BenjaminMoff/MixUS/code/diagrams/App_state_machine.png

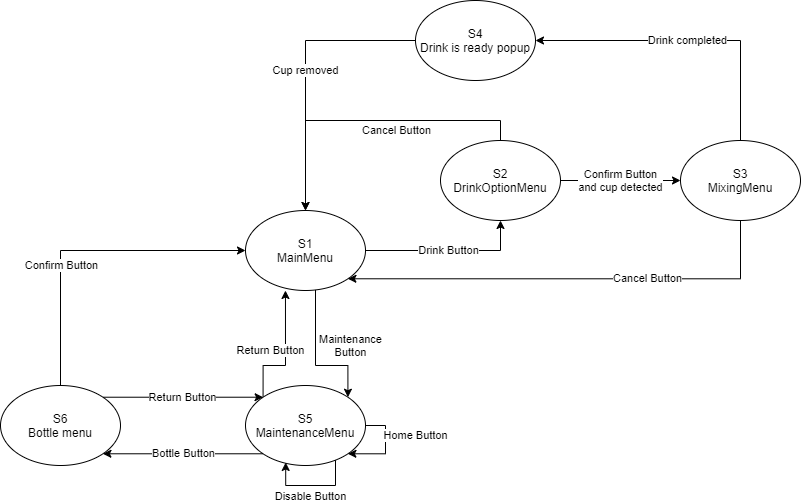
code/diagrams/App_state_machine.png
