BenjaminMoff/MixUS/code/diagrams/Datamodel_class_diagram.png

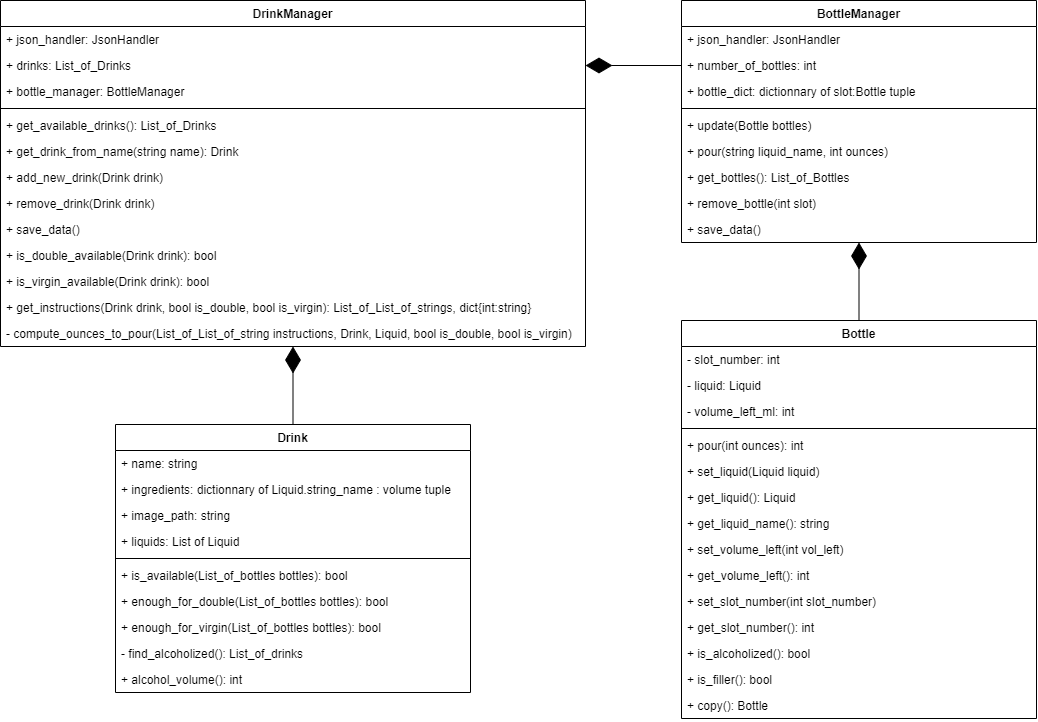
code/diagrams/Datamodel_class_diagram.png
