BenjaminMoff/MixUS/code/diagrams/SerialCommunication_sequence_diagram.png

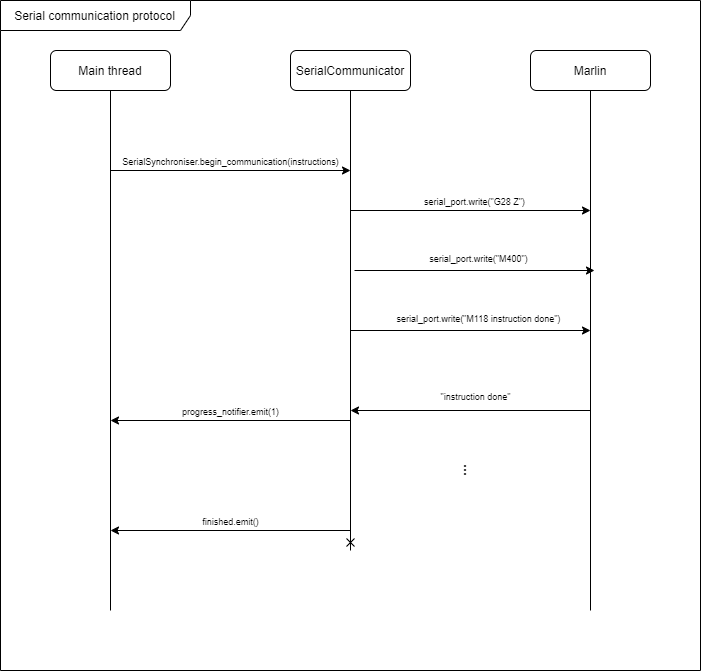
code/diagrams/SerialCommunication_sequence_diagram.png
