BenjaminMoff/MixUS/code/resources/bec-sucre.jpg

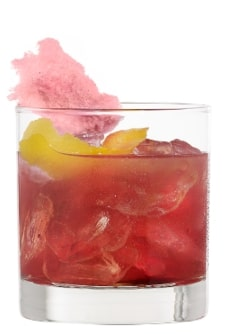
code/resources/bec-sucre.jpg
