BenjaminMoff/MixUS/code/resources/bleu-turquoise.jpg

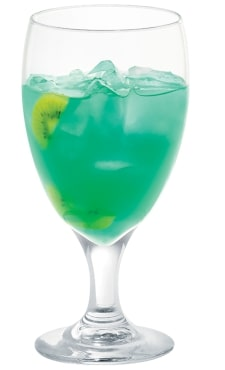
code/resources/bleu-turquoise.jpg
