BenjaminMoff/MixUS/code/resources/delice-gingembre.jpg

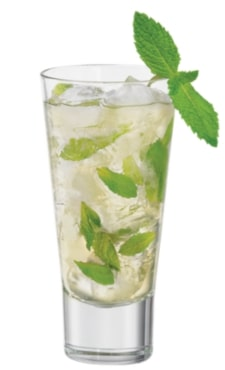
code/resources/delice-gingembre.jpg
