BenjaminMoff/MixUS/code/resources/gin-tonic.jpg

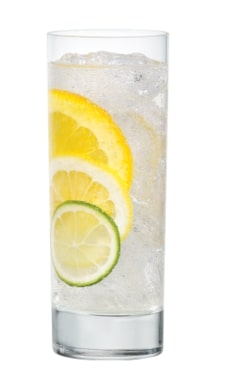
code/resources/gin-tonic.jpg
