BenjaminMoff/MixUS/code/resources/gingembre-etincellant.jpg

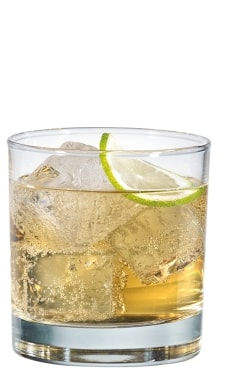
code/resources/gingembre-etincellant.jpg
