BenjaminMoff/MixUS/code/resources/long-island.jpg

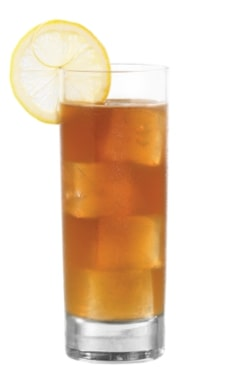
code/resources/long-island.jpg
