BenjaminMoff/MixUS/code/resources/margarita.jpg

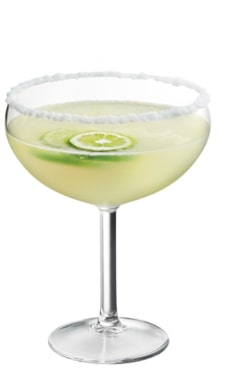
code/resources/margarita.jpg
