BenjaminMoff/MixUS/code/resources/mule-mexicaine.jpg

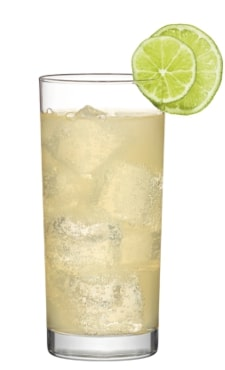
code/resources/mule-mexicaine.jpg
