BenjaminMoff/MixUS/code/resources/orange-fusion.jpg

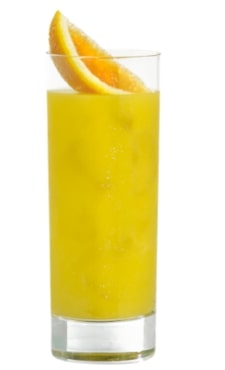
code/resources/orange-fusion.jpg
