BenjaminMoff/MixUS/code/resources/passion-bleue.jpg

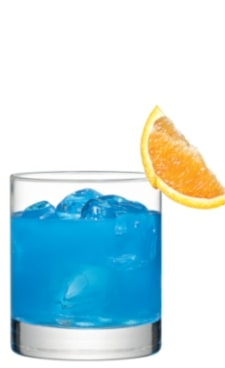
code/resources/passion-bleue.jpg
