BenjaminMoff/MixUS/code/resources/passion-ecarlate.jpg

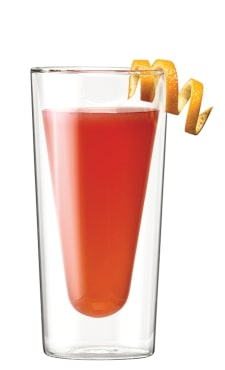
code/resources/passion-ecarlate.jpg
