BenjaminMoff/MixUS/code/resources/rhum-canneberge.jpg

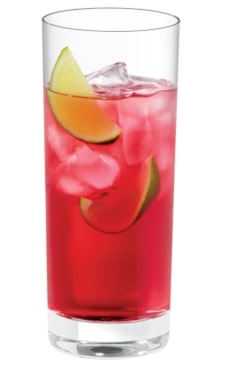
code/resources/rhum-canneberge.jpg
