BenjaminMoff/MixUS/code/resources/rhum-cola.jpg

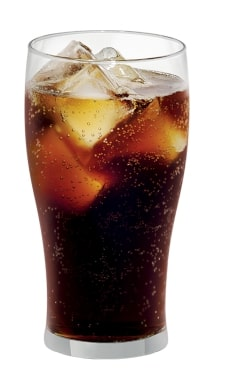
code/resources/rhum-cola.jpg
