BenjaminMoff/MixUS/code/resources/rhum-glace.jpg

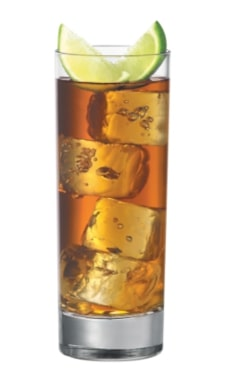
code/resources/rhum-glace.jpg
