BenjaminMoff/MixUS/code/resources/rhum_and_coke.jpg

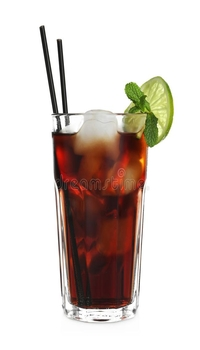
code/resources/rhum_and_coke.jpg
