BenjaminMoff/MixUS/code/resources/tequila-sunrise.jpg

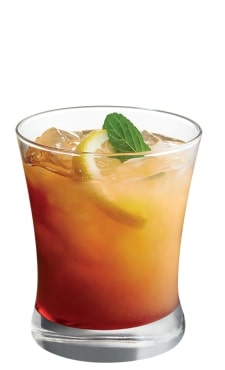
code/resources/tequila-sunrise.jpg
