BenjaminMoff/MixUS/Media Wiki/Home/Axis.png

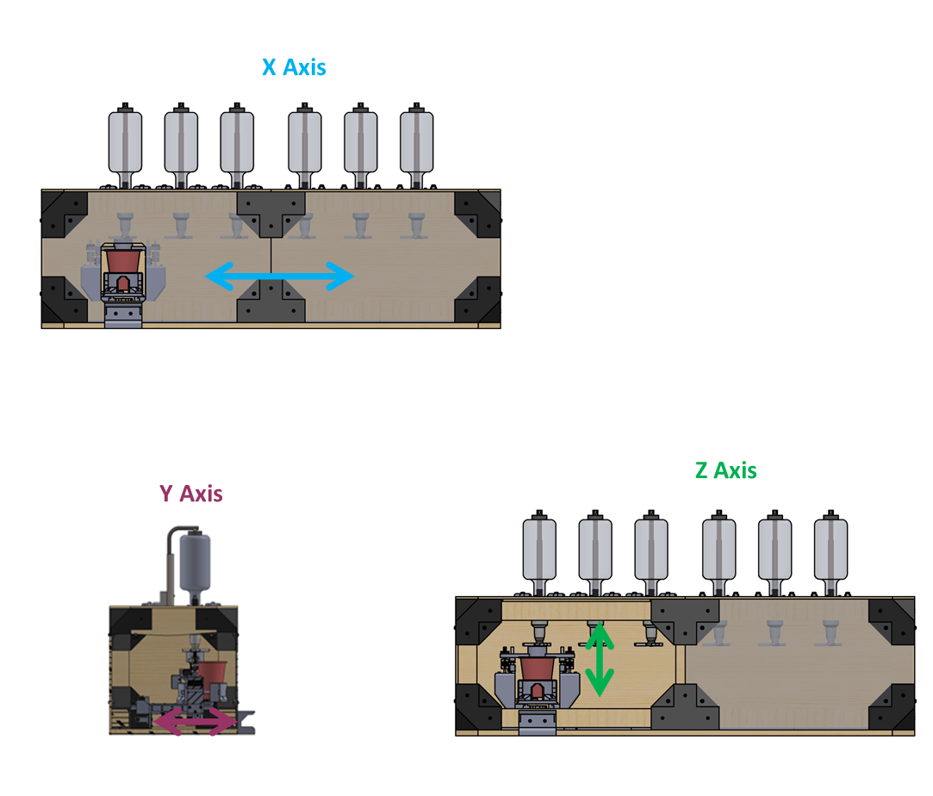
Media Wiki/Home/Axis.png
