BenjaminMoff/MixUS/Media Wiki/Putting it all together/Arduino_IDE_Terminal.gif

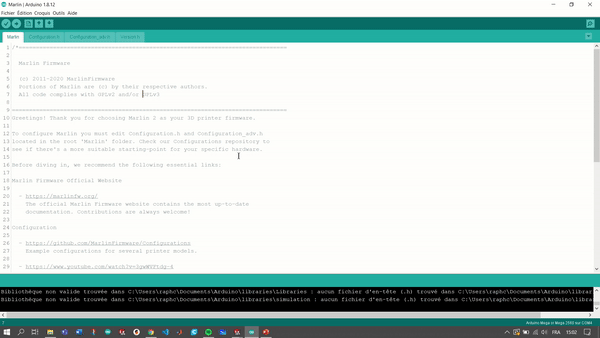
Media Wiki/Putting it all together/Arduino_IDE_Terminal.gif
