BenjaminMoff/MixUS/Media Wiki/Putting it all together/ElectronicConnections.png

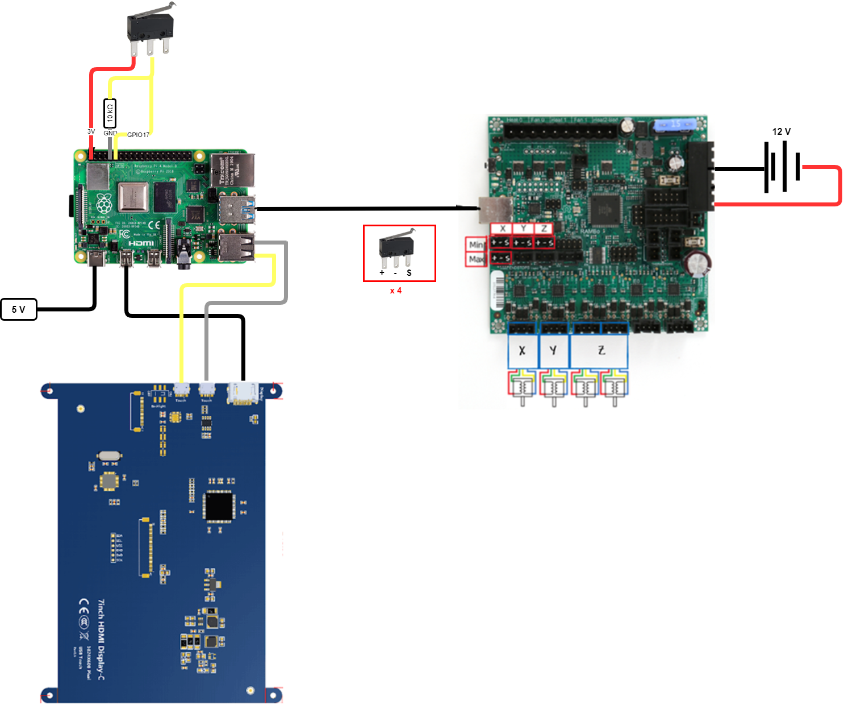
Media Wiki/Putting it all together/ElectronicConnections.png
