BenjaminMoff/MixUS/Mechanical Assembly/CAD/SolidWorks/Frame materials/Drawing/PNG/Drawing_Frame_Acrylic.PNG

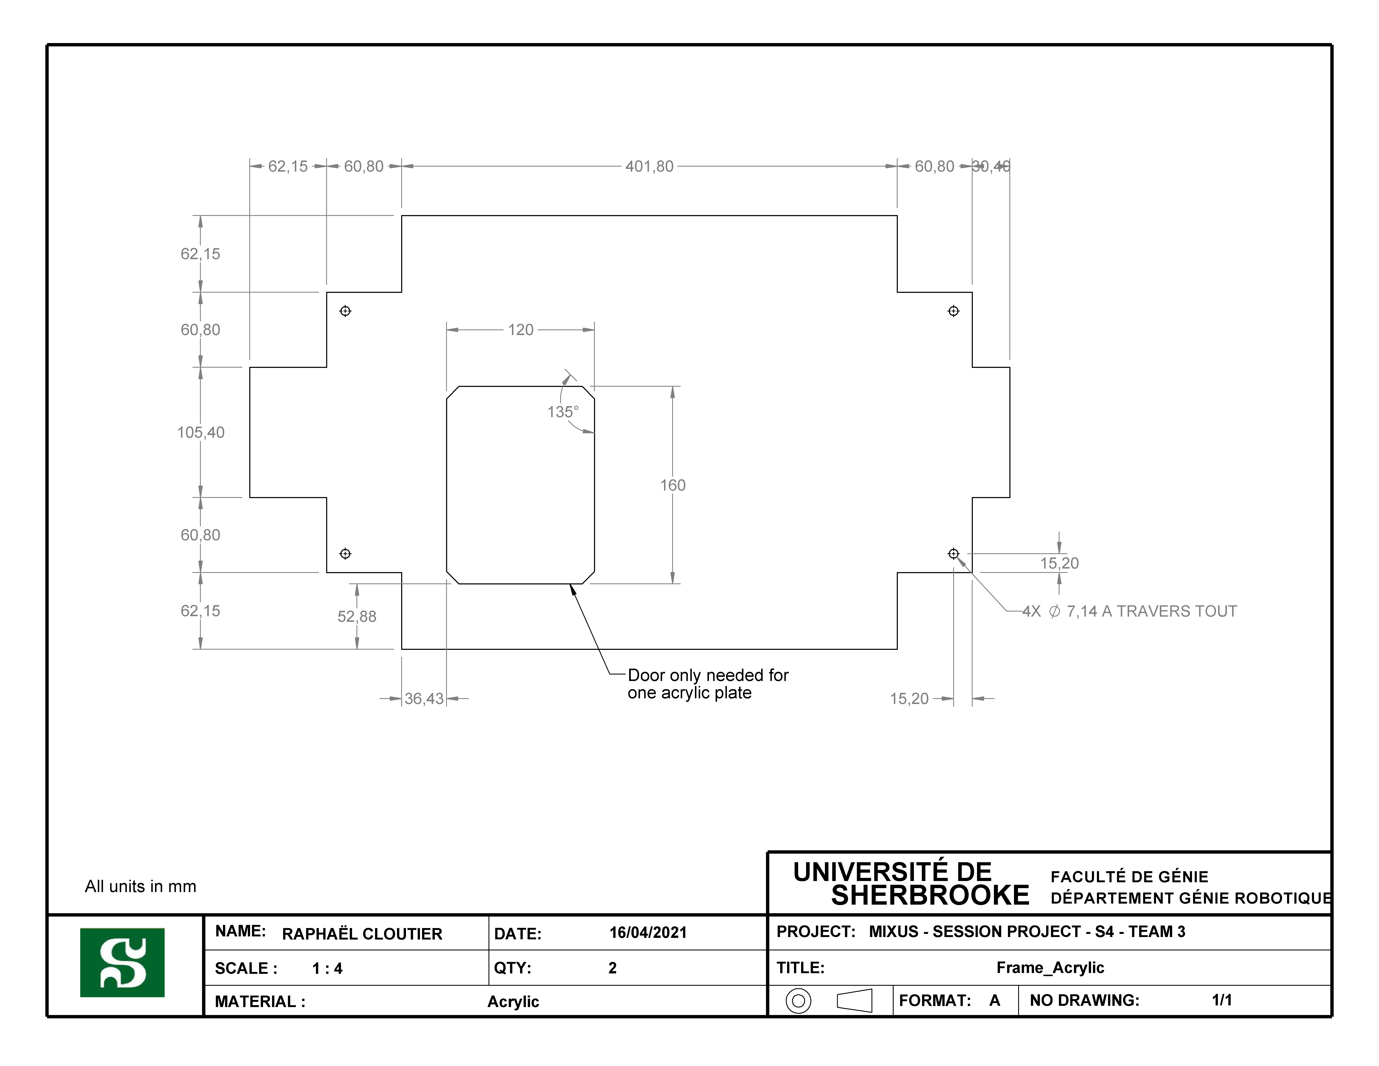
Mechanical Assembly/CAD/SolidWorks/Frame materials/Drawing/PNG/Drawing_Frame_Acrylic.PNG
