BenjaminMoff/MixUS/Mechanical Assembly/CAD/SolidWorks/Frame materials/Drawing/PNG/Drawing_Frame_Side_Plate.PNG

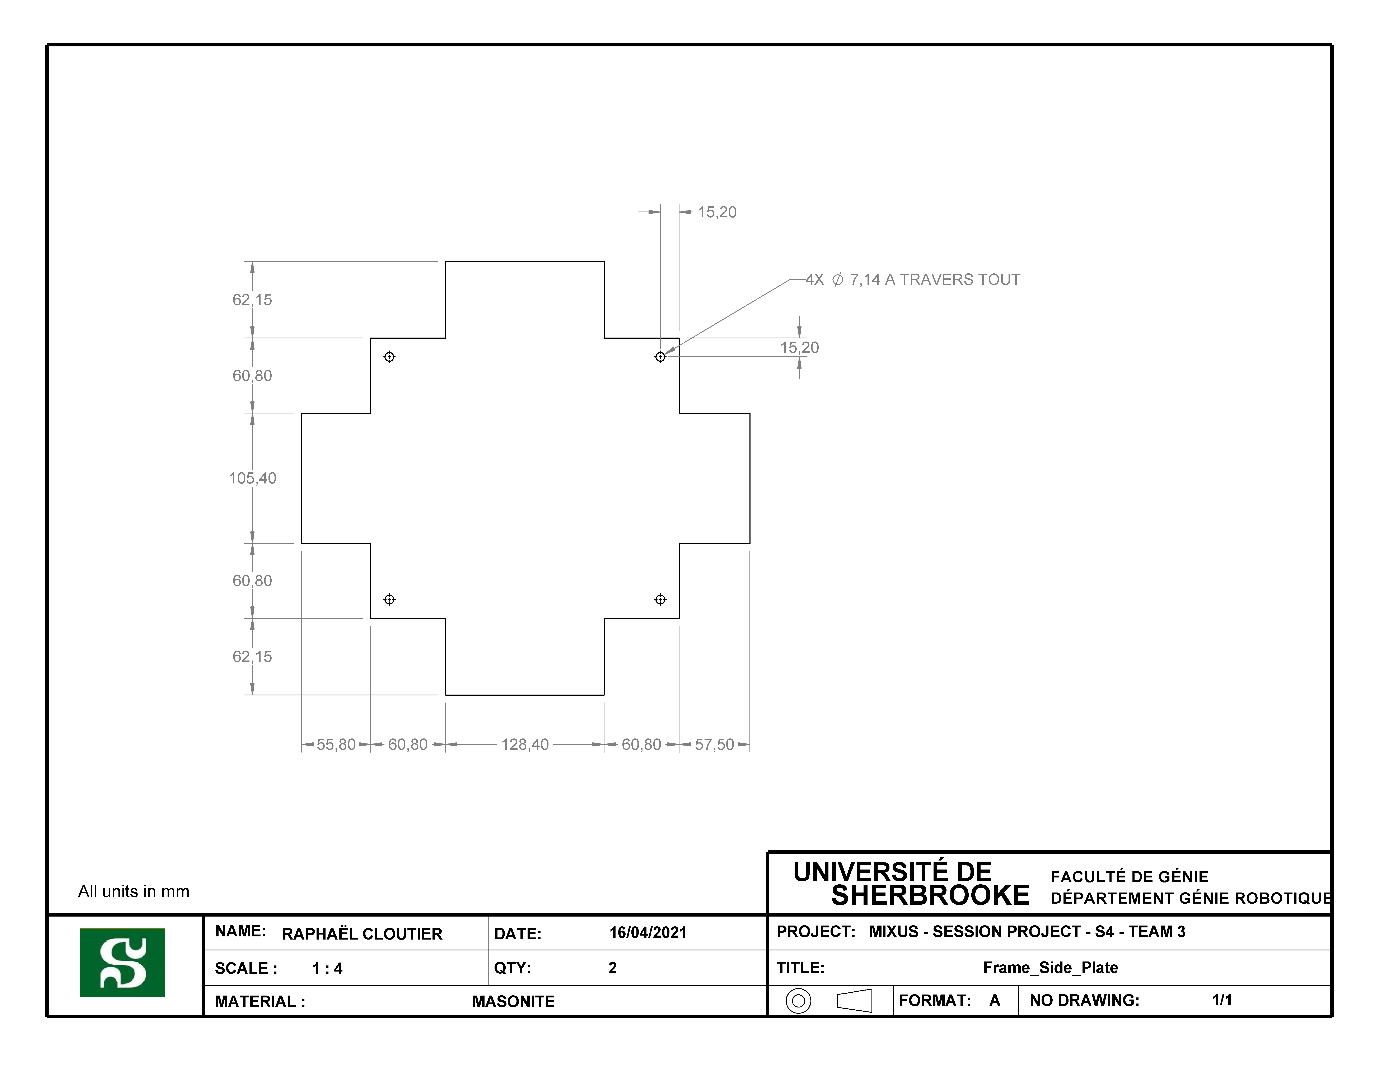
Mechanical Assembly/CAD/SolidWorks/Frame materials/Drawing/PNG/Drawing_Frame_Side_Plate.PNG
