BenjaminMoff/MixUS/Mechanical Assembly/CAD/SolidWorks/Frame materials/Drawing/PNG/Drawing_Frame_Top_Plate_A.PNG

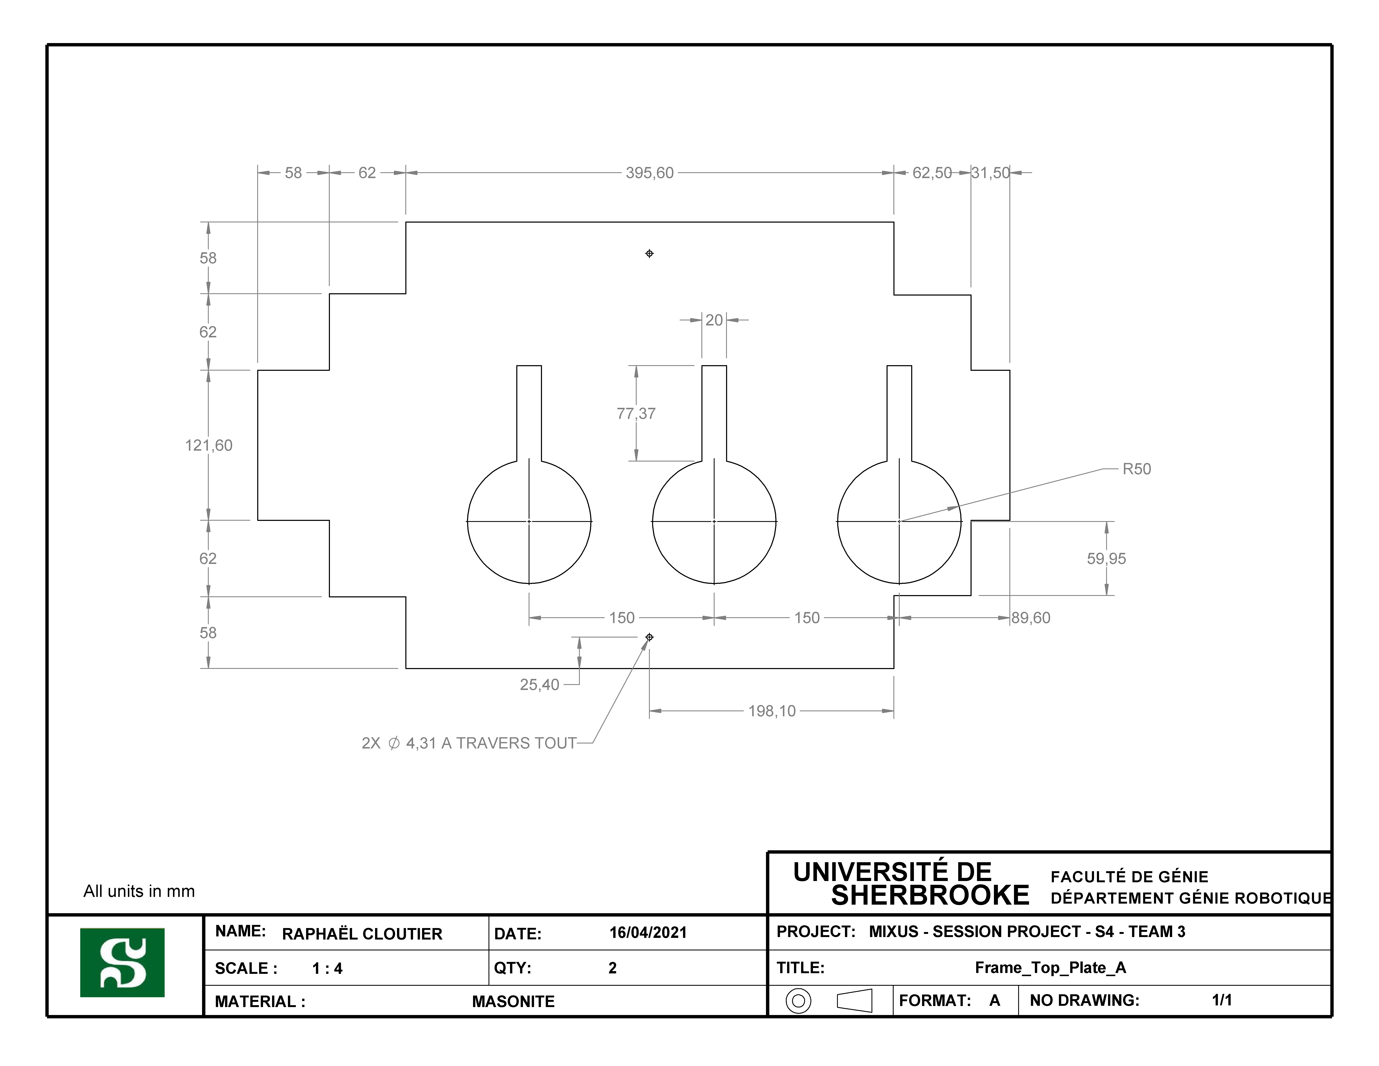
Mechanical Assembly/CAD/SolidWorks/Frame materials/Drawing/PNG/Drawing_Frame_Top_Plate_A.PNG
