BenjaminMoff/MixUS/Mechanical Assembly/CAD/SolidWorks/Frame materials/Drawing/PNG/Drawing_Frame_Top_Plate_B.PNG

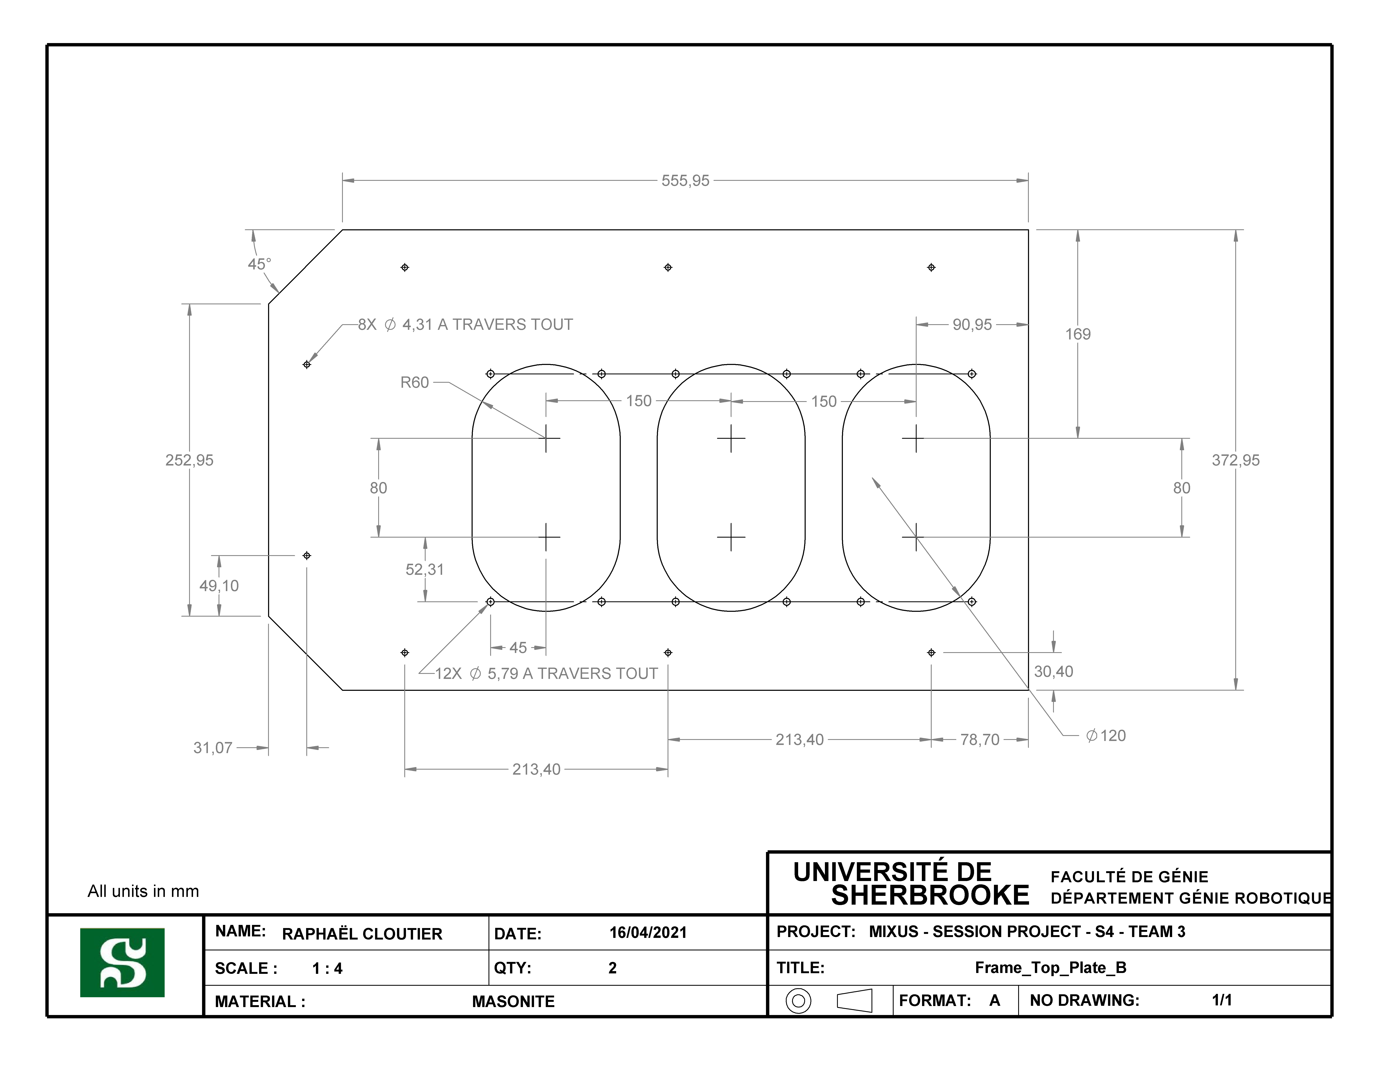
Mechanical Assembly/CAD/SolidWorks/Frame materials/Drawing/PNG/Drawing_Frame_Top_Plate_B.PNG
