BenjaminMoff/MixUS/Mechanical Assembly/CAD/SolidWorks/Insert/M2.5x3.4mm_insert.SLDPRT

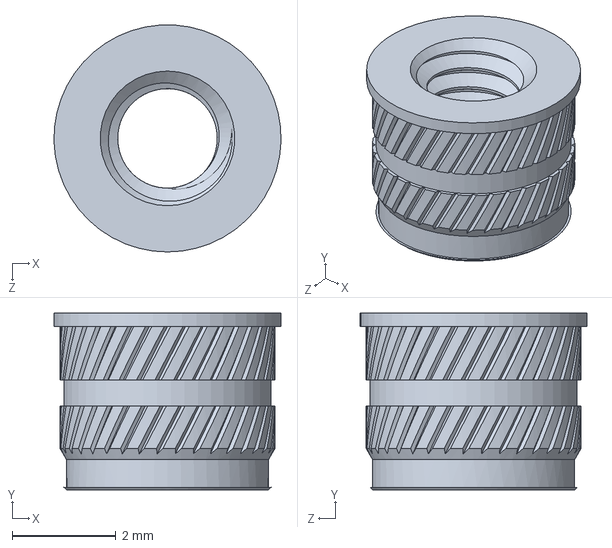
[picture p46: CAD file, 2021-04-10]
Mechanical Assembly/CAD/SolidWorks/Insert/M2.5x3.4mm_insert.SLDPRT
4.37 x 3.40 x 4.37 mm
