BenjaminMoff/MixUS/Mechanical Assembly/CAD/SolidWorks/Laser cut parts/DXF/Frame_Acrylic_Right.DXF

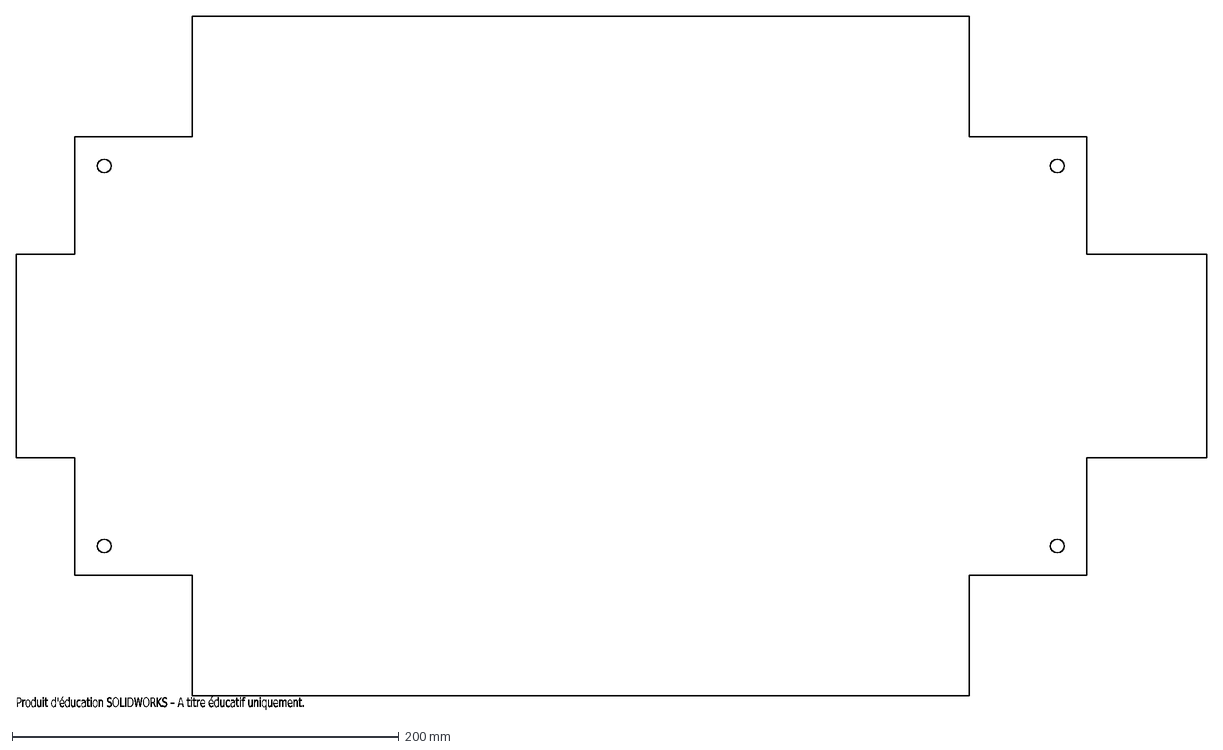
[picture p47: CAD file, 2021-04-10]
Mechanical Assembly/CAD/SolidWorks/Laser cut parts/DXF/Frame_Acrylic_Right.DXF
Produit d'éducation SOLIDWORKS – A titre éducatif uniquement.
