BenjaminMoff/MixUS/Mechanical Assembly/CAD/SolidWorks/Laser cut parts/STL/Frame_Acrylic.SLDPRT

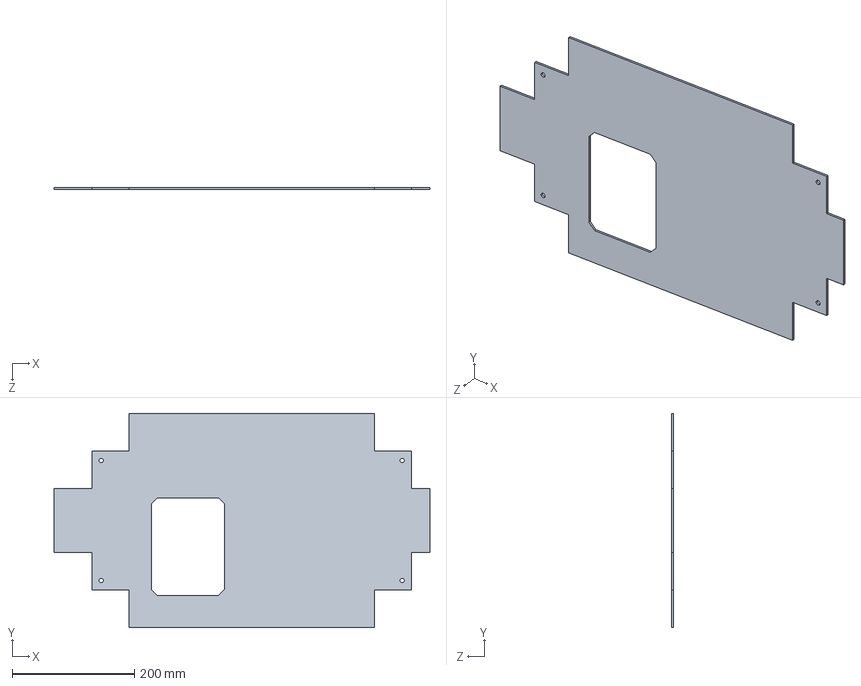
[picture p48: CAD file, 2021-04-10]
Mechanical Assembly/CAD/SolidWorks/Laser cut parts/STL/Frame_Acrylic.SLDPRT
616.0 x 351.3 x 3.30 mm
