BenjaminMoff/MixUS/Mechanical Assembly/CAD/SolidWorks/Nut/6_32_locknut.SLDPRT

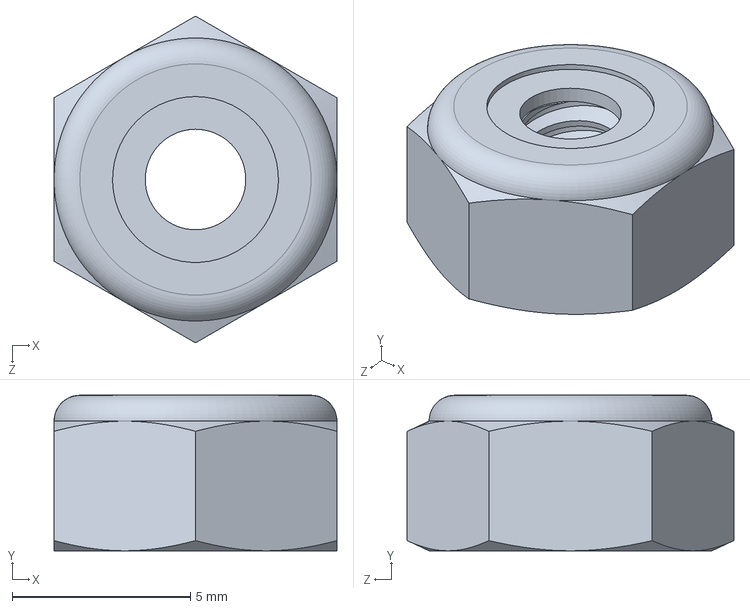
[picture p49: CAD file, 2021-04-10]
Mechanical Assembly/CAD/SolidWorks/Nut/6_32_locknut.SLDPRT
7.94 x 4.37 x 9.17 mm
