BenjaminMoff/MixUS/Mechanical Assembly/CAD/SolidWorks/Others/GT2_pulley.SLDPRT

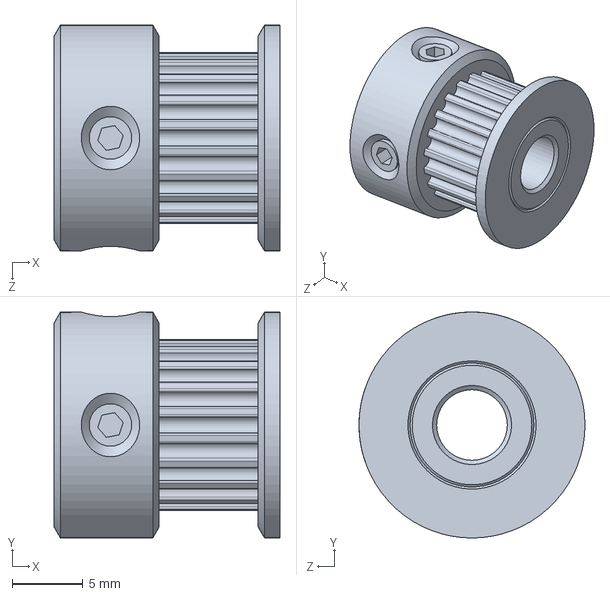
[picture p50: CAD file, 2021-04-10]
Mechanical Assembly/CAD/SolidWorks/Others/GT2_pulley.SLDPRT
16.0 x 16.0 x 16.0 mm
