BenjaminMoff/MixUS/Mechanical Assembly/CAD/SolidWorks/Printed parts/SolidWorks/BottleSup_Removable_Plate_A.SLDPRT

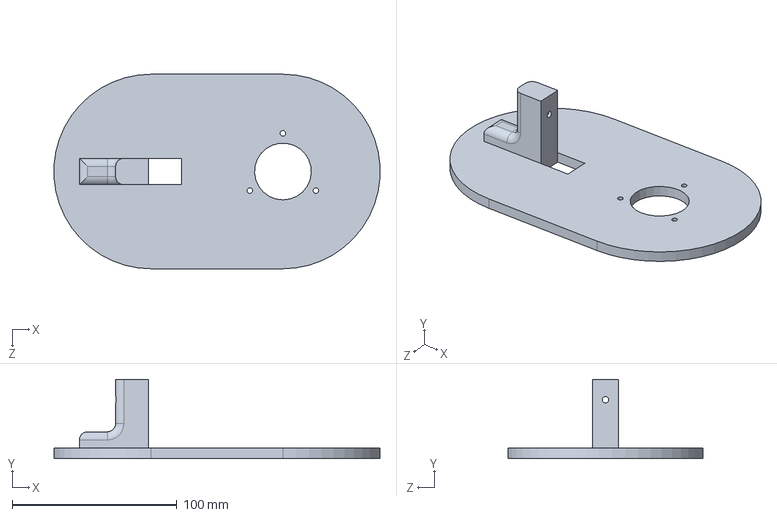
[picture p51: CAD file, 2021-04-10]
Mechanical Assembly/CAD/SolidWorks/Printed parts/SolidWorks/BottleSup_Removable_Plate_A.SLDPRT
197.7 x 48.2 x 118.0 mm
