BenjaminMoff/MixUS/Mechanical Assembly/CAD/SolidWorks/Electronic/40x40x10_DC_Fan.SLDPRT

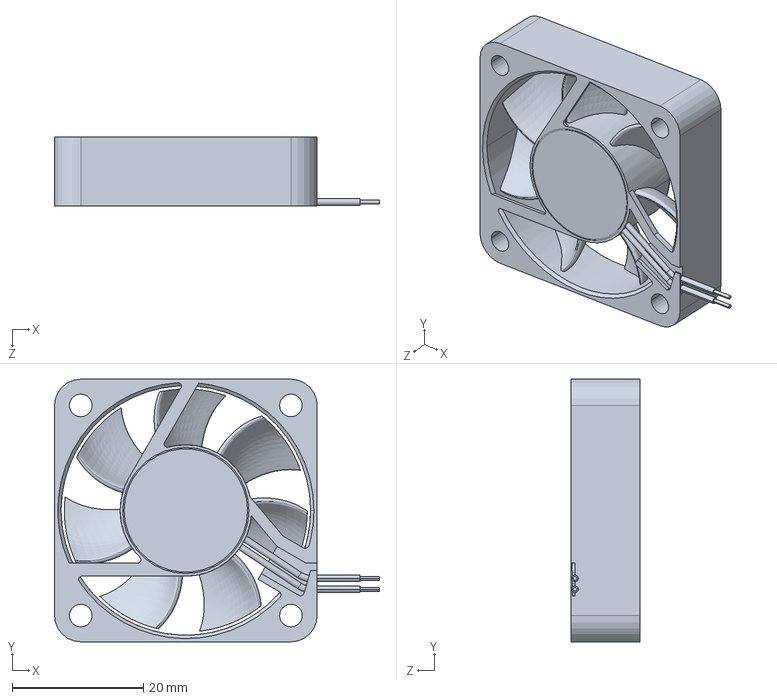
[picture p52: CAD file, 2021-04-10]
Mechanical Assembly/CAD/SolidWorks/Electronic/40x40x10_DC_Fan.SLDPRT
49.5 x 40.0 x 10.5 mm
