BenjaminMoff/MixUS/Mechanical Assembly/CAD/SolidWorks/Frame materials/Frame_top_plate_A.SLDPRT

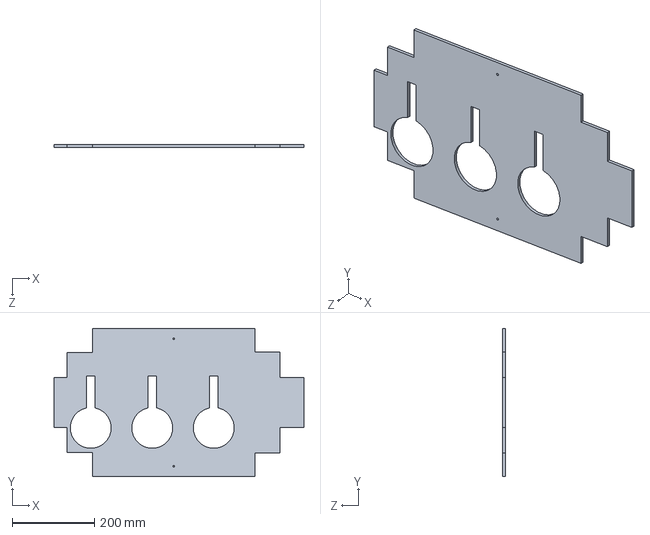
[picture p53: CAD file, 2021-04-10]
Mechanical Assembly/CAD/SolidWorks/Frame materials/Frame_top_plate_A.SLDPRT
609.6 x 361.6 x 6.35 mm
