BenjaminMoff/MixUS/Mechanical Assembly/CAD/SolidWorks/Laser cut parts/DXF/Frame_top_plate_A_Left.DXF

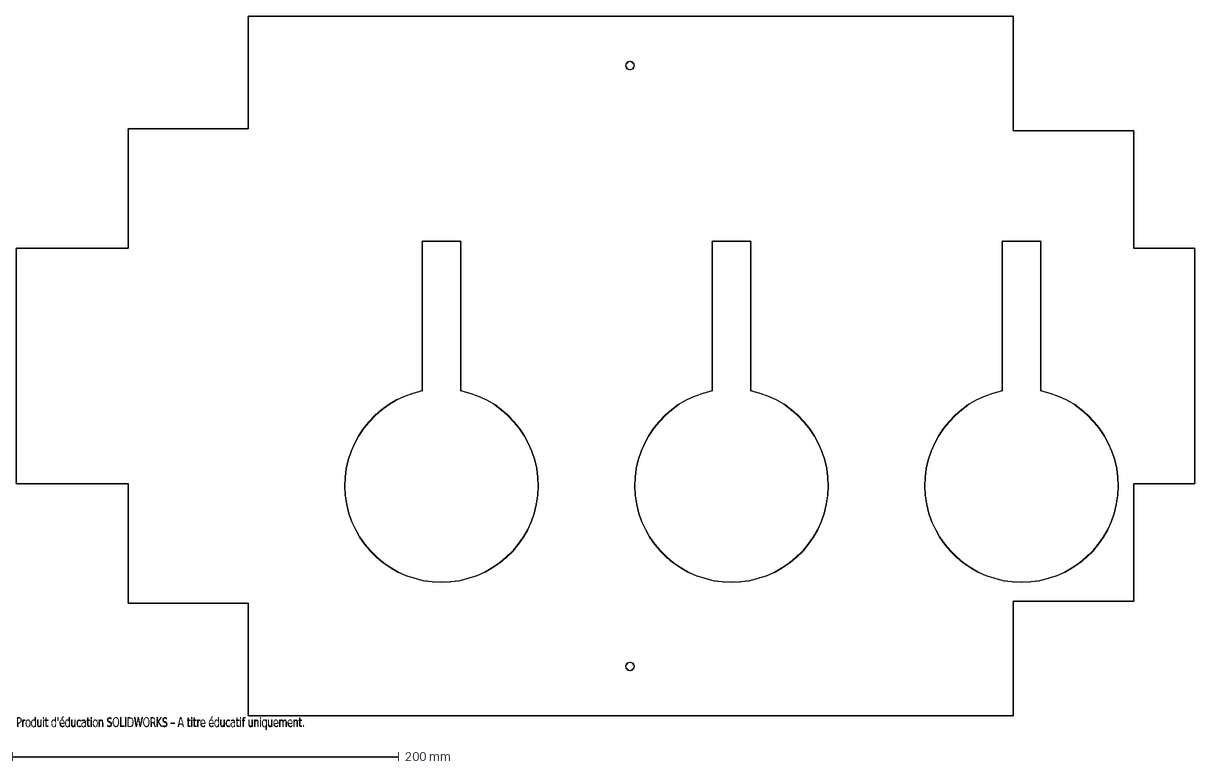
[picture p54: CAD file, 2021-04-10]
Mechanical Assembly/CAD/SolidWorks/Laser cut parts/DXF/Frame_top_plate_A_Left.DXF
Produit d'éducation SOLIDWORKS – A titre éducatif uniquement.
