BenjaminMoff/MixUS/Mechanical Assembly/CAD/SolidWorks/Others/Idler_pulley.SLDPRT

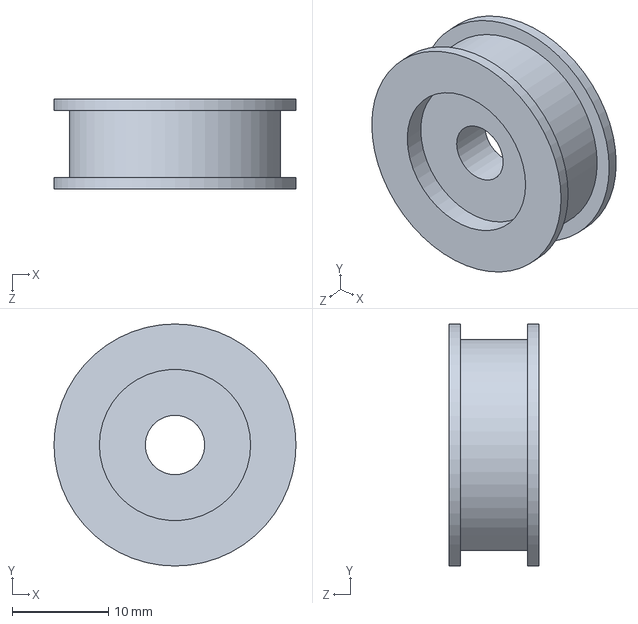
[picture p55: CAD file, 2021-04-10]
Mechanical Assembly/CAD/SolidWorks/Others/Idler_pulley.SLDPRT
25.2 x 25.2 x 9.40 mm
