BenjaminMoff/MixUS/Mechanical Assembly/CAD/SolidWorks/Printed parts/SolidWorks/Y_Support_rail.SLDPRT

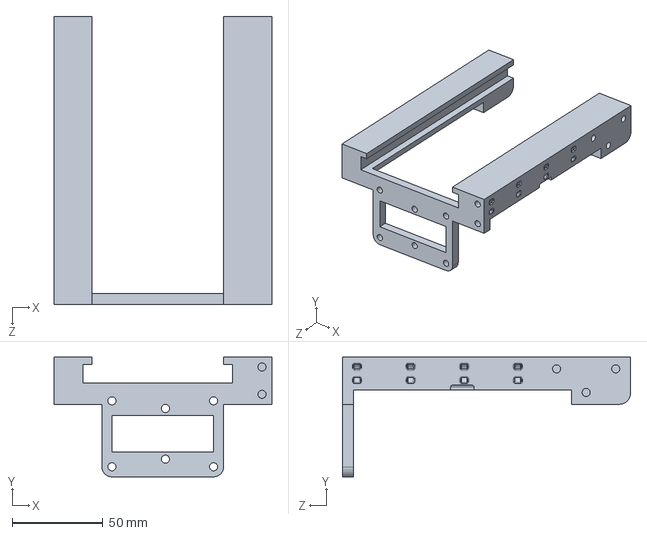
[picture p56: CAD file, 2021-04-10]
Mechanical Assembly/CAD/SolidWorks/Printed parts/SolidWorks/Y_Support_rail.SLDPRT
120.0 x 66.0 x 158.6 mm
