BenjaminMoff/MixUS/Mechanical Assembly/CAD/SolidWorks/Frame materials/Frame_Side_Plate.SLDPRT

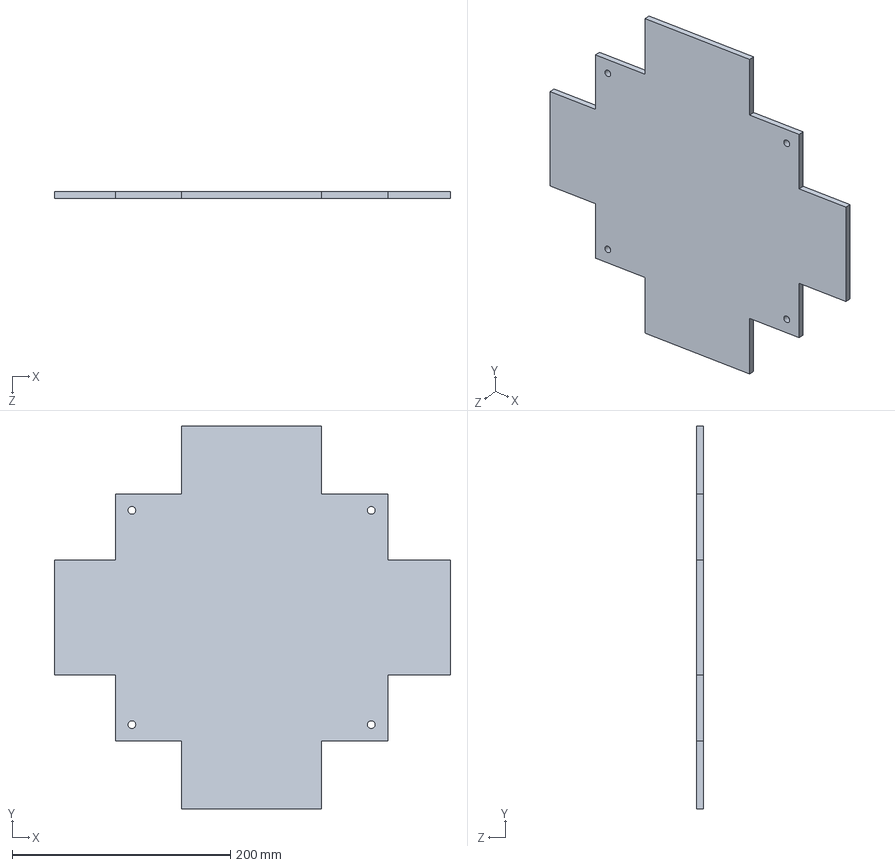
[picture p57: CAD file, 2021-04-10]
Mechanical Assembly/CAD/SolidWorks/Frame materials/Frame_Side_Plate.SLDPRT
363.3 x 351.3 x 6.35 mm
