BenjaminMoff/MixUS/Mechanical Assembly/CAD/SolidWorks/Others/Bottle_Support_TubeB.SLDPRT

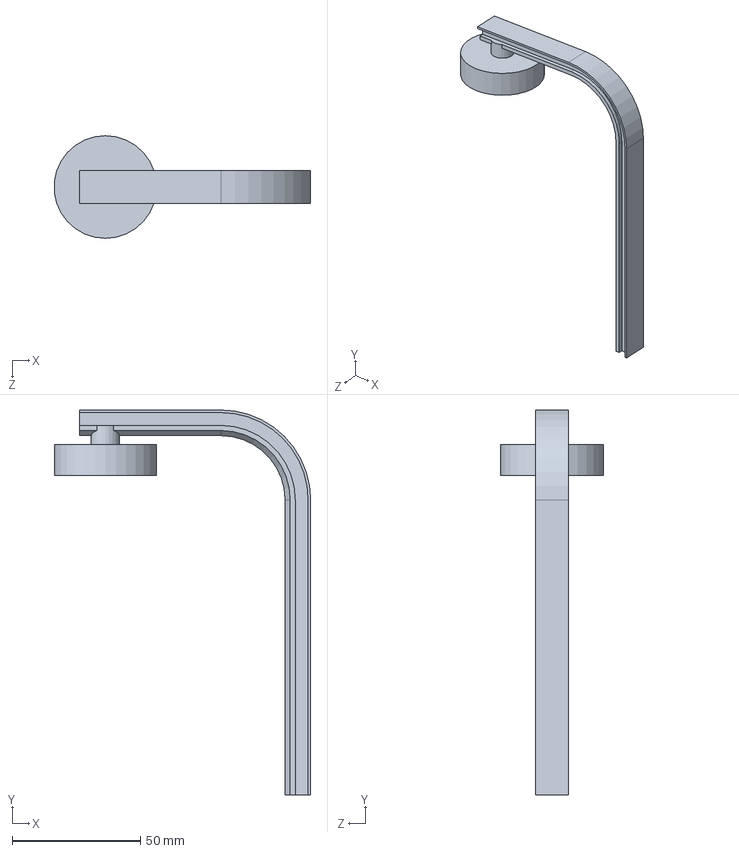
[picture p59: CAD file, 2021-04-10]
Mechanical Assembly/CAD/SolidWorks/Others/Bottle_Support_TubeB.SLDPRT
99.9 x 150.0 x 40.0 mm
