BenjaminMoff/MixUS/Mechanical Assembly/CAD/SolidWorks/Printed parts/SolidWorks/Y_Glass_holder.SLDPRT

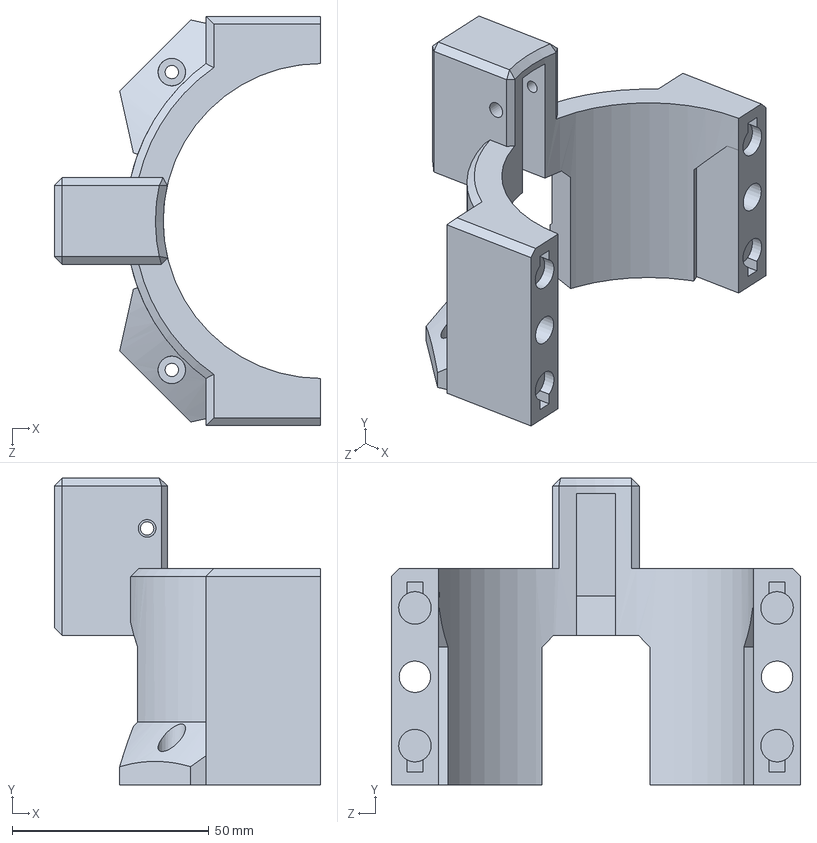
[picture p60: CAD file, 2021-04-10]
Mechanical Assembly/CAD/SolidWorks/Printed parts/SolidWorks/Y_Glass_holder.SLDPRT
67.7 x 78.0 x 104.0 mm
