BenjaminMoff/MixUS/Mechanical Assembly/CAD/SolidWorks/Printed parts/STL/Y_Wheel_bracket_symmetry.STL

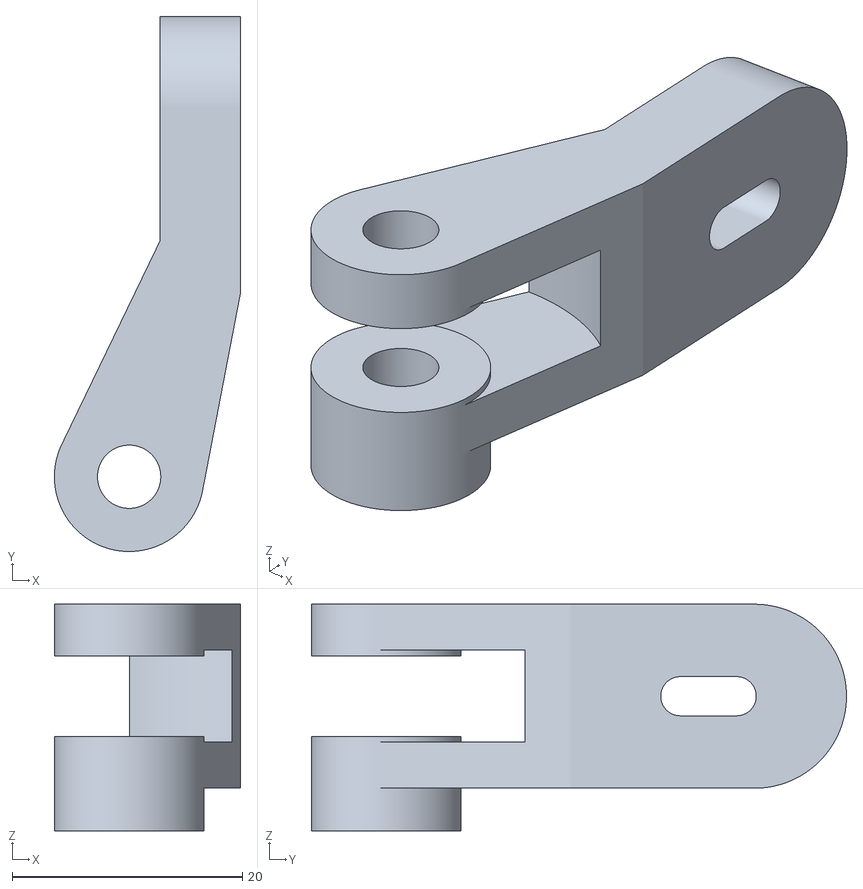
[picture p61: CAD file, 2021-04-10]
Mechanical Assembly/CAD/SolidWorks/Printed parts/STL/Y_Wheel_bracket_symmetry.STL
16.2 x 46.5 x 19.7
