BenjaminMoff/MixUS/Mechanical Assembly/CAD/SolidWorks/Electronic/Nema17.SLDPRT

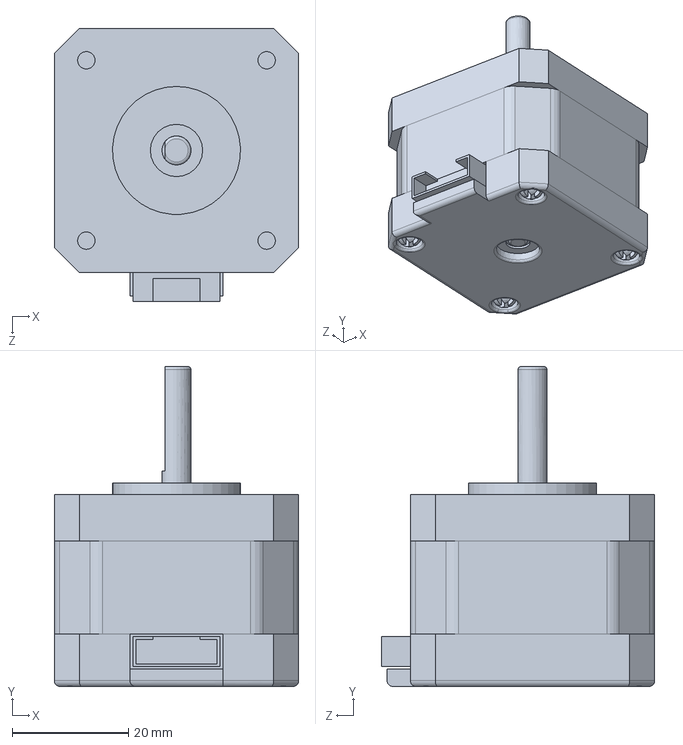
[picture p62: CAD file, 2021-04-10]
Mechanical Assembly/CAD/SolidWorks/Electronic/Nema17.SLDPRT
42.0 x 55.0 x 47.0 mm
