BenjaminMoff/MixUS/Mechanical Assembly/CAD/SolidWorks/Frame materials/Frame_Back_Plate.SLDPRT

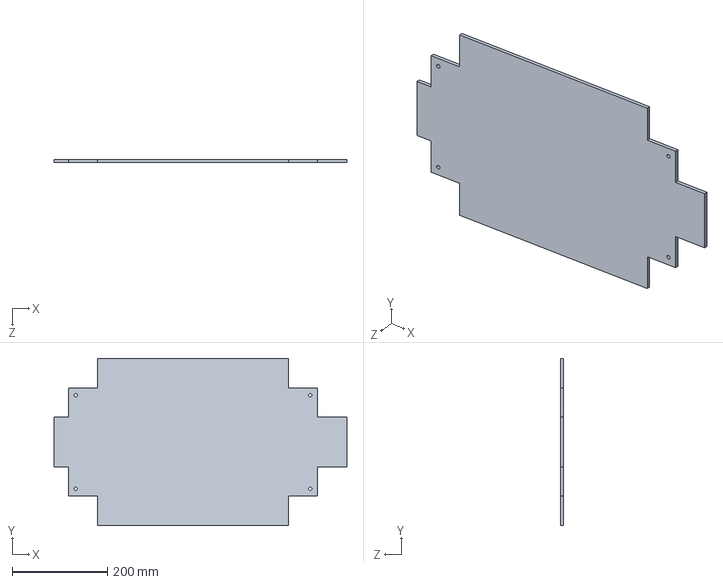
[picture p63: CAD file, 2021-04-10]
Mechanical Assembly/CAD/SolidWorks/Frame materials/Frame_Back_Plate.SLDPRT
616.0 x 351.3 x 6.35 mm
