BenjaminMoff/MixUS/Mechanical Assembly/CAD/SolidWorks/Laser cut parts/DXF/Frame_top_plate_B_Left.DXF

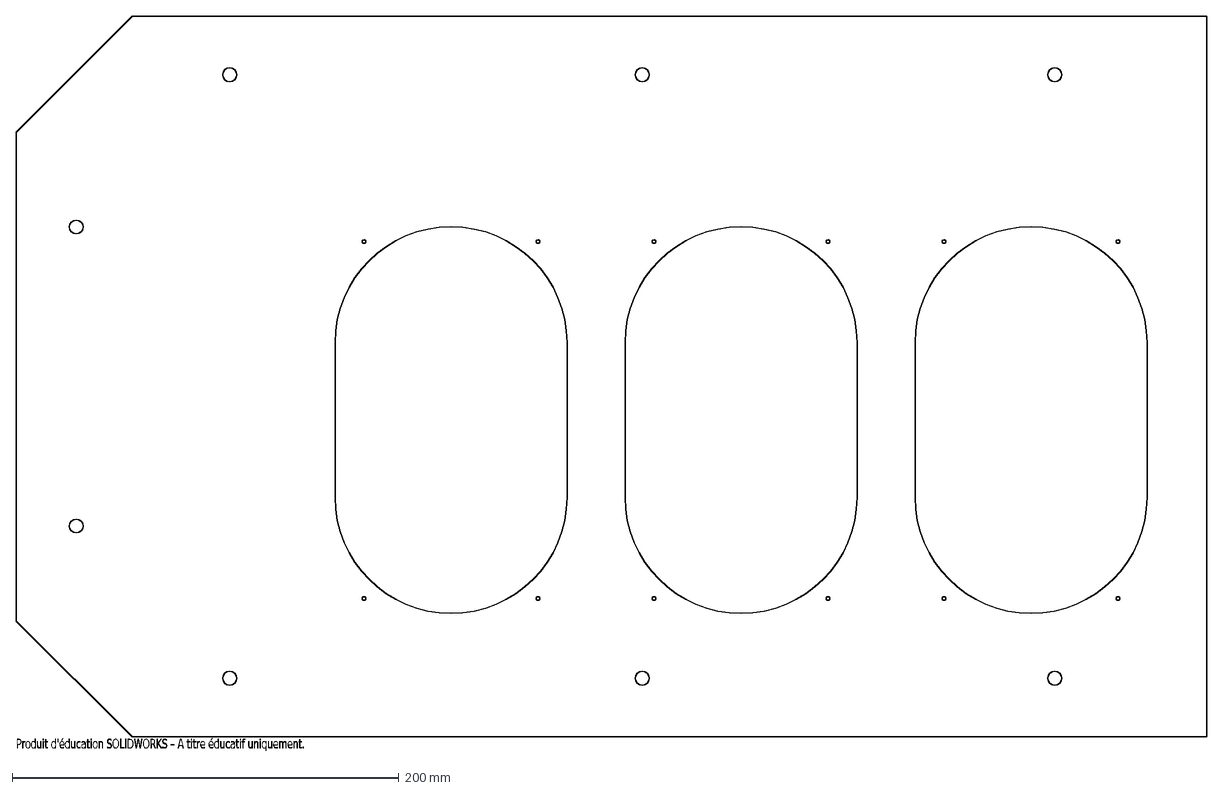
[picture p64: CAD file, 2021-04-10]
Mechanical Assembly/CAD/SolidWorks/Laser cut parts/DXF/Frame_top_plate_B_Left.DXF
Produit d'éducation SOLIDWORKS – A titre éducatif uniquement.
