BenjaminMoff/MixUS/Mechanical Assembly/CAD/SolidWorks/Printed parts/SolidWorks/X_V_Wheel_spacer.SLDPRT

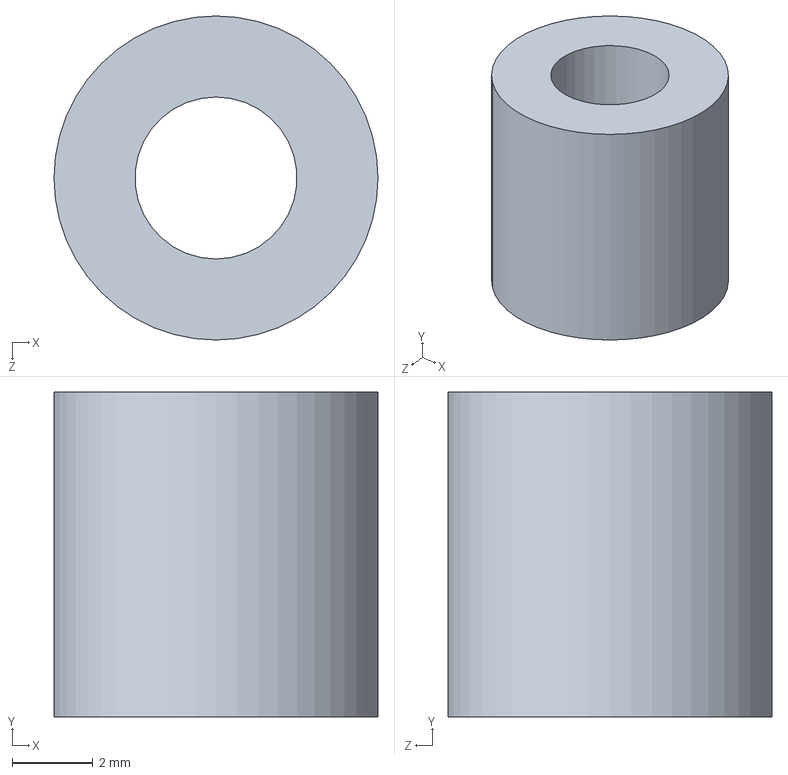
[picture p65: CAD file, 2021-04-10]
Mechanical Assembly/CAD/SolidWorks/Printed parts/SolidWorks/X_V_Wheel_spacer.SLDPRT
8.00 x 8.02 x 8.00 mm
