BenjaminMoff/MixUS/Mechanical Assembly/CAD/SolidWorks/Electronic/Extra_long_male_header_pin.SLDPRT

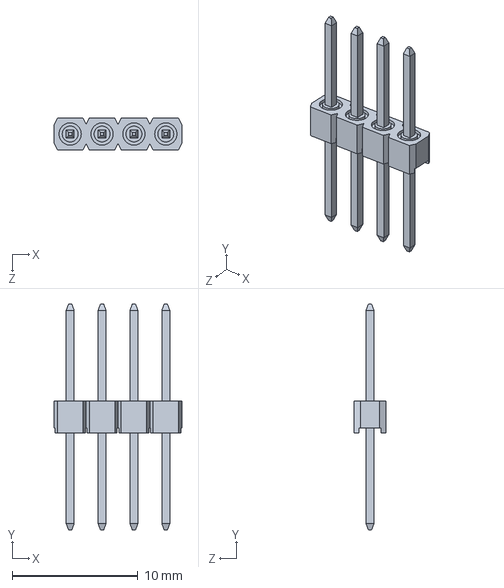
[picture p66: CAD file, 2021-04-10]
Mechanical Assembly/CAD/SolidWorks/Electronic/Extra_long_male_header_pin.SLDPRT
10.2 x 18.0 x 2.54 mm
