BenjaminMoff/MixUS/Mechanical Assembly/CAD/SolidWorks/Laser cut parts/DXF/Frame_Side_Plate.DXF

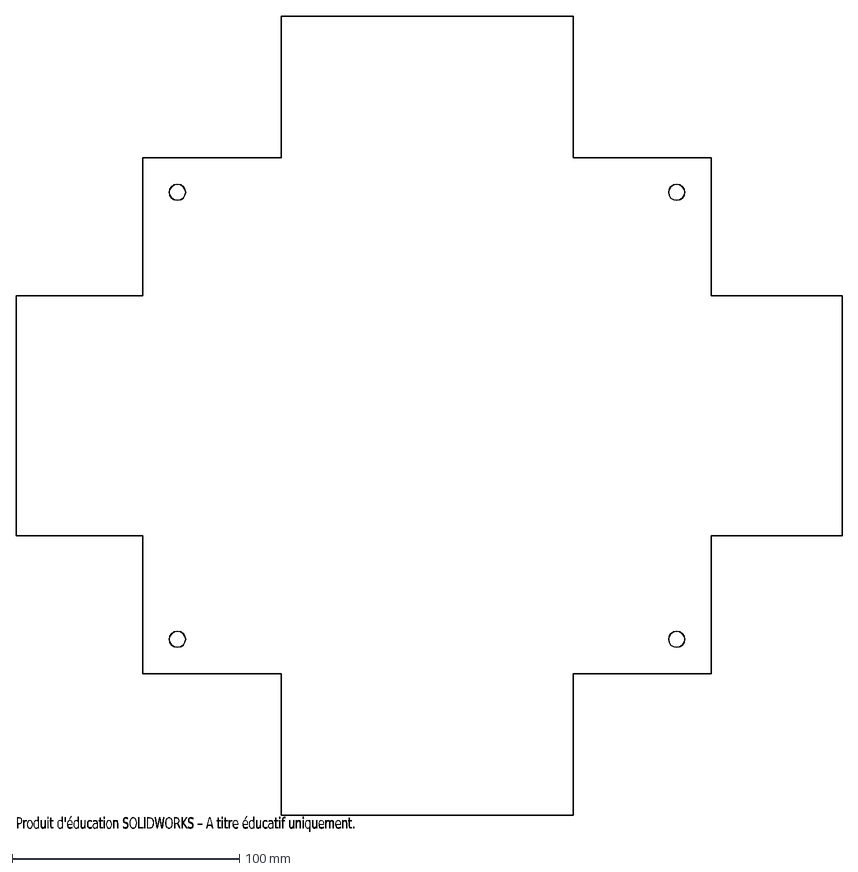
[picture p67: CAD file, 2021-04-10]
Mechanical Assembly/CAD/SolidWorks/Laser cut parts/DXF/Frame_Side_Plate.DXF
Produit d'éducation SOLIDWORKS – A titre éducatif uniquement.
