BenjaminMoff/MixUS/Mechanical Assembly/CAD/SolidWorks/Printed parts/SolidWorks/Y_Extern_slider_support.SLDPRT

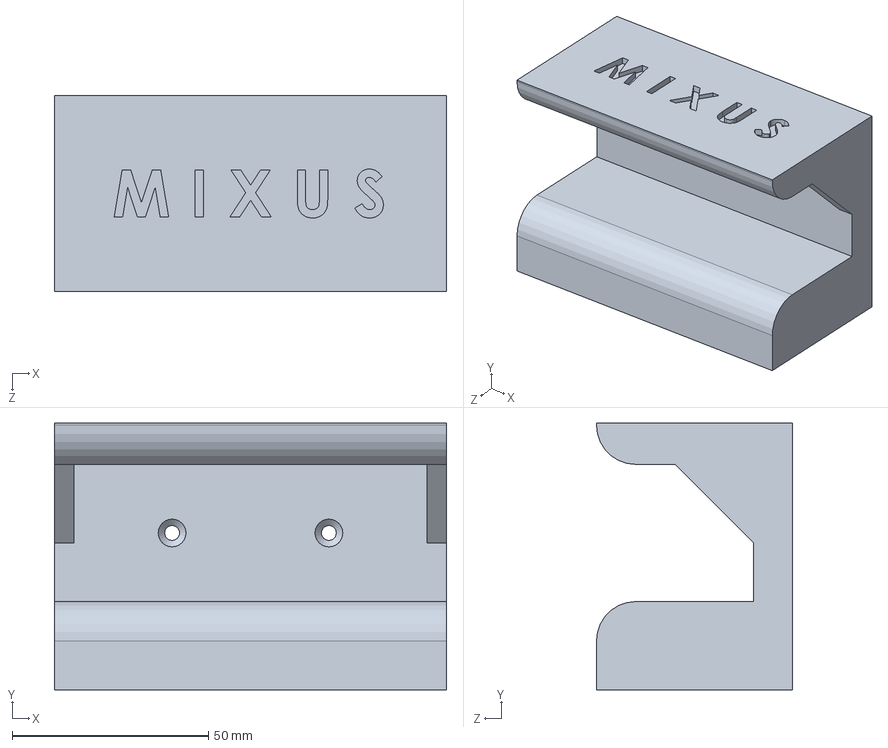
[picture p68: CAD file, 2021-04-10]
Mechanical Assembly/CAD/SolidWorks/Printed parts/SolidWorks/Y_Extern_slider_support.SLDPRT
100.0 x 68.0 x 50.0 mm
