BenjaminMoff/MixUS/Mechanical Assembly/CAD/SolidWorks/Printed parts/STL/Frame_Corner_Wood_Side_symmetry.STL

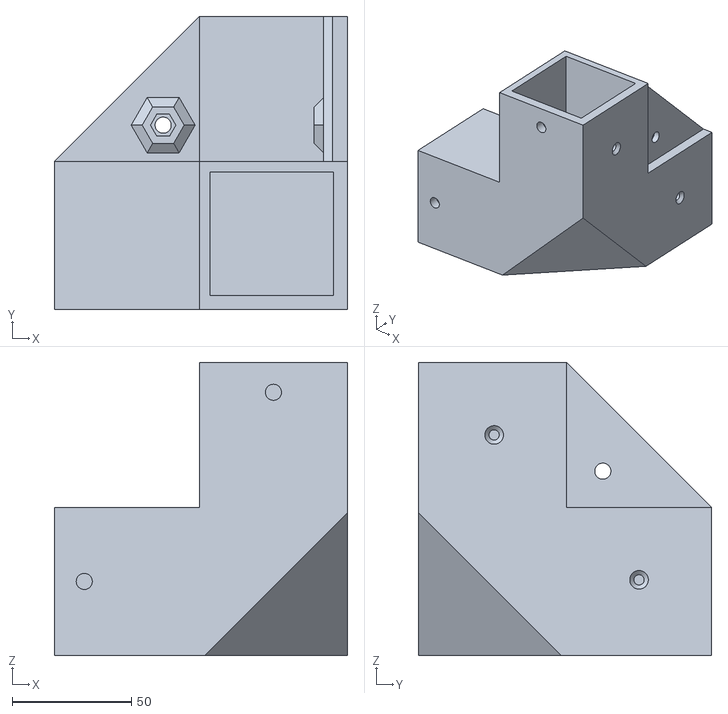
[picture p69: CAD file, 2021-04-10]
Mechanical Assembly/CAD/SolidWorks/Printed parts/STL/Frame_Corner_Wood_Side_symmetry.STL
123.0 x 123.0 x 123.0
