BenjaminMoff/MixUS/Mechanical Assembly/CAD/SolidWorks/Frame materials/Frame_top_plate_B.SLDPRT

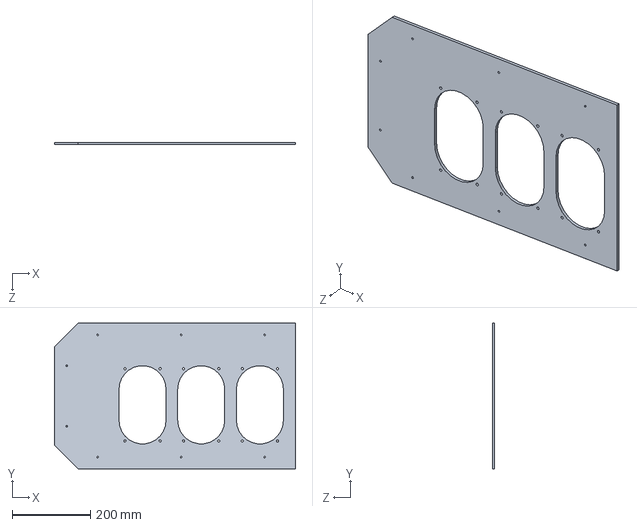
[picture p70: CAD file, 2021-04-10]
Mechanical Assembly/CAD/SolidWorks/Frame materials/Frame_top_plate_B.SLDPRT
616.0 x 372.9 x 6.35 mm
