BenjaminMoff/MixUS/Mechanical Assembly/CAD/SolidWorks/Others/5_to_8_mm_coupler.SLDPRT

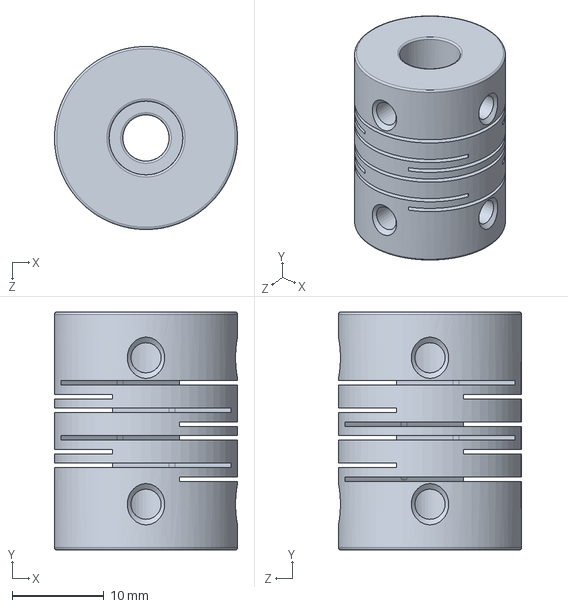
[picture p72: CAD file, 2021-04-10]
Mechanical Assembly/CAD/SolidWorks/Others/5_to_8_mm_coupler.SLDPRT
20.0 x 26.0 x 20.0 mm
