BenjaminMoff/MixUS/Mechanical Assembly/CAD/SolidWorks/Printed parts/SolidWorks/Y_Glass_Holder_Rod.SLDPRT

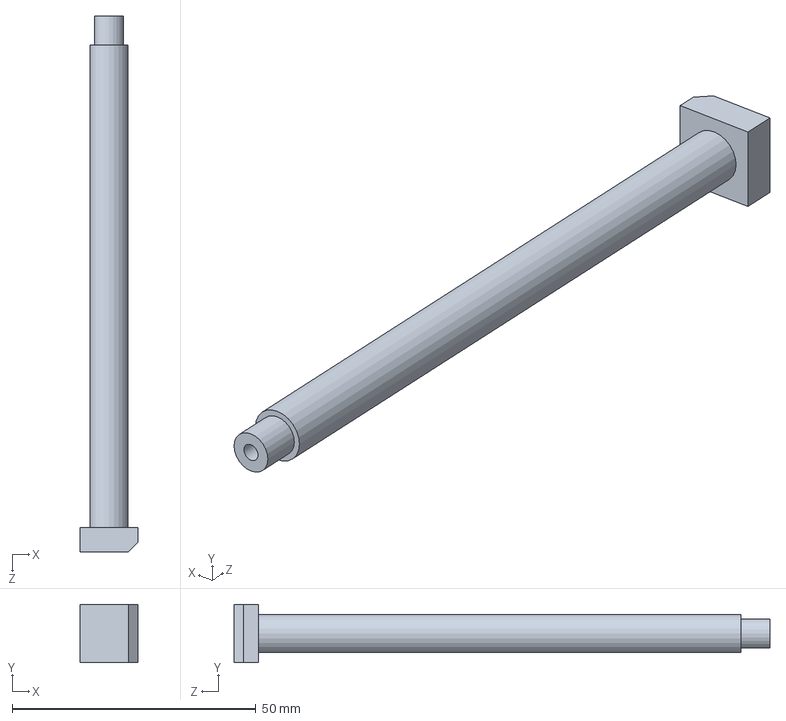
[picture p73: CAD file, 2021-04-10]
Mechanical Assembly/CAD/SolidWorks/Printed parts/SolidWorks/Y_Glass_Holder_Rod.SLDPRT
12.0 x 12.0 x 110.0 mm
