BenjaminMoff/MixUS/Mechanical Assembly/CAD/SolidWorks/Printed parts/STL/Frame_Top_Center_Beam_Bracket_plexi_side.STL

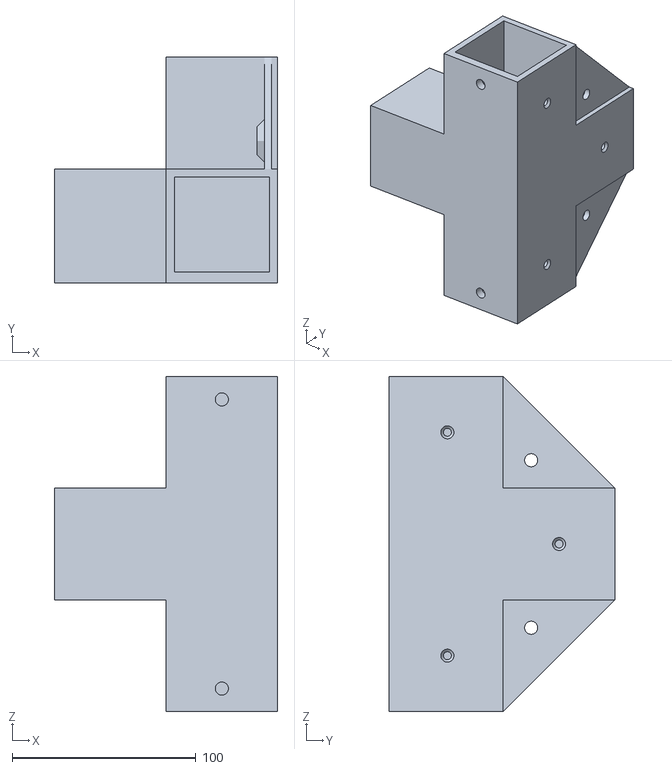
[picture p74: CAD file, 2021-04-10]
Mechanical Assembly/CAD/SolidWorks/Printed parts/STL/Frame_Top_Center_Beam_Bracket_plexi_side.STL
121.6 x 123.0 x 182.4
