BenjaminMoff/MixUS/Mechanical Assembly/CAD/SolidWorks/Frame materials/Frame_Bottom_Plate.SLDPRT

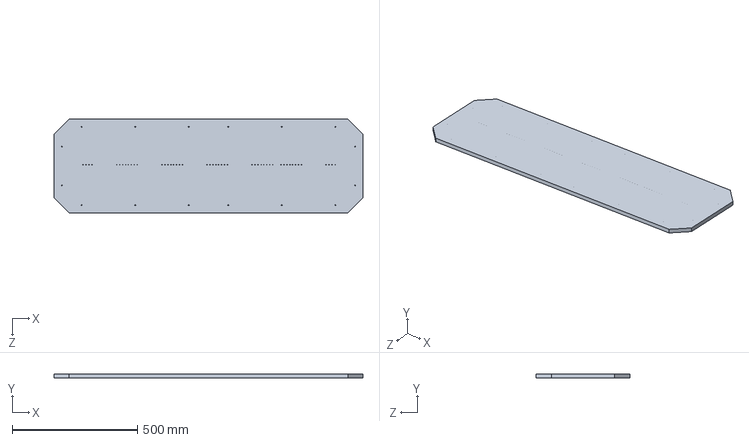
[picture p75: CAD file, 2021-04-10]
Mechanical Assembly/CAD/SolidWorks/Frame materials/Frame_Bottom_Plate.SLDPRT
1231.9 x 15.9 x 372.9 mm
