BenjaminMoff/MixUS/Mechanical Assembly/CAD/SolidWorks/Others/608zz_ball_bearing.SLDPRT

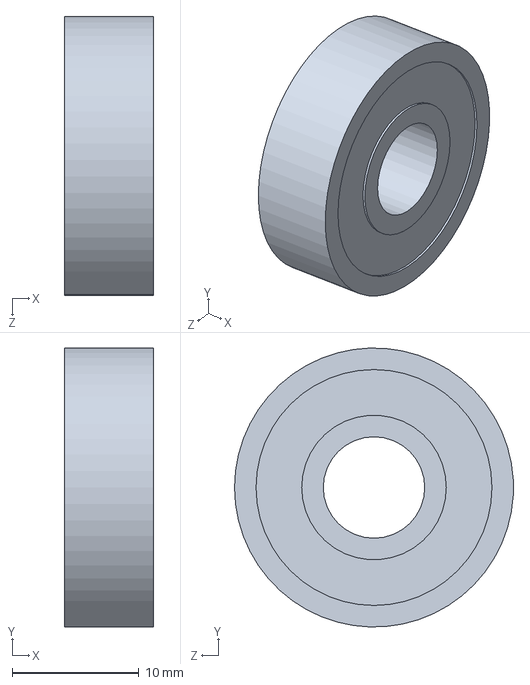
[picture p77: CAD file, 2021-04-10]
Mechanical Assembly/CAD/SolidWorks/Others/608zz_ball_bearing.SLDPRT
7.00 x 22.0 x 22.0 mm
