BenjaminMoff/MixUS/Mechanical Assembly/CAD/SolidWorks/Printed parts/SolidWorks/Z_Pusher.SLDPRT

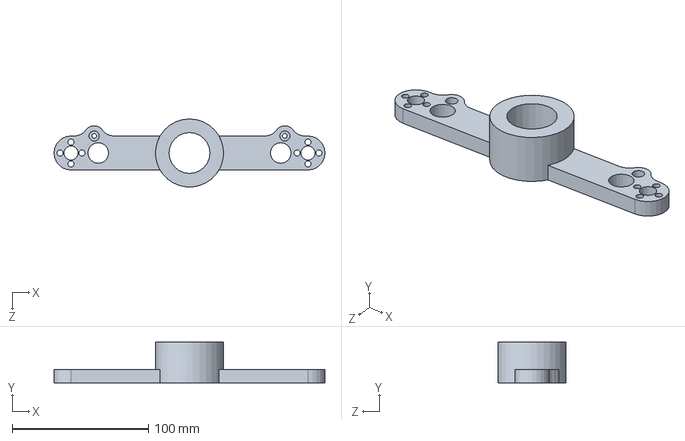
[picture p78: CAD file, 2021-04-10]
Mechanical Assembly/CAD/SolidWorks/Printed parts/SolidWorks/Z_Pusher.SLDPRT
199.0 x 30.0 x 50.0 mm
