BenjaminMoff/MixUS/Mechanical Assembly/CAD/SolidWorks/Printed parts/SolidWorks/Y_Glass_Holder_Rod_Stopper.SLDPRT

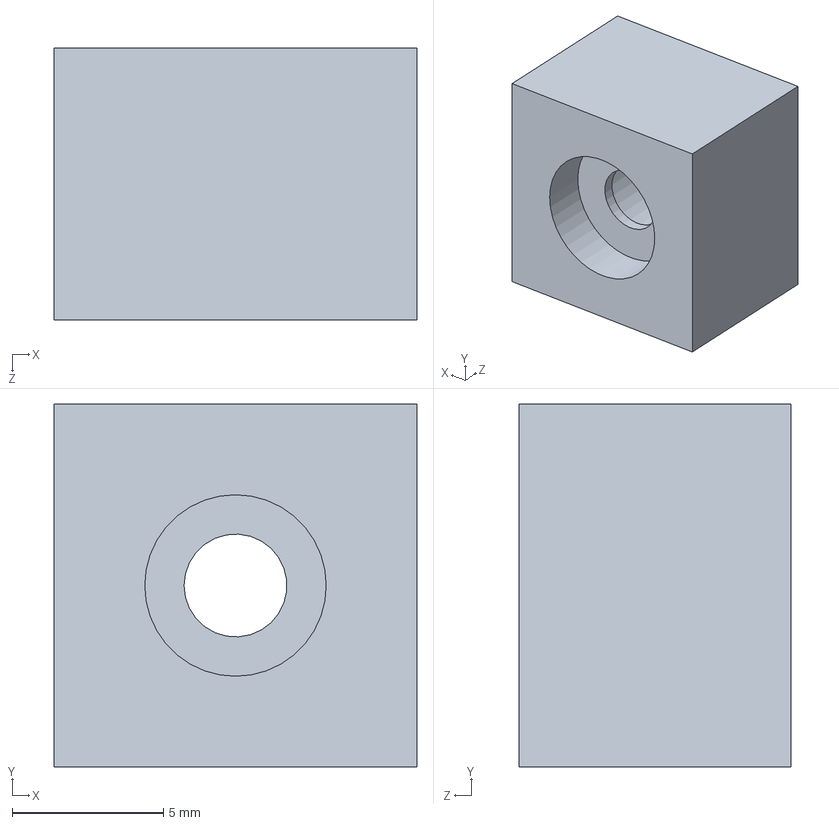
[picture p79: CAD file, 2021-04-10]
Mechanical Assembly/CAD/SolidWorks/Printed parts/SolidWorks/Y_Glass_Holder_Rod_Stopper.SLDPRT
12.0 x 12.0 x 9.00 mm
