BenjaminMoff/MixUS/Mechanical Assembly/CAD/SolidWorks/Printed parts/STL/Frame_Bottom_Center_Beam_Bracket_wood_Side.STL

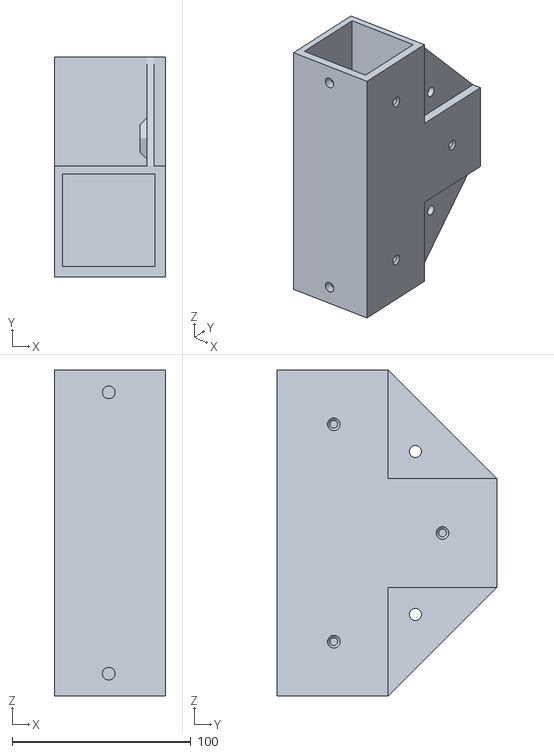
[picture p80: CAD file, 2021-04-10]
Mechanical Assembly/CAD/SolidWorks/Printed parts/STL/Frame_Bottom_Center_Beam_Bracket_wood_Side.STL
62.2 x 123.0 x 182.4
