BenjaminMoff/MixUS/Mechanical Assembly/CAD/SolidWorks/Others/Bottle_Support_TubeA.SLDPRT

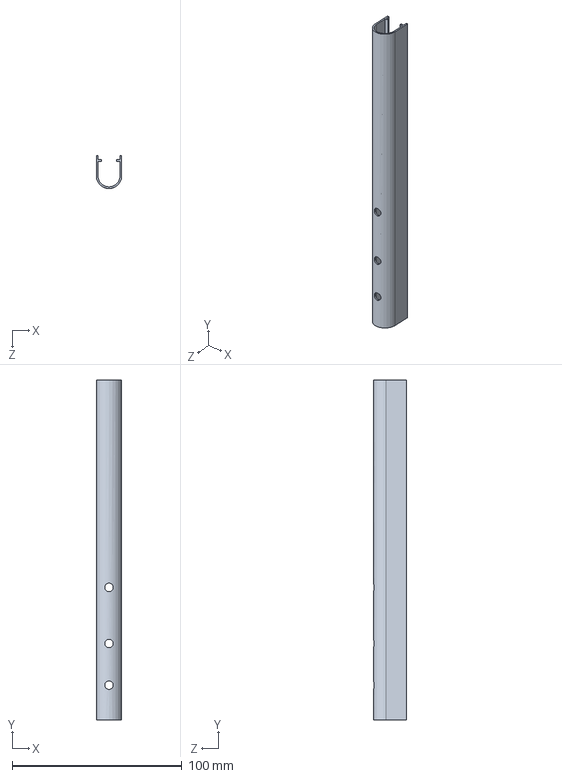
[picture p82: CAD file, 2021-04-10]
Mechanical Assembly/CAD/SolidWorks/Others/Bottle_Support_TubeA.SLDPRT
15.0 x 200.0 x 19.5 mm
