BenjaminMoff/MixUS/Mechanical Assembly/CAD/SolidWorks/Printed parts/SolidWorks/Rambo_Case_Top.SLDPRT

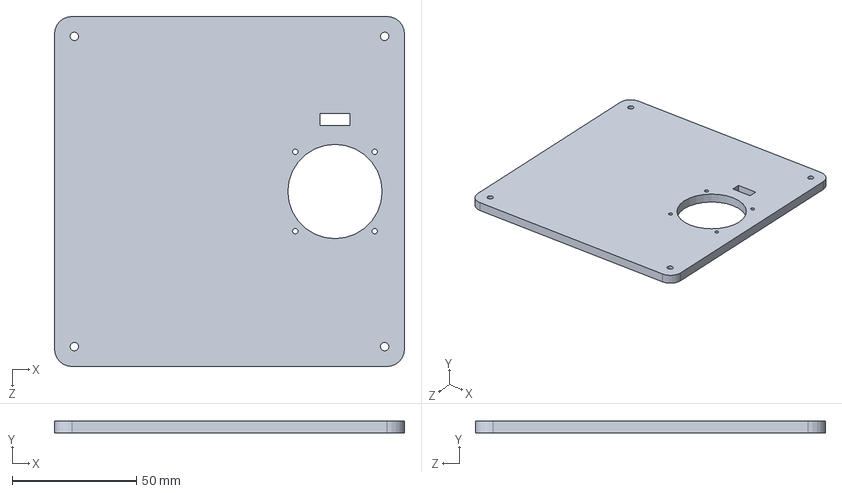
[picture p83: CAD file, 2021-04-10]
Mechanical Assembly/CAD/SolidWorks/Printed parts/SolidWorks/Rambo_Case_Top.SLDPRT
141.0 x 5.00 x 141.0 mm
