BenjaminMoff/MixUS/Mechanical Assembly/CAD/SolidWorks/Printed parts/STL/Frame_Bottom_Center_Beam_Bracket_plexi_side.STL

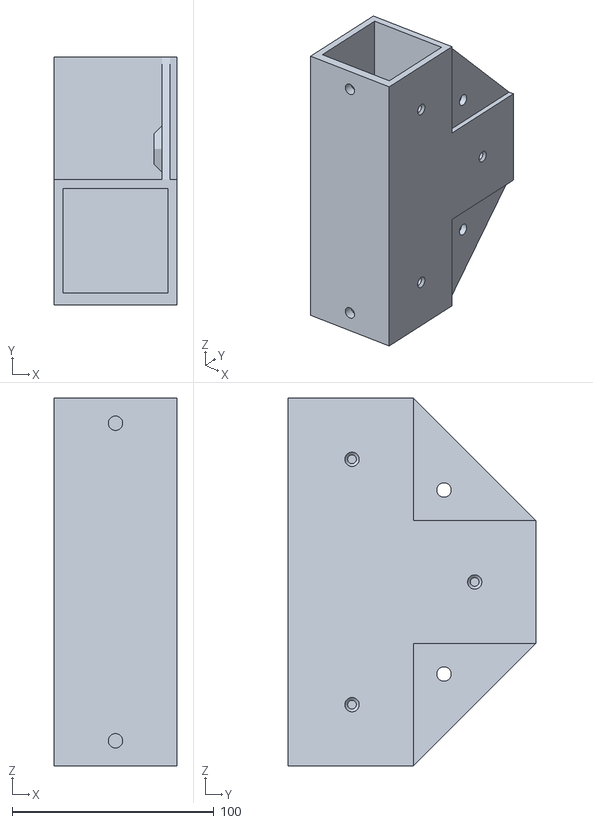
[picture p84: CAD file, 2021-04-10]
Mechanical Assembly/CAD/SolidWorks/Printed parts/STL/Frame_Bottom_Center_Beam_Bracket_plexi_side.STL
60.8 x 123.0 x 182.4
