BenjaminMoff/MixUS/Mechanical Assembly/CAD/SolidWorks/Others/8mm_rod.SLDPRT

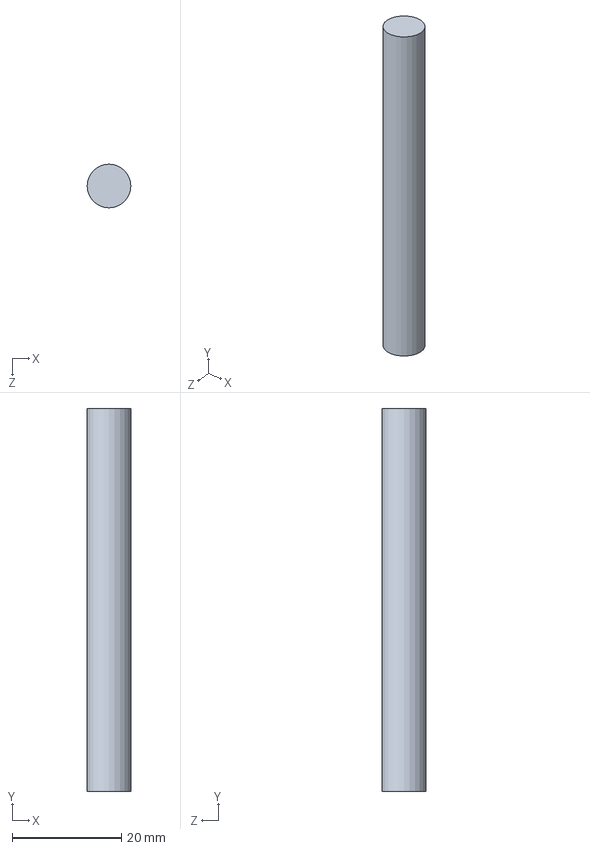
[picture p85: CAD file, 2021-04-10]
Mechanical Assembly/CAD/SolidWorks/Others/8mm_rod.SLDPRT
8.00 x 70.0 x 8.00 mm
