BenjaminMoff/MixUS/Mechanical Assembly/CAD/SolidWorks/Others/Red_cup.SLDPRT

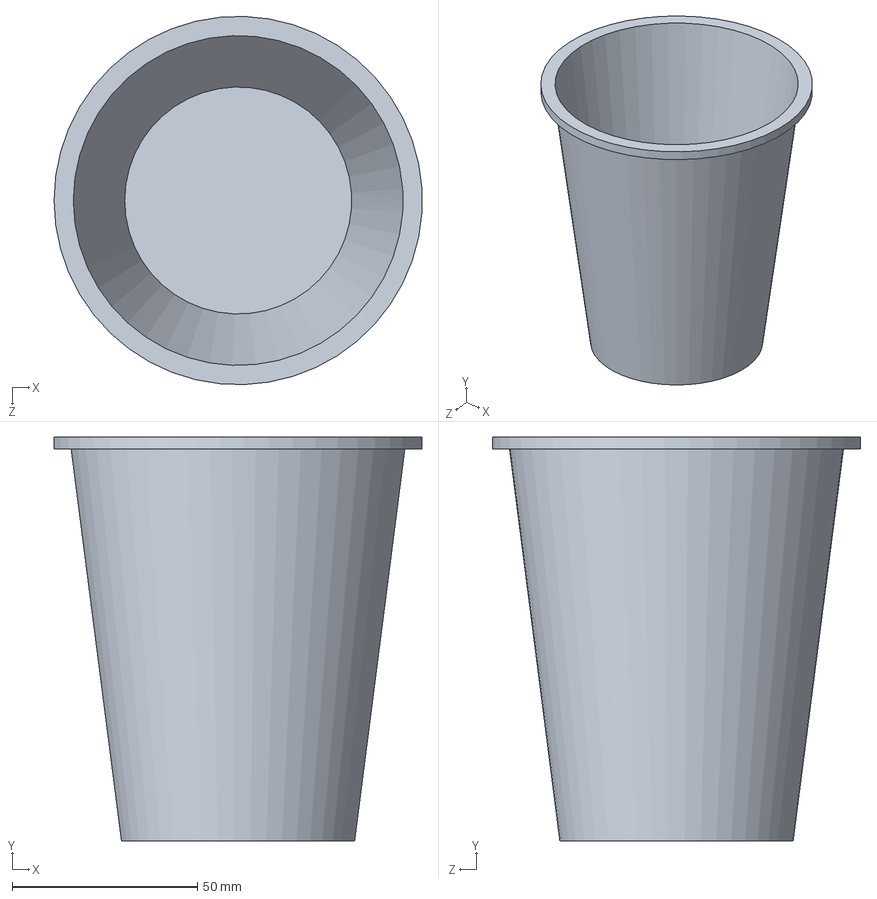
[picture p86: CAD file, 2021-04-10]
Mechanical Assembly/CAD/SolidWorks/Others/Red_cup.SLDPRT
99.3 x 109.0 x 99.3 mm
