BenjaminMoff/MixUS/Mechanical Assembly/CAD/SolidWorks/Others/Bottle.SLDPRT

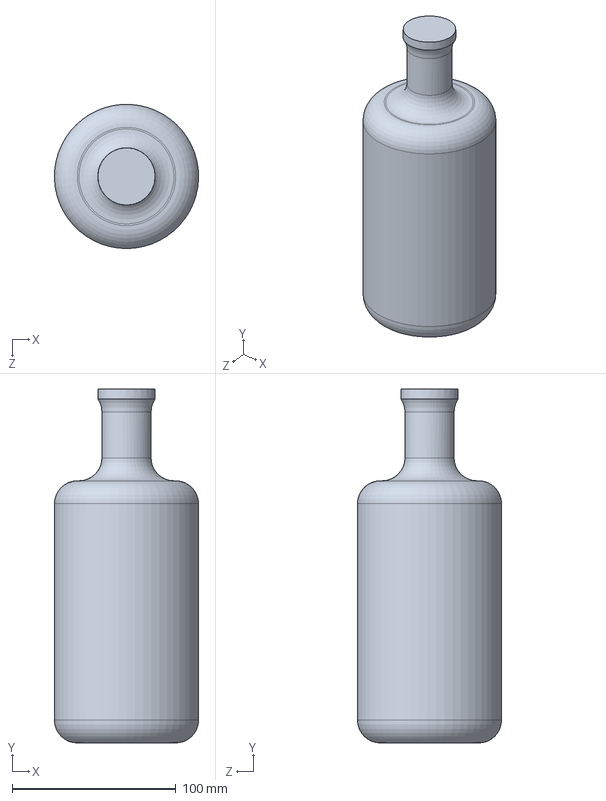
[picture p87: CAD file, 2021-04-10]
Mechanical Assembly/CAD/SolidWorks/Others/Bottle.SLDPRT
88.0 x 216.0 x 87.9 mm
