BenjaminMoff/MixUS/Mechanical Assembly/CAD/SolidWorks/Printed parts/SolidWorks/Y_Switch_Bracket.SLDPRT

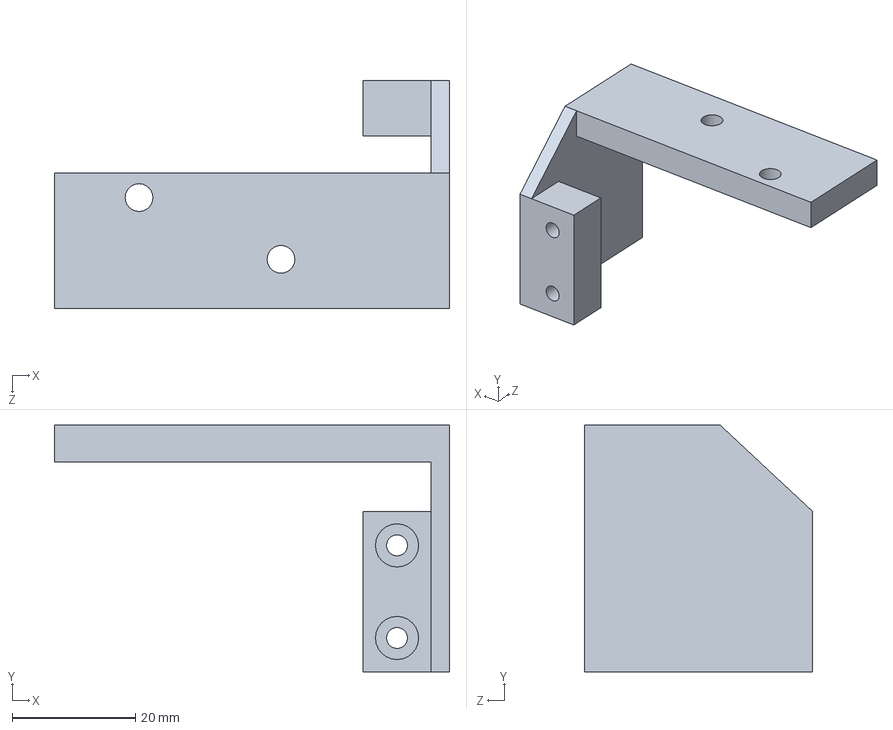
[picture p88: CAD file, 2021-04-10]
Mechanical Assembly/CAD/SolidWorks/Printed parts/SolidWorks/Y_Switch_Bracket.SLDPRT
64.0 x 40.0 x 37.0 mm
