BenjaminMoff/MixUS/Mechanical Assembly/CAD/SolidWorks/Others/Vslot_wheel.SLDPRT

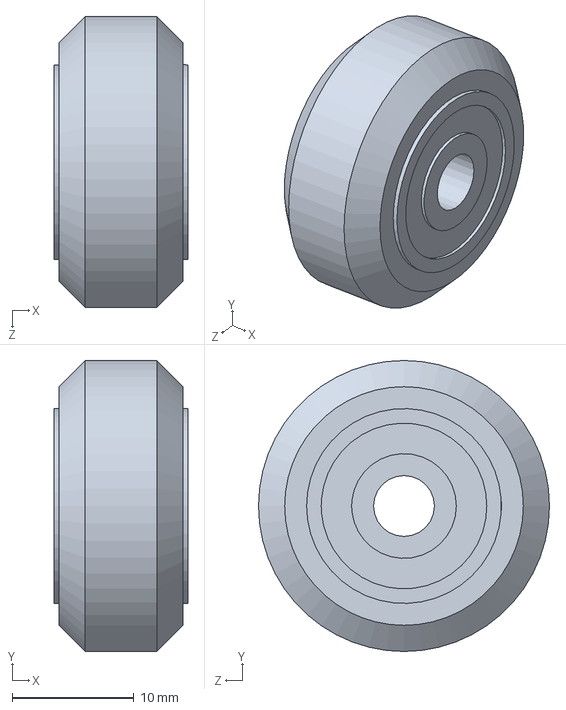
[picture p89: CAD file, 2021-04-10]
Mechanical Assembly/CAD/SolidWorks/Others/Vslot_wheel.SLDPRT
11.0 x 23.9 x 23.9 mm
