BenjaminMoff/MixUS/Mechanical Assembly/CAD/SolidWorks/Printed parts/STL/2040_Printable_extrusion_side.STL

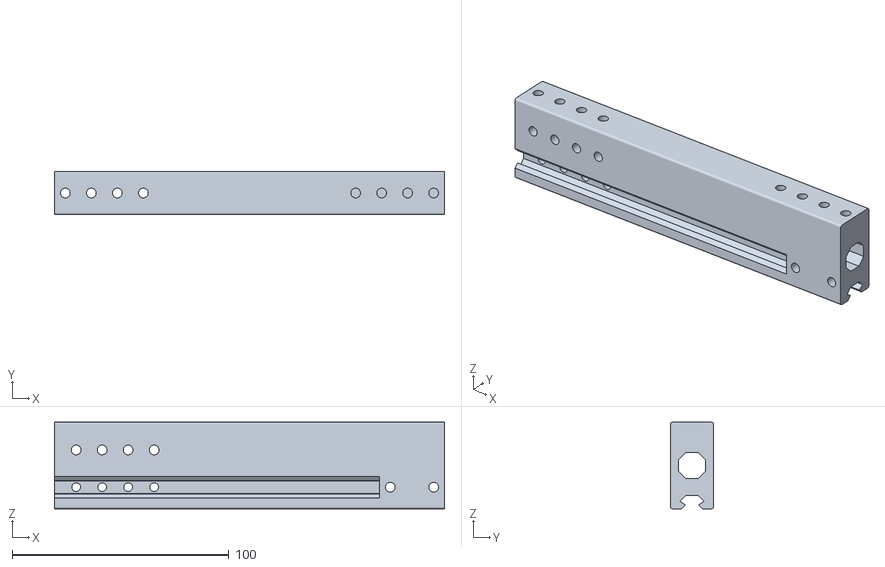
[picture p90: CAD file, 2021-04-10]
Mechanical Assembly/CAD/SolidWorks/Printed parts/STL/2040_Printable_extrusion_side.STL
180.0 x 20.0 x 40.0
