BenjaminMoff/MixUS/Mechanical Assembly/CAD/SolidWorks/Others/8x3mm_Magnet.SLDPRT

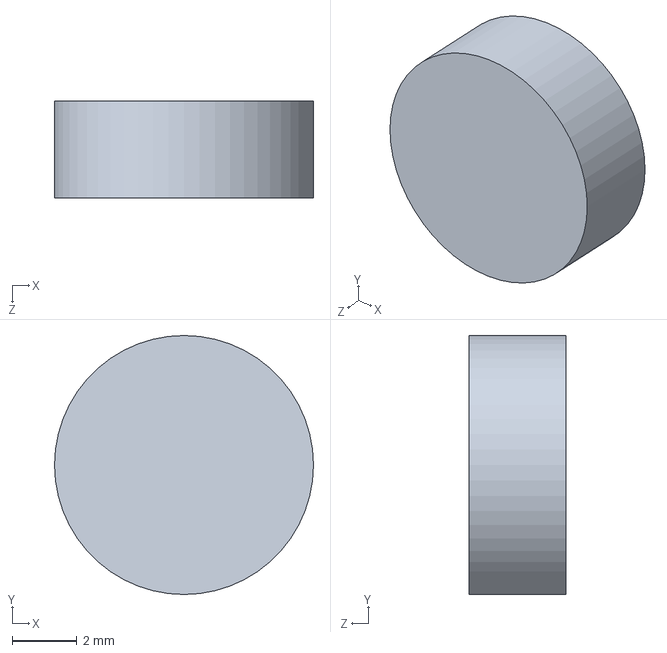
[picture p91: CAD file, 2021-04-10]
Mechanical Assembly/CAD/SolidWorks/Others/8x3mm_Magnet.SLDPRT
8.00 x 8.00 x 3.00 mm
