BenjaminMoff/MixUS/Mechanical Assembly/CAD/SolidWorks/Printed parts/SolidWorks/X_Bracket_Wire.SLDPRT

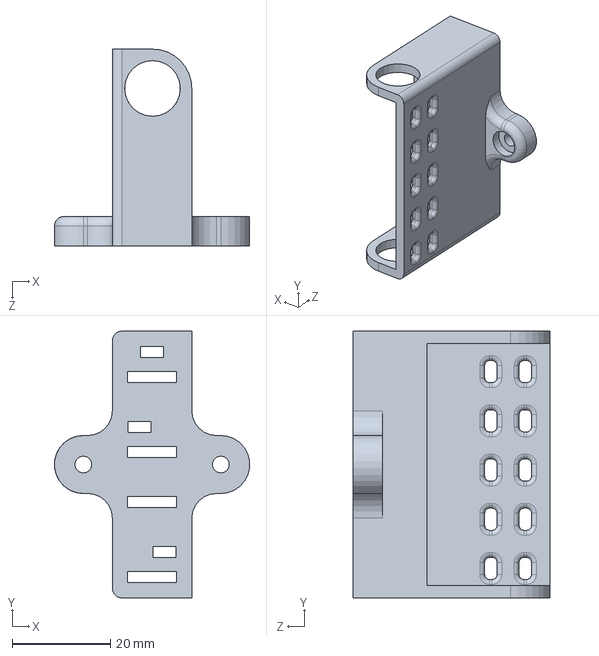
[picture p92: CAD file, 2021-04-10]
Mechanical Assembly/CAD/SolidWorks/Printed parts/SolidWorks/X_Bracket_Wire.SLDPRT
39.7 x 54.3 x 40.0 mm
