BenjaminMoff/MixUS/Mechanical Assembly/CAD/SolidWorks/Printed parts/STL/2040_Connector_Extrusion_M3_Top_slot.STL

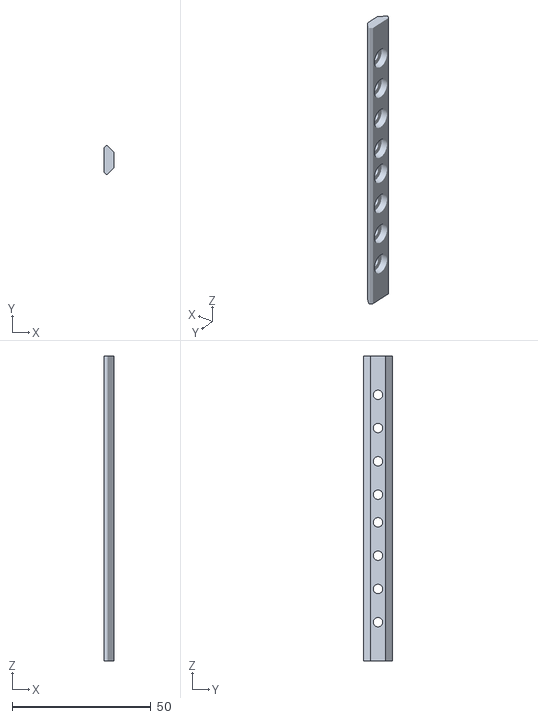
[picture p93: CAD file, 2021-04-10]
Mechanical Assembly/CAD/SolidWorks/Printed parts/STL/2040_Connector_Extrusion_M3_Top_slot.STL
3.62 x 10.4 x 110.0
