BenjaminMoff/MixUS/Mechanical Assembly/CAD/SolidWorks/Others/LM8UU_linear_bearing.SLDPRT

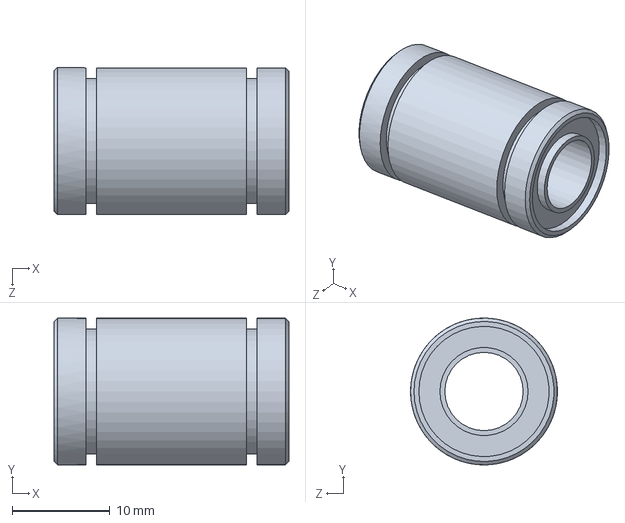
[picture p94: CAD file, 2021-04-10]
Mechanical Assembly/CAD/SolidWorks/Others/LM8UU_linear_bearing.SLDPRT
24.0 x 15.0 x 15.0 mm
