BenjaminMoff/MixUS/Mechanical Assembly/CAD/SolidWorks/Printed parts/SolidWorks/Z_Motor_bracket.SLDPRT

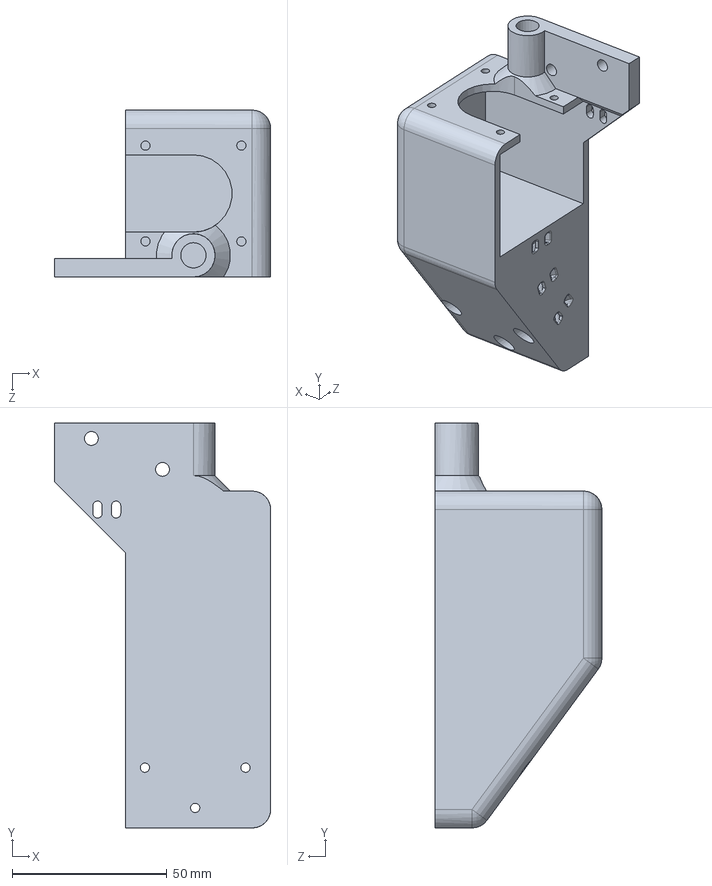
[picture p95: CAD file, 2021-04-10]
Mechanical Assembly/CAD/SolidWorks/Printed parts/SolidWorks/Z_Motor_bracket.SLDPRT
70.0 x 131.0 x 54.0 mm
