BenjaminMoff/MixUS/Mechanical Assembly/CAD/SolidWorks/Printed parts/STL/2040_Connector_Extrusion_M3_Slot.STL

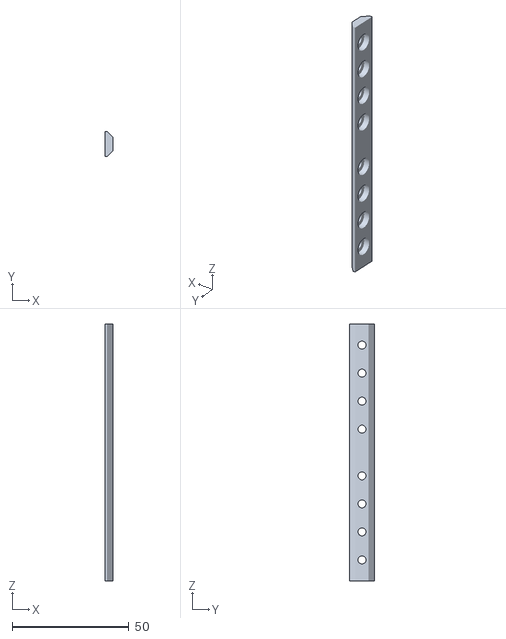
[picture p96: CAD file, 2021-04-10]
Mechanical Assembly/CAD/SolidWorks/Printed parts/STL/2040_Connector_Extrusion_M3_Slot.STL
3.62 x 10.8 x 110.0
