BenjaminMoff/MixUS/Mechanical Assembly/CAD/SolidWorks/Printed parts/SolidWorks/BottleSup_Lock.SLDPRT

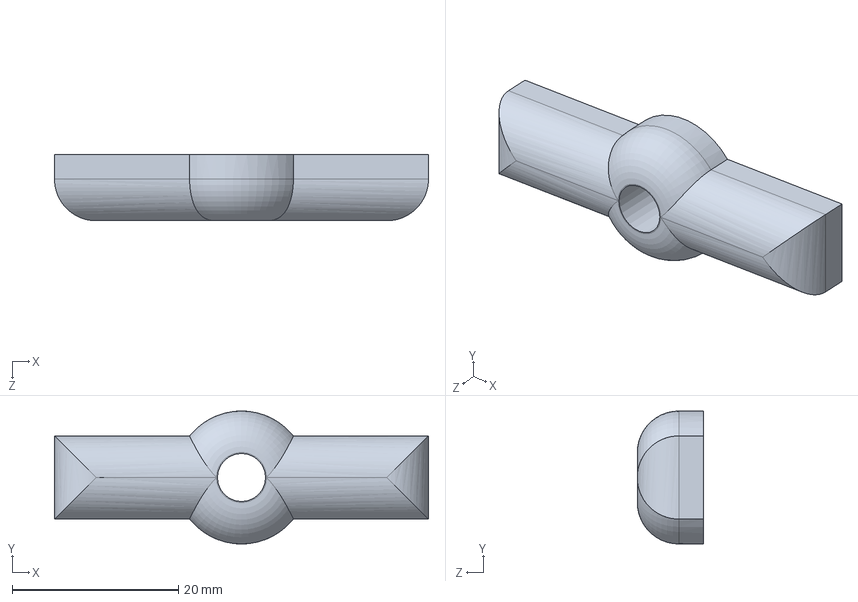
[picture p97: CAD file, 2021-04-10]
Mechanical Assembly/CAD/SolidWorks/Printed parts/SolidWorks/BottleSup_Lock.SLDPRT
45.0 x 16.0 x 8.00 mm
