BenjaminMoff/MixUS/Mechanical Assembly/CAD/SolidWorks/Printed parts/SolidWorks/Y_Glass_Holder_Slider.SLDPRT

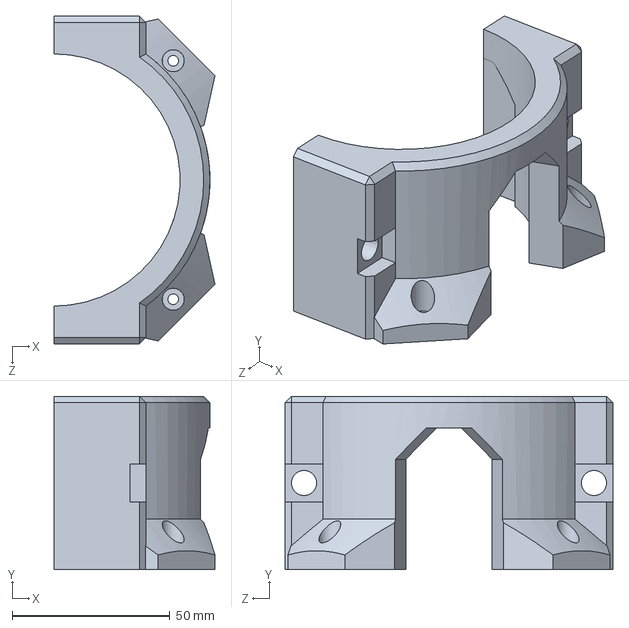
[picture p98: CAD file, 2021-04-10]
Mechanical Assembly/CAD/SolidWorks/Printed parts/SolidWorks/Y_Glass_Holder_Slider.SLDPRT
51.1 x 55.0 x 104.0 mm
