BenjaminMoff/MixUS/Mechanical Assembly/CAD/SolidWorks/Printed parts/SolidWorks/X_Motor_plate.SLDPRT

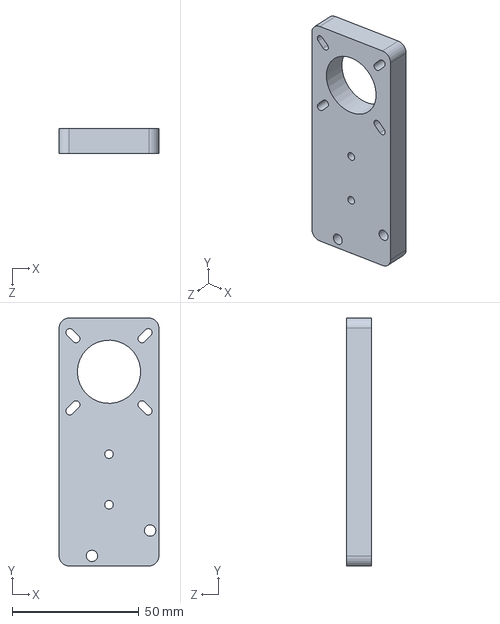
[picture p99: CAD file, 2021-04-10]
Mechanical Assembly/CAD/SolidWorks/Printed parts/SolidWorks/X_Motor_plate.SLDPRT
39.5 x 98.0 x 10.0 mm
