BenjaminMoff/MixUS/Mechanical Assembly/CAD/SolidWorks/Printed parts/SolidWorks/BottleSup_Adapter.SLDPRT

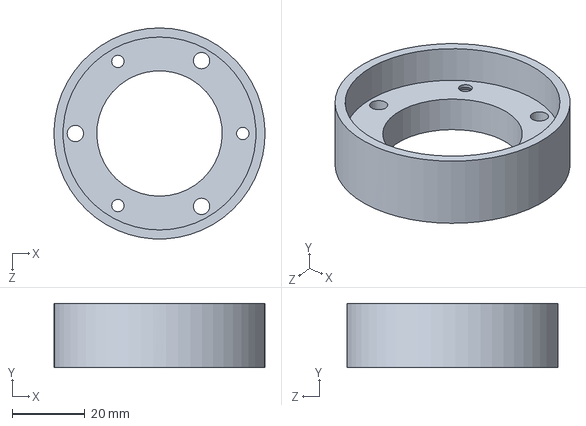
[picture p100: CAD file, 2021-04-10]
Mechanical Assembly/CAD/SolidWorks/Printed parts/SolidWorks/BottleSup_Adapter.SLDPRT
58.0 x 17.7 x 58.0 mm
