BenjaminMoff/MixUS/Mechanical Assembly/CAD/SolidWorks/Printed parts/SolidWorks/BottleSup_Removable_Plate_B.SLDPRT

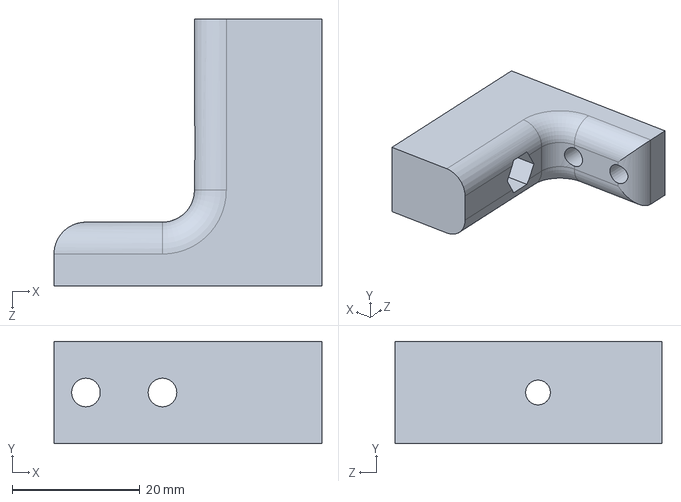
[picture p101: CAD file, 2021-04-10]
Mechanical Assembly/CAD/SolidWorks/Printed parts/SolidWorks/BottleSup_Removable_Plate_B.SLDPRT
42.0 x 16.0 x 41.8 mm
