BenjaminMoff/MixUS/Mechanical Assembly/CAD/SolidWorks/Printed parts/SolidWorks/X_Carriage.SLDPRT

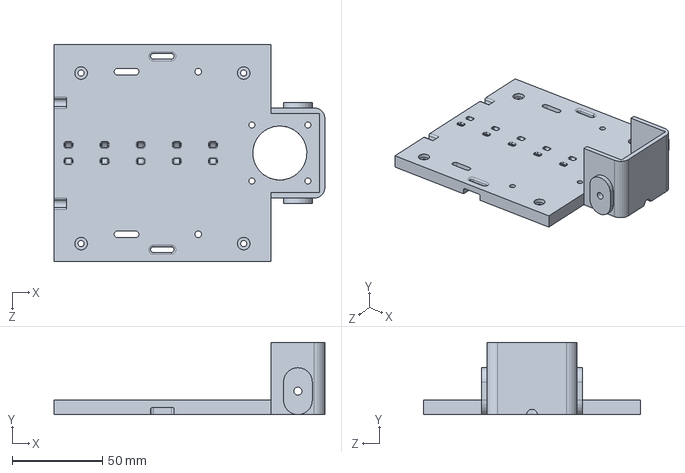
[picture p102: CAD file, 2021-04-10]
Mechanical Assembly/CAD/SolidWorks/Printed parts/SolidWorks/X_Carriage.SLDPRT
150.0 x 40.0 x 120.0 mm
