BenjaminMoff/MixUS/Mechanical Assembly/CAD/SolidWorks/Printed parts/SolidWorks/Y_Pinion.SLDPRT

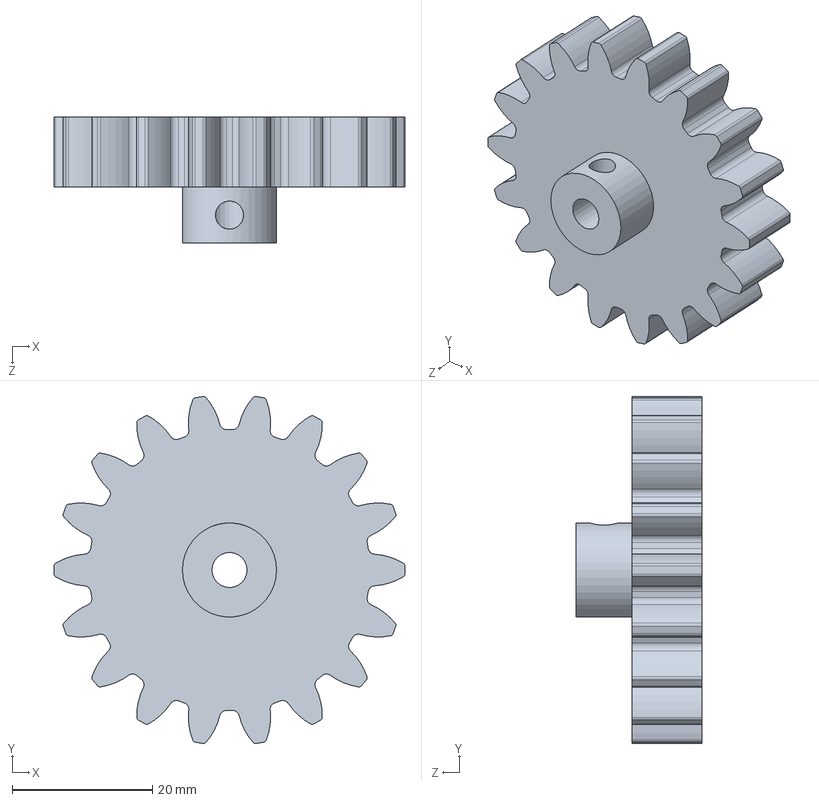
[picture p103: CAD file, 2021-04-10]
Mechanical Assembly/CAD/SolidWorks/Printed parts/SolidWorks/Y_Pinion.SLDPRT
50.0 x 49.4 x 18.0 mm
