BenjaminMoff/MixUS/Mechanical Assembly/CAD/SolidWorks/Printed parts/SolidWorks/X_Idler_plate.SLDPRT

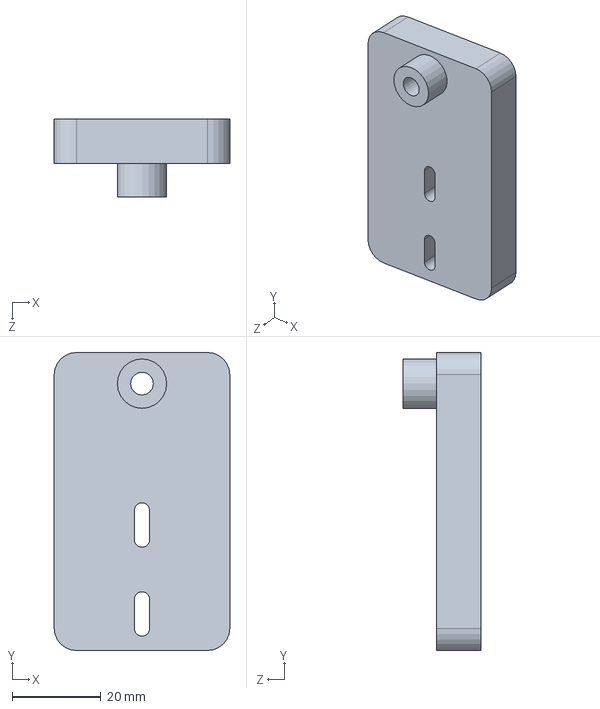
[picture p104: CAD file, 2021-04-10]
Mechanical Assembly/CAD/SolidWorks/Printed parts/SolidWorks/X_Idler_plate.SLDPRT
39.5 x 67.0 x 17.6 mm
