BenjaminMoff/MixUS/Mechanical Assembly/CAD/SolidWorks/Printed parts/SolidWorks/Y_Carriage.SLDPRT

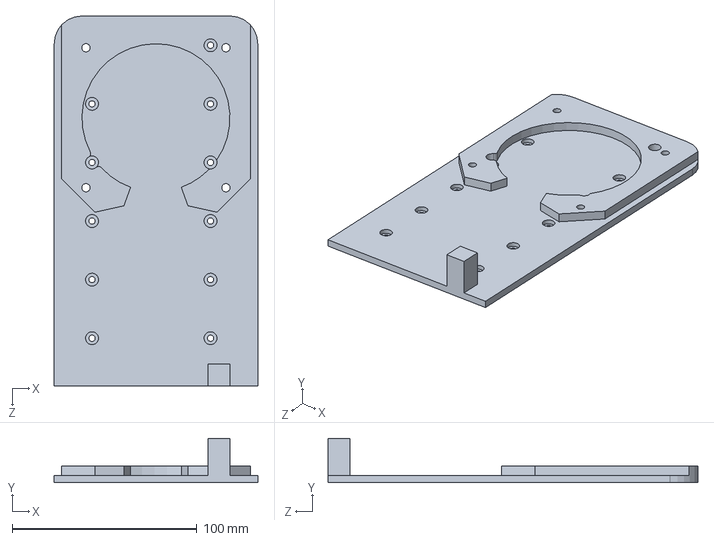
[picture p105: CAD file, 2021-04-10]
Mechanical Assembly/CAD/SolidWorks/Printed parts/SolidWorks/Y_Carriage.SLDPRT
110.1 x 24.0 x 200.0 mm
