BenjaminMoff/MixUS/Mechanical Assembly/CAD/SolidWorks/Printed parts/SolidWorks/Rambo_Case_Bottom.SLDPRT

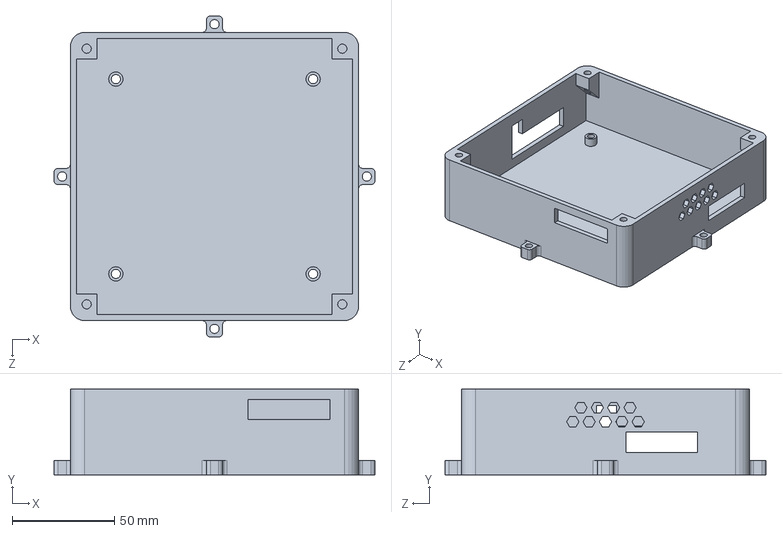
[picture p107: CAD file, 2021-04-10]
Mechanical Assembly/CAD/SolidWorks/Printed parts/SolidWorks/Rambo_Case_Bottom.SLDPRT
157.0 x 42.0 x 157.0 mm
