BenjaminMoff/MixUS/code/diagrams/getInstructions_activity.png

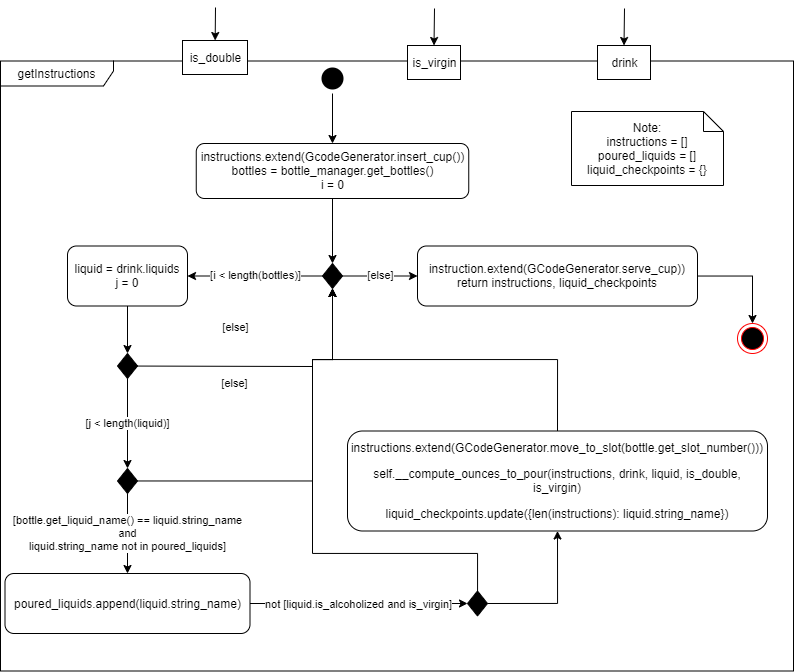
code/diagrams/getInstructions_activity.png
