BenjaminMoff/MixUS/Mechanical Assembly/CAD/SolidWorks/Assembly/Animation/GIF/Assembly.gif

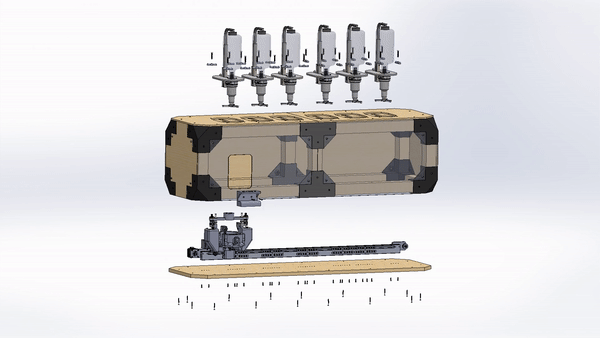
Mechanical Assembly/CAD/SolidWorks/Assembly/Animation/GIF/Assembly.gif
