BenjaminMoff/MixUS/Mechanical Assembly/CAD/SolidWorks/Assembly/Animation/GIF/SubAss_X_Connector_Plate.gif

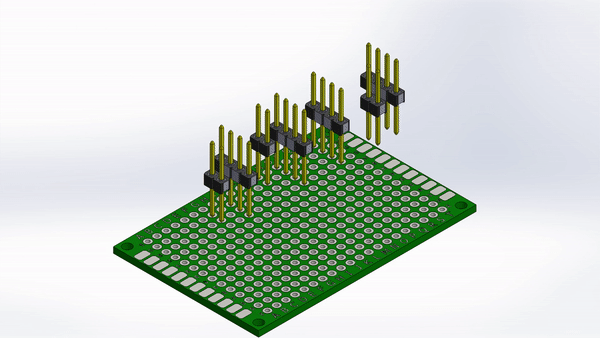
Mechanical Assembly/CAD/SolidWorks/Assembly/Animation/GIF/SubAss_X_Connector_Plate.gif
