BenjaminMoff/MixUS/Mechanical Assembly/CAD/SolidWorks/Assembly/Animation/GIF/SubAss_X_Idler_Plate.gif

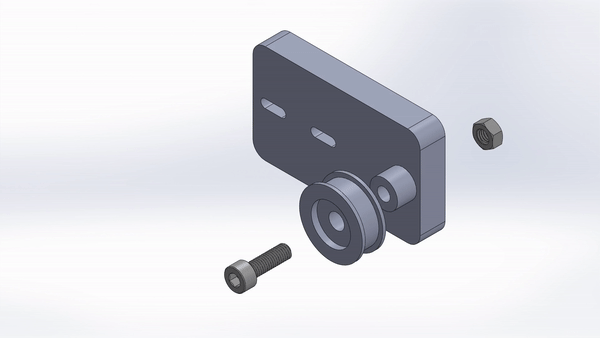
Mechanical Assembly/CAD/SolidWorks/Assembly/Animation/GIF/SubAss_X_Idler_Plate.gif
