BenjaminMoff/MixUS/Mechanical Assembly/CAD/SolidWorks/Assembly/Animation/GIF/SubAss_X_Motor_Plate.gif

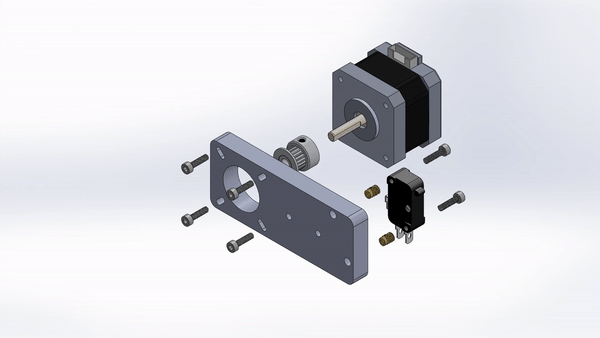
Mechanical Assembly/CAD/SolidWorks/Assembly/Animation/GIF/SubAss_X_Motor_Plate.gif
