BenjaminMoff/MixUS/Mechanical Assembly/CAD/SolidWorks/Assembly/Animation/GIF/SubAss_Y_Carriage.gif

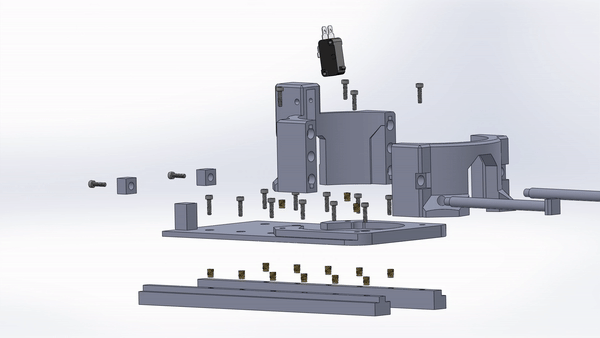
Mechanical Assembly/CAD/SolidWorks/Assembly/Animation/GIF/SubAss_Y_Carriage.gif
