BenjaminMoff/MixUS/Mechanical Assembly/CAD/SolidWorks/Assembly/Animation/GIF/SubAss_Y_Wheel_Bracket.gif

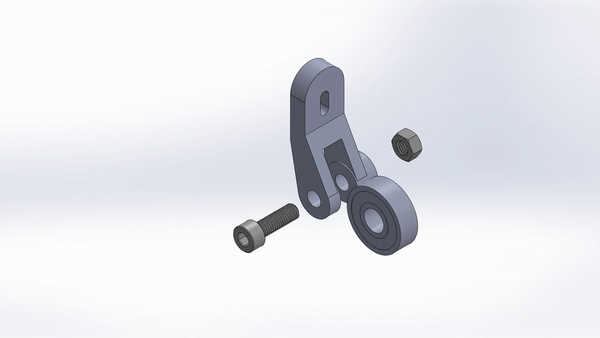
Mechanical Assembly/CAD/SolidWorks/Assembly/Animation/GIF/SubAss_Y_Wheel_Bracket.gif
