BenjaminMoff/MixUS/Mechanical Assembly/CAD/SolidWorks/Assembly/Animation/GIF/SubAss_Z_Motor_Bracket.gif

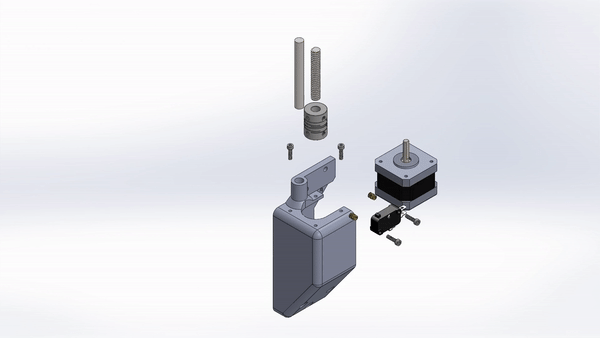
Mechanical Assembly/CAD/SolidWorks/Assembly/Animation/GIF/SubAss_Z_Motor_Bracket.gif
