BenjaminMoff/MixUS/Mechanical Assembly/CAD/SolidWorks/Assembly/Exploded_view/PNG/SubAss_2040_Extrusion.png

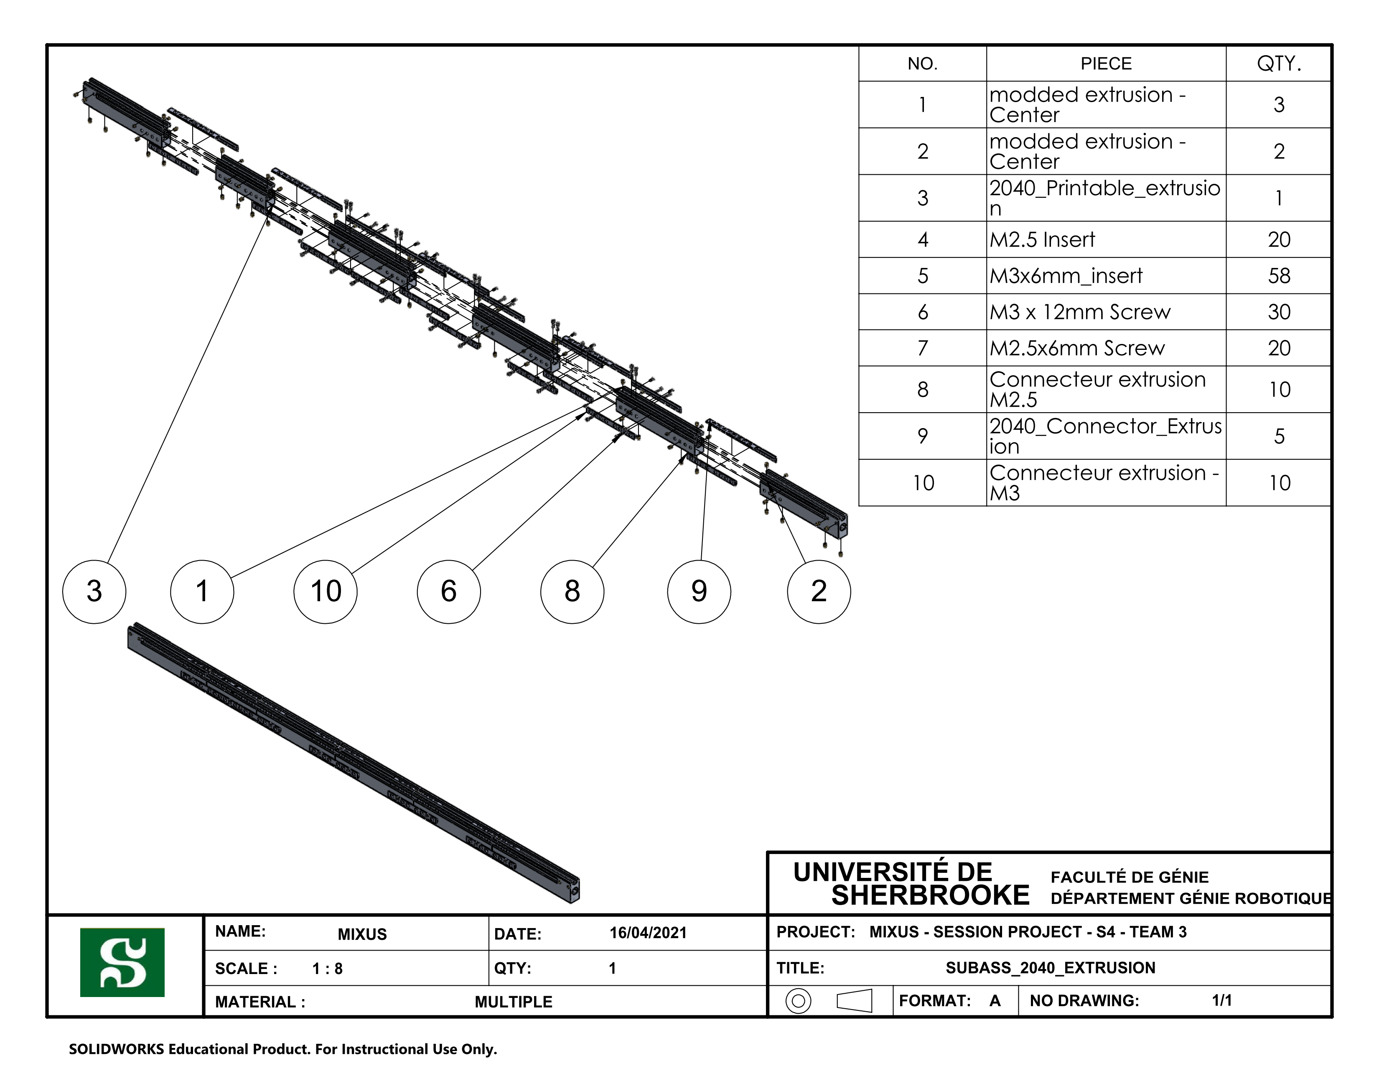
Mechanical Assembly/CAD/SolidWorks/Assembly/Exploded_view/PNG/SubAss_2040_Extrusion.png
