BenjaminMoff/MixUS/Mechanical Assembly/CAD/SolidWorks/Assembly/Exploded_view/PNG/SubAss_X_Carriage_01.png

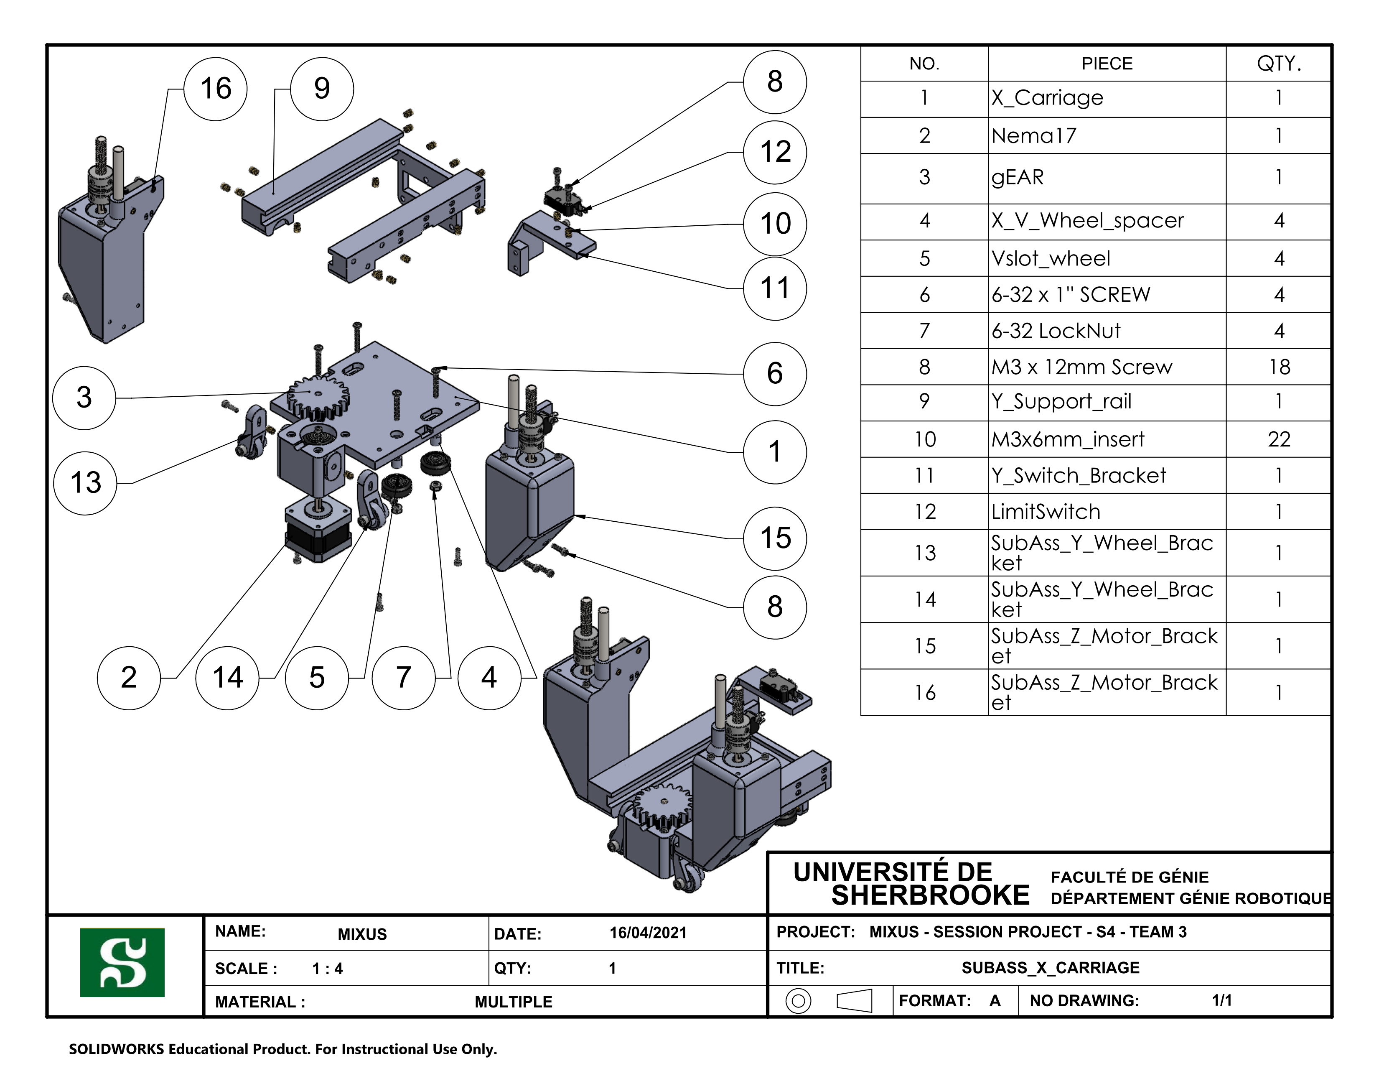
Mechanical Assembly/CAD/SolidWorks/Assembly/Exploded_view/PNG/SubAss_X_Carriage_01.png
