BenjaminMoff/MixUS/Mechanical Assembly/CAD/SolidWorks/Assembly/Exploded_view/PNG/SubAss_X_Motor_Plate_01.png

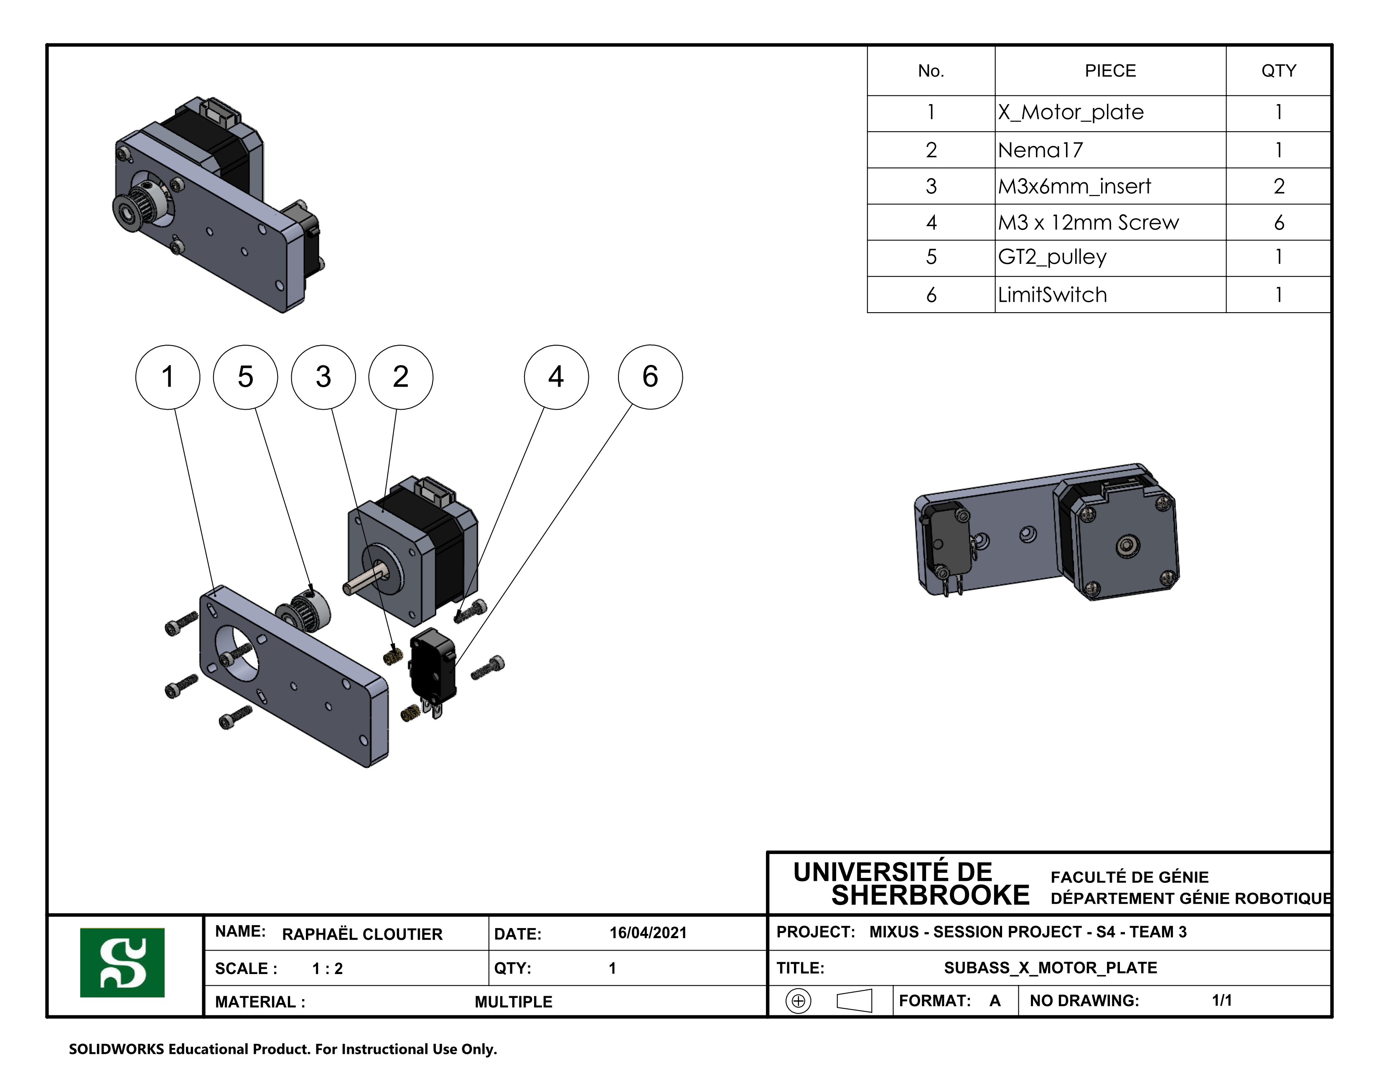
Mechanical Assembly/CAD/SolidWorks/Assembly/Exploded_view/PNG/SubAss_X_Motor_Plate_01.png
