BenjaminMoff/MixUS/Media Wiki/Flashing the Marlin Firmware/UploadingMarlinStep1.gif

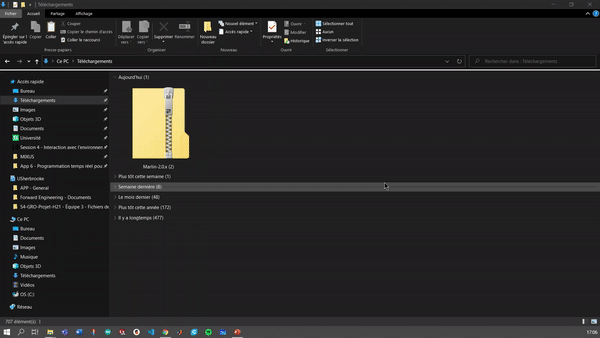
Media Wiki/Flashing the Marlin Firmware/UploadingMarlinStep1.gif
