BenjaminMoff/MixUS/Media Wiki/Frame Assembly/Assembly picture/Back_Plate Scrap_Piece.png

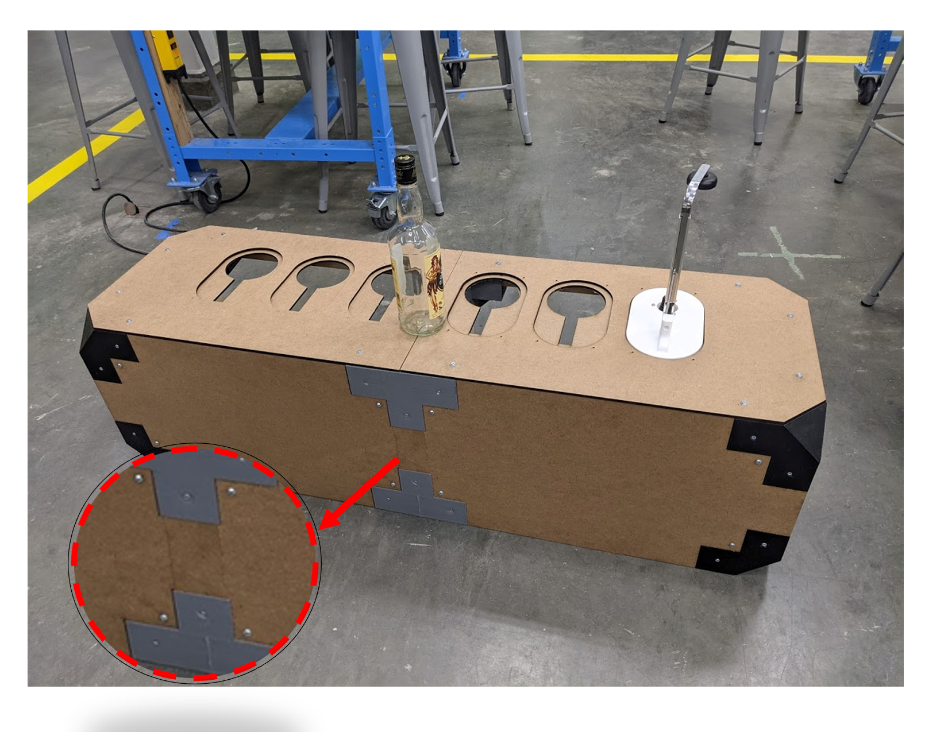
Media Wiki/Frame Assembly/Assembly picture/Back_Plate Scrap_Piece.png
