BenjaminMoff/MixUS/Media Wiki/Frame Assembly/Assembly picture/clearance_dispenser_Zpusher_with_rubberband.png

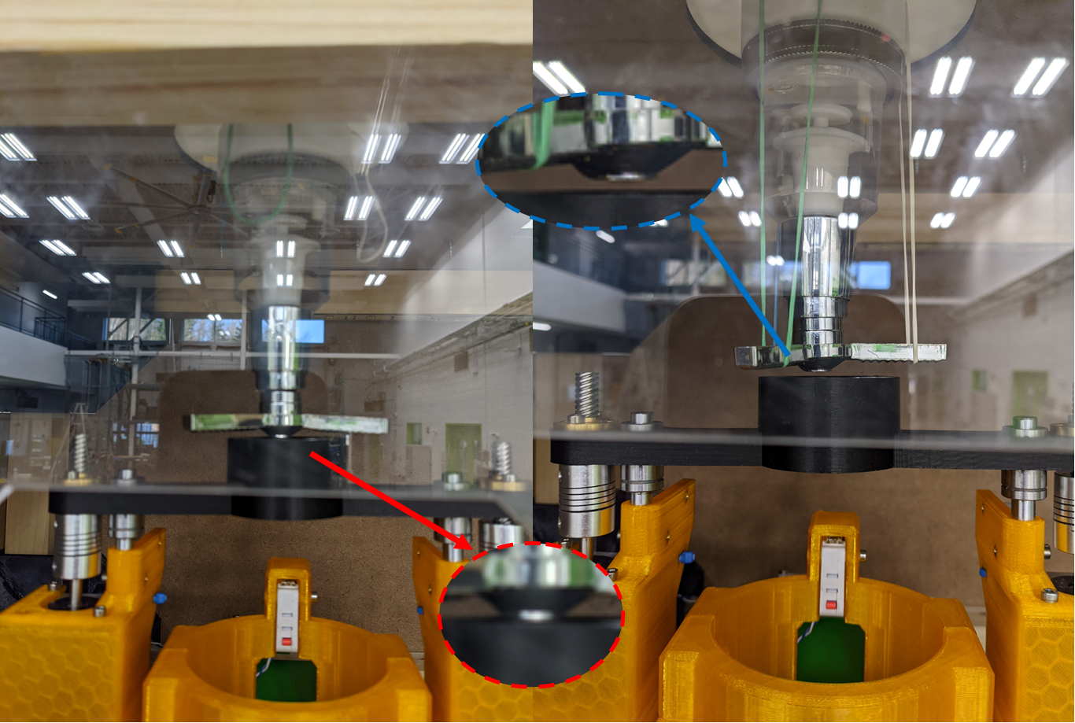
Media Wiki/Frame Assembly/Assembly picture/clearance_dispenser_Zpusher_with_rubberband.png
