BenjaminMoff/MixUS/Media Wiki/Frame Assembly/Assembly picture/Dispenser_2.png

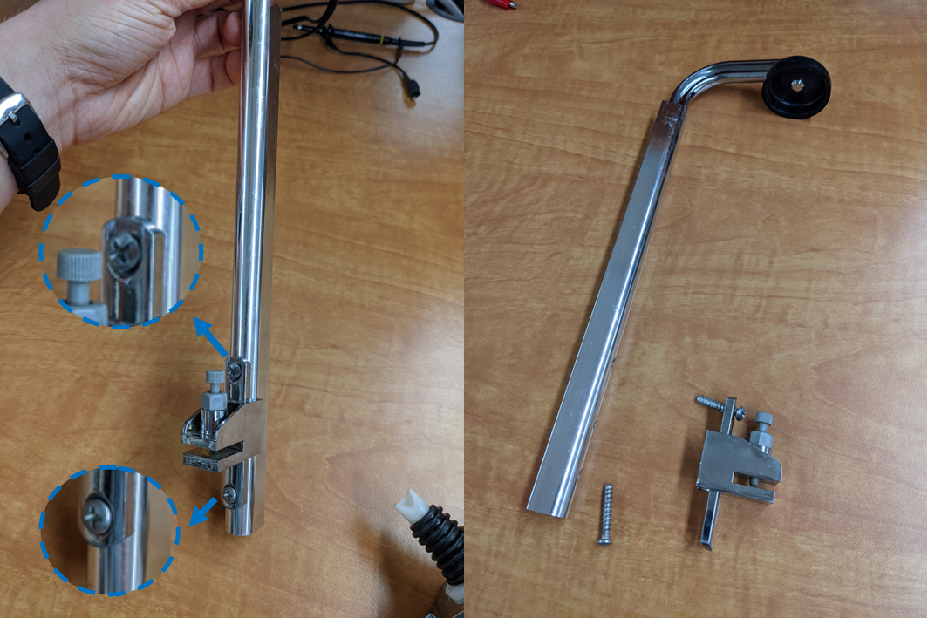
Media Wiki/Frame Assembly/Assembly picture/Dispenser_2.png
