BenjaminMoff/MixUS/Media Wiki/Frame Assembly/Assembly picture/Dispenser_3.png

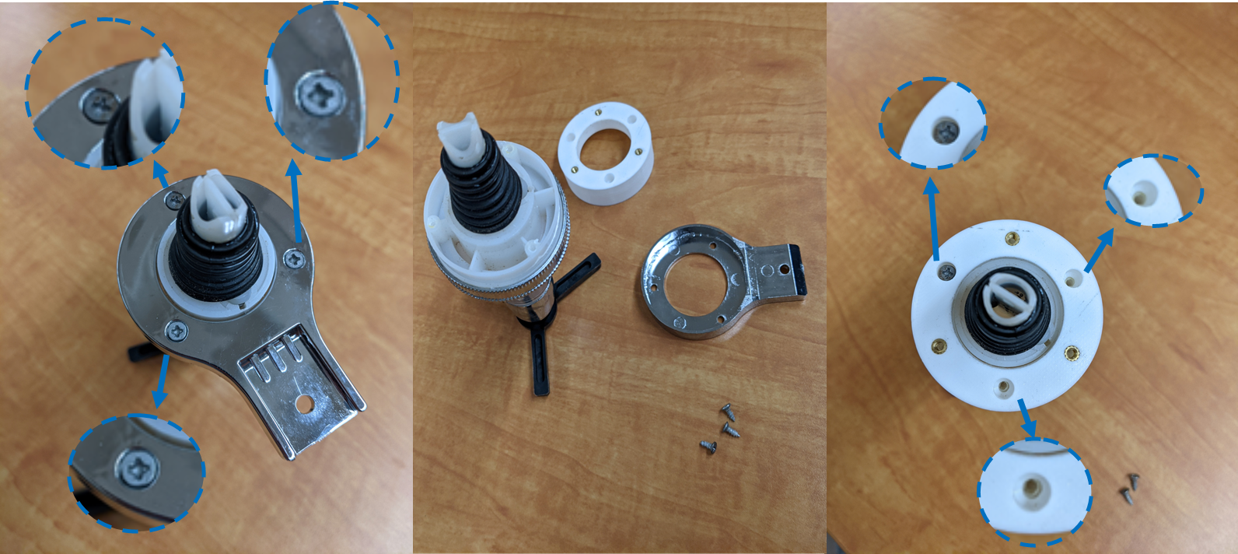
Media Wiki/Frame Assembly/Assembly picture/Dispenser_3.png
