BenjaminMoff/MixUS/Media Wiki/Frame Assembly/Assembly picture/Installing_rubberBand.png

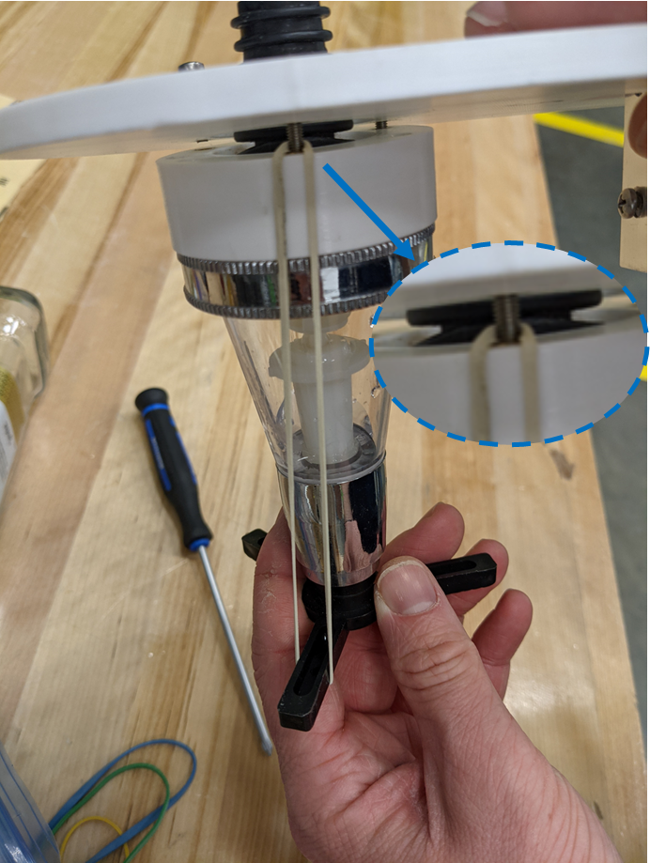
Media Wiki/Frame Assembly/Assembly picture/Installing_rubberBand.png
