BenjaminMoff/MixUS/Media Wiki/Frame Assembly/Assembly picture/WoodMistake_solution.png

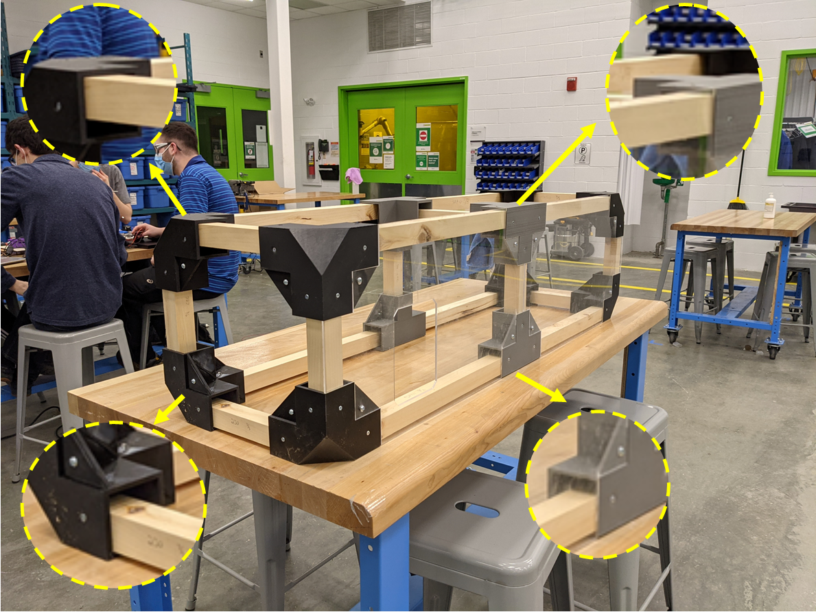
Media Wiki/Frame Assembly/Assembly picture/WoodMistake_solution.png
