BenjaminMoff/MixUS/Media Wiki/Frame Assembly/Exploded-view/SubAss_Frame_ALL.PNG

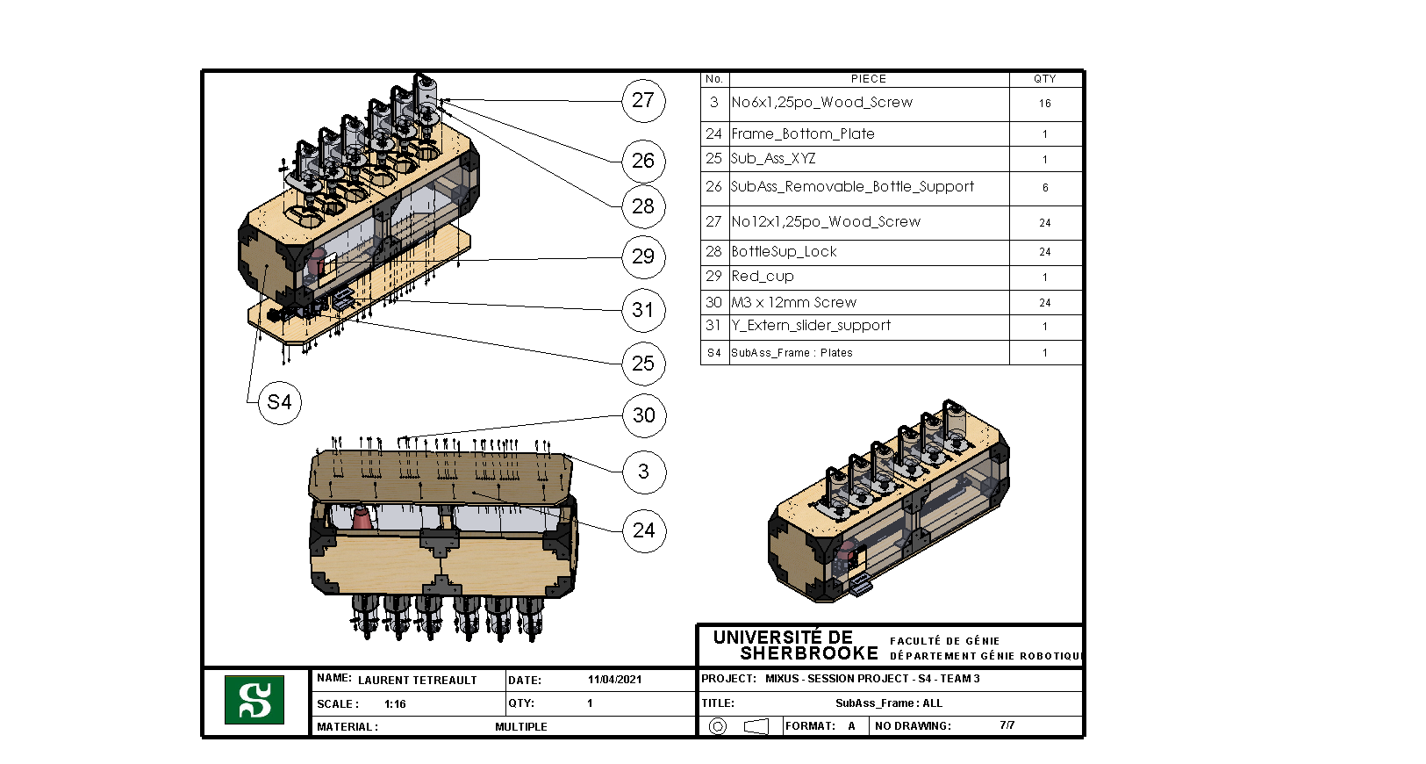
Media Wiki/Frame Assembly/Exploded-view/SubAss_Frame_ALL.PNG
