BenjaminMoff/MixUS/Media Wiki/Frame Assembly/Exploded-view/SubAss_Frame_Center.PNG

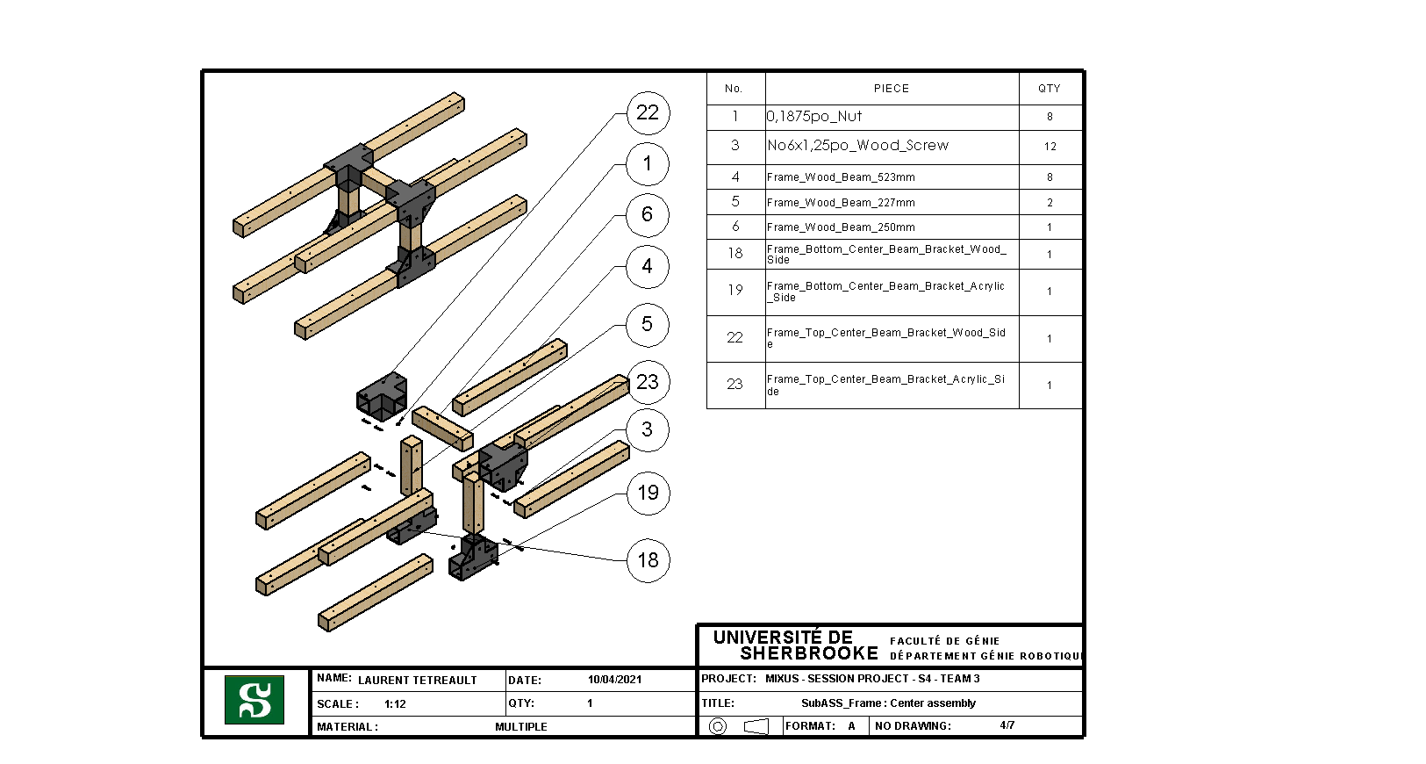
Media Wiki/Frame Assembly/Exploded-view/SubAss_Frame_Center.PNG
