BenjaminMoff/MixUS/Media Wiki/Frame Assembly/Exploded-view/SubAss_Frame_Plates.PNG

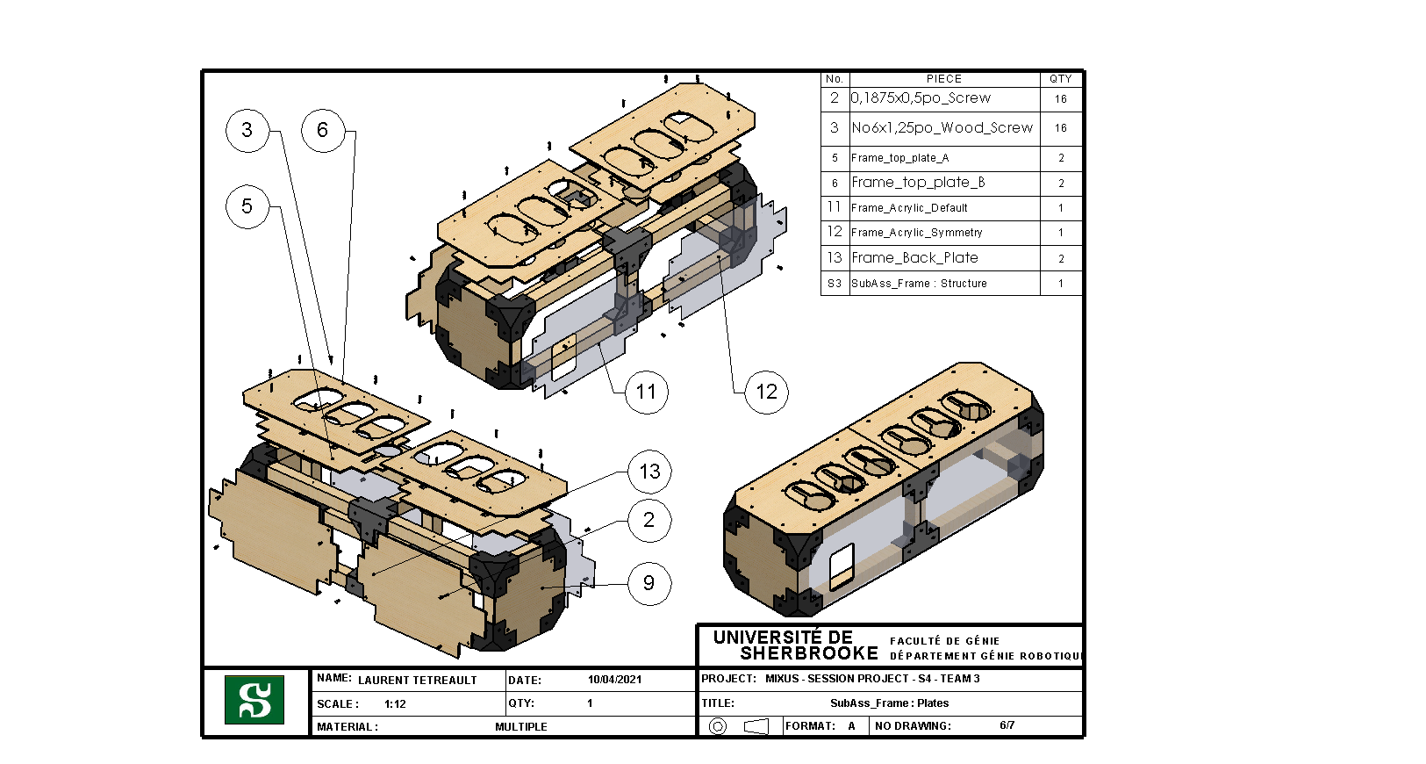
Media Wiki/Frame Assembly/Exploded-view/SubAss_Frame_Plates.PNG
