BenjaminMoff/MixUS/Media Wiki/Frame Assembly/Exploded-view/SubAss_Frame_Side.PNG

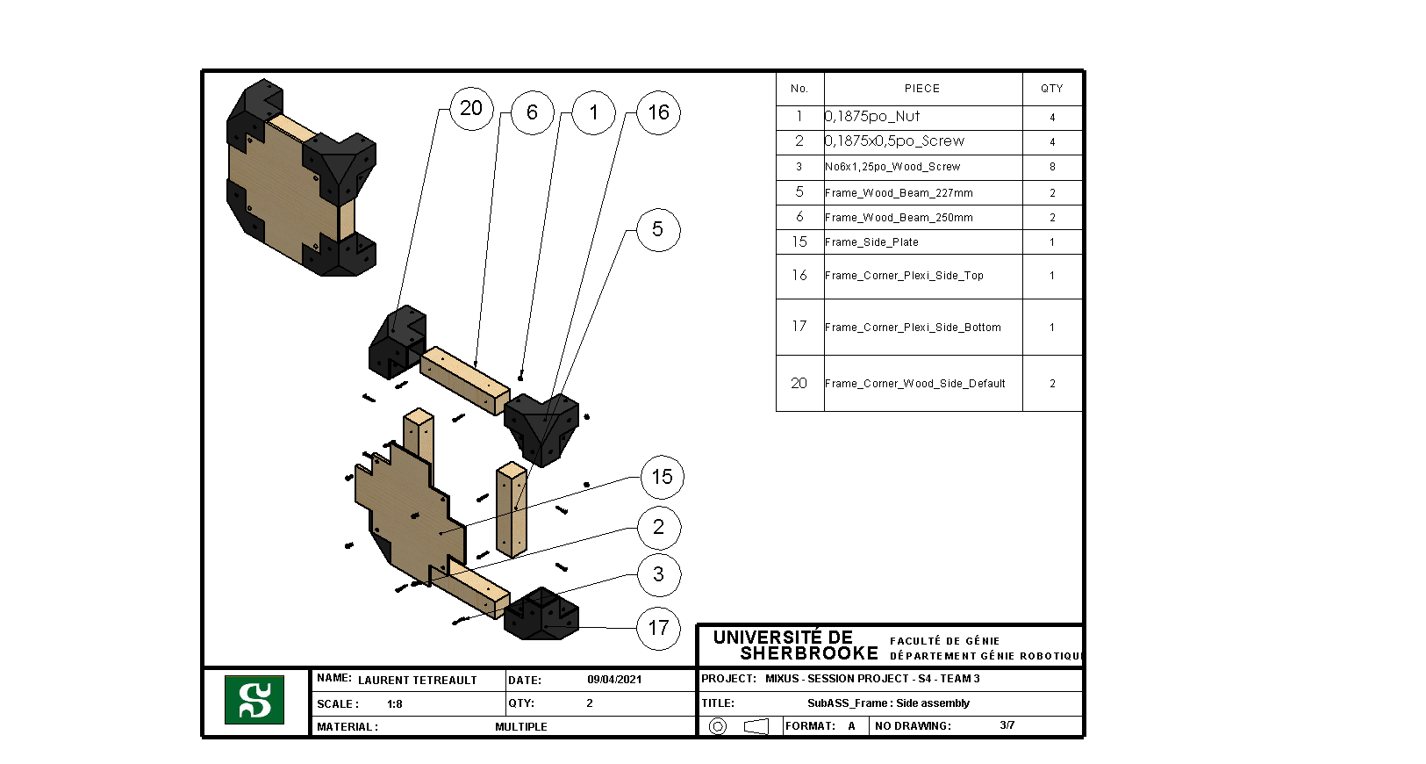
Media Wiki/Frame Assembly/Exploded-view/SubAss_Frame_Side.PNG
