BenjaminMoff/MixUS/Media Wiki/Frame Assembly/Exploded-view/SubAss_Frame_Structure.PNG

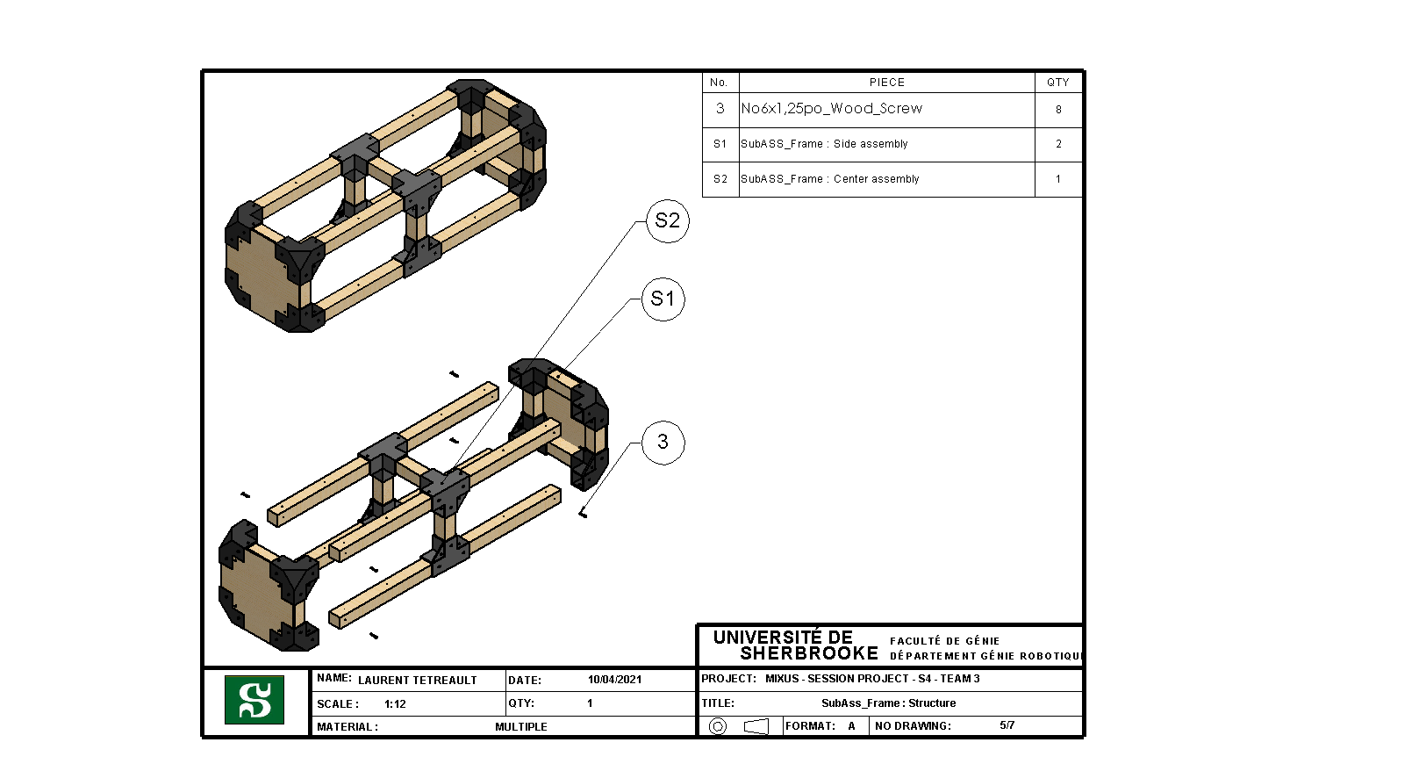
Media Wiki/Frame Assembly/Exploded-view/SubAss_Frame_Structure.PNG
