BenjaminMoff/MixUS/Media Wiki/Frame Assembly/Exploded-view/SubAss_Rambo_Case.PNG

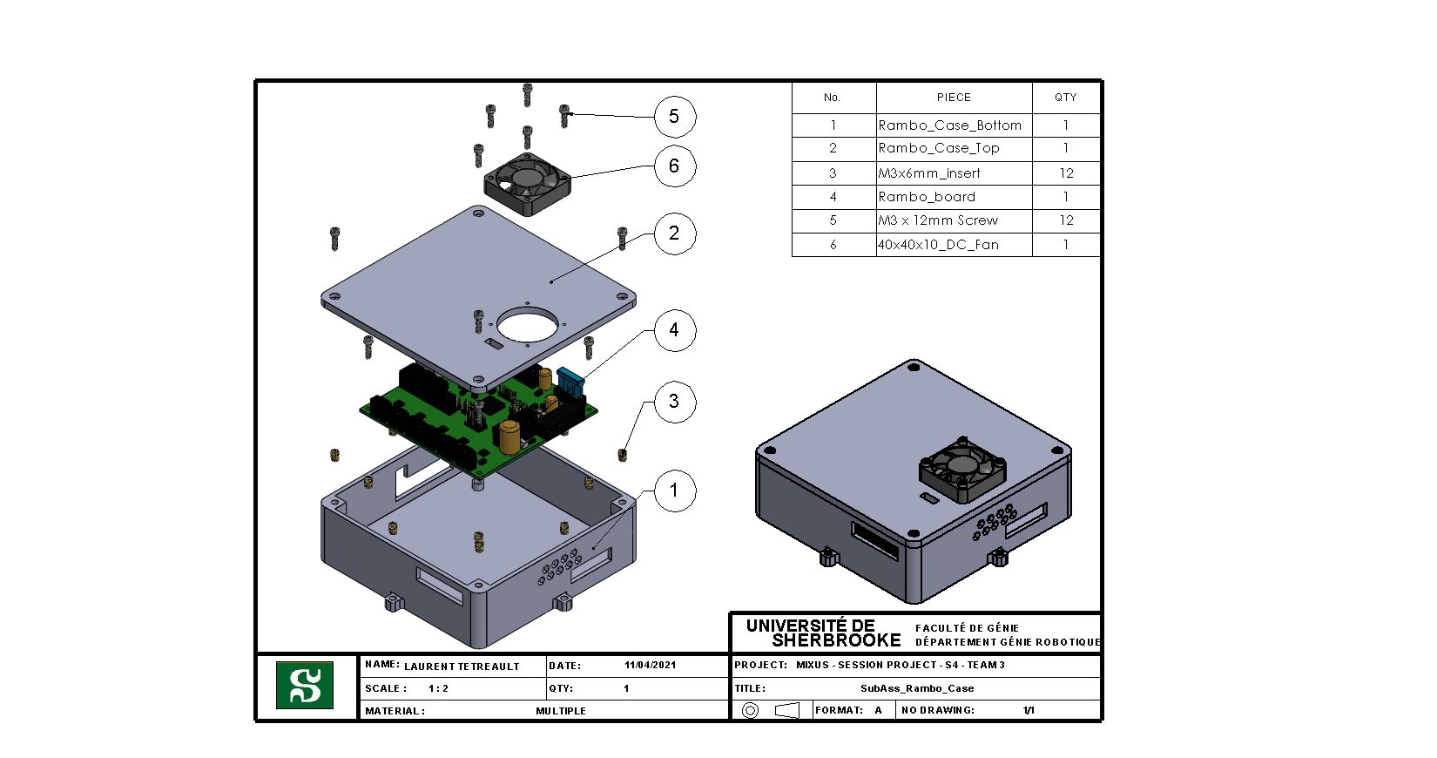
Media Wiki/Frame Assembly/Exploded-view/SubAss_Rambo_Case.PNG
