BenjaminMoff/MixUS/Media Wiki/Frame Assembly/Exploded-view/SubAss_Removable_Bottle_Support_01.png

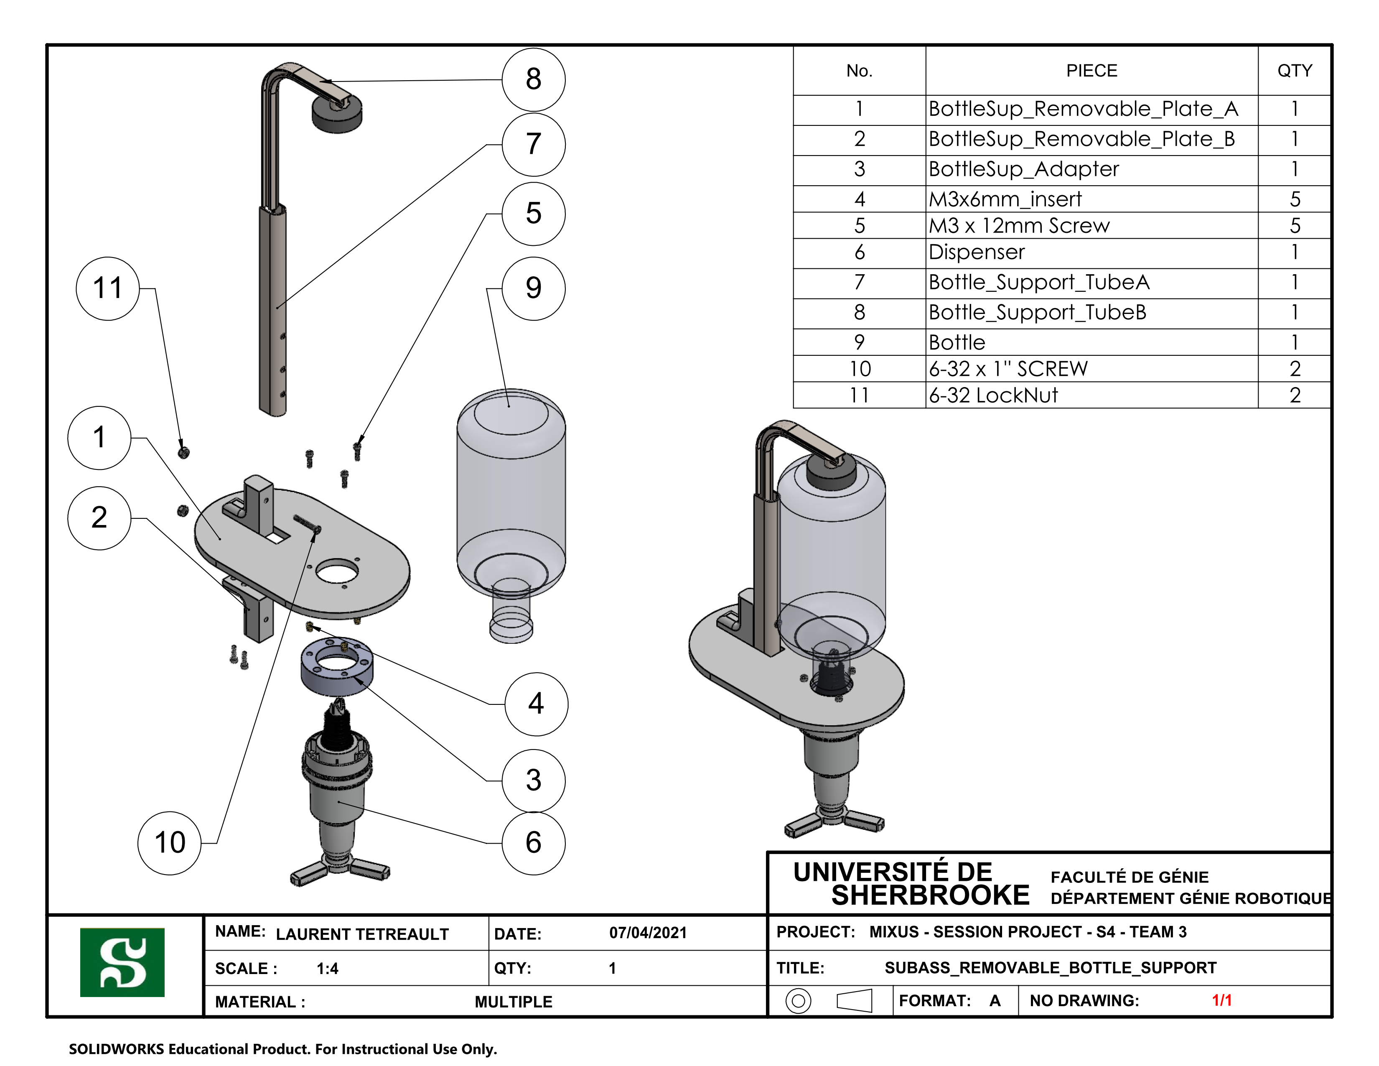
Media Wiki/Frame Assembly/Exploded-view/SubAss_Removable_Bottle_Support_01.png
