BenjaminMoff/MixUS/Media Wiki/Frame Assembly/Exploded-view/Total_Assembly.PNG

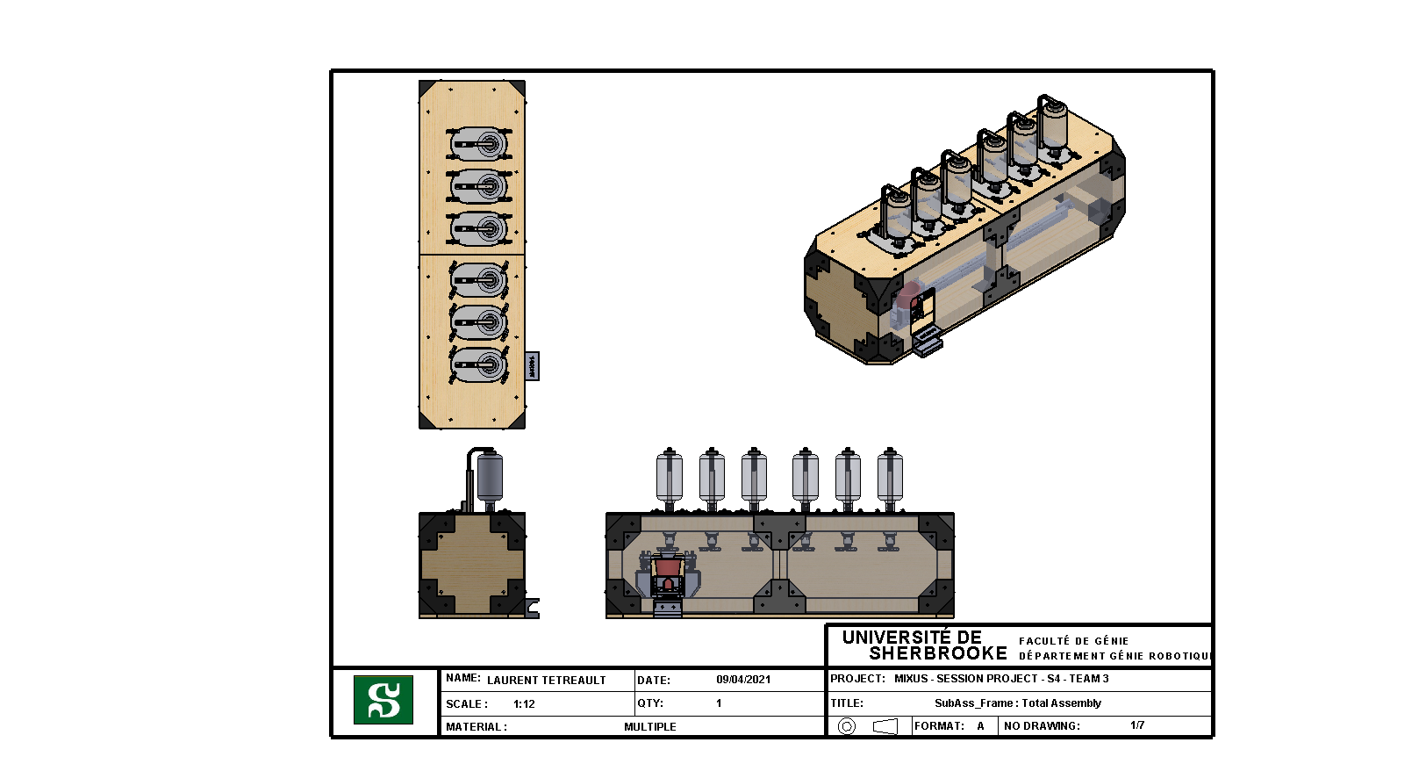
Media Wiki/Frame Assembly/Exploded-view/Total_Assembly.PNG
