BenjaminMoff/MixUS/Media Wiki/Putting it all together/Wiring_Inside_1.png

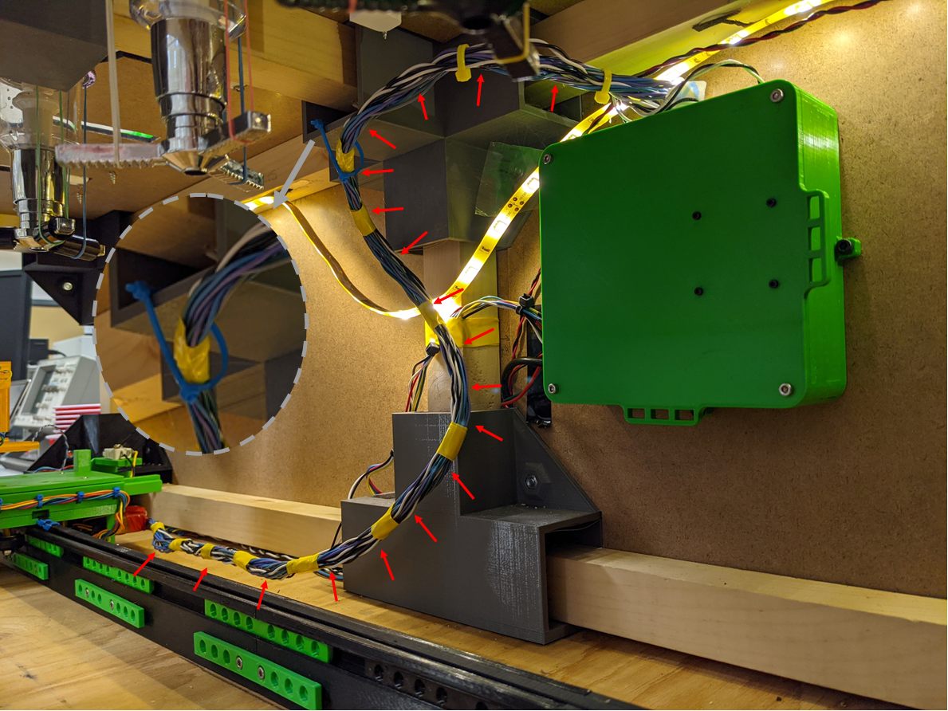
Media Wiki/Putting it all together/Wiring_Inside_1.png
