BenjaminMoff/MixUS/Media Wiki/Putting it all together/Wiring_Inside_2.png

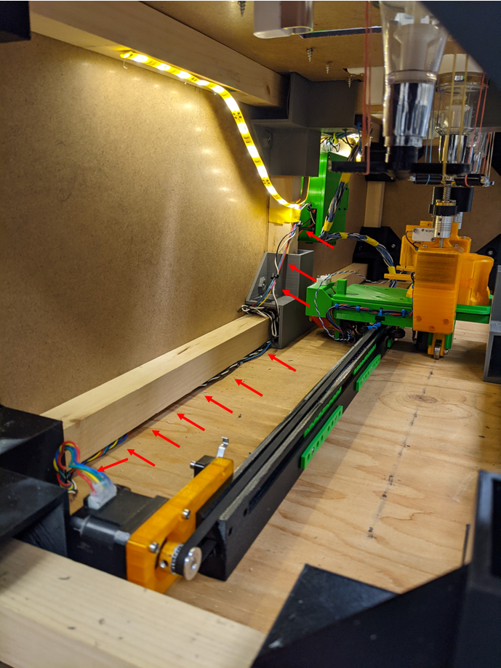
Media Wiki/Putting it all together/Wiring_Inside_2.png
