BenjaminMoff/MixUS/Media Wiki/Putting it all together/Wiring_Inside_3.png

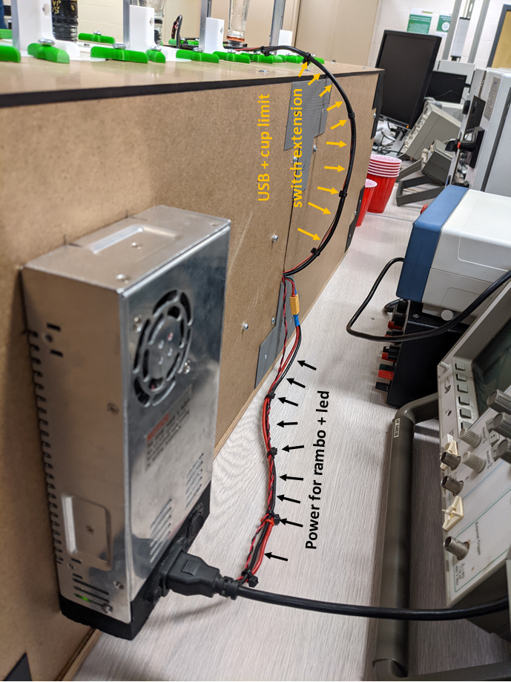
Media Wiki/Putting it all together/Wiring_Inside_3.png
