BenjaminMoff/MixUS/Media Wiki/Putting it all together/X_Wiring_Motor_Check.png

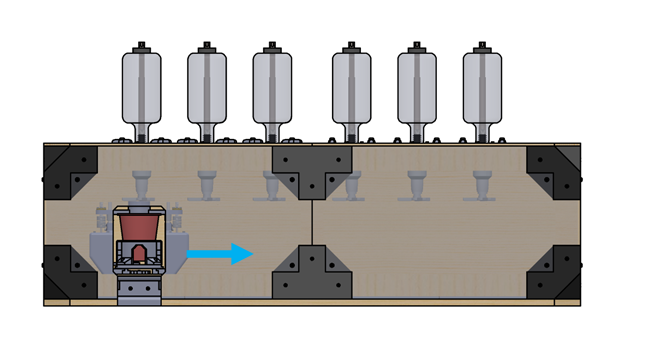
Media Wiki/Putting it all together/X_Wiring_Motor_Check.png
