BenjaminMoff/MixUS/Media Wiki/Putting it all together/Z_Wiring_Motor_Check.png

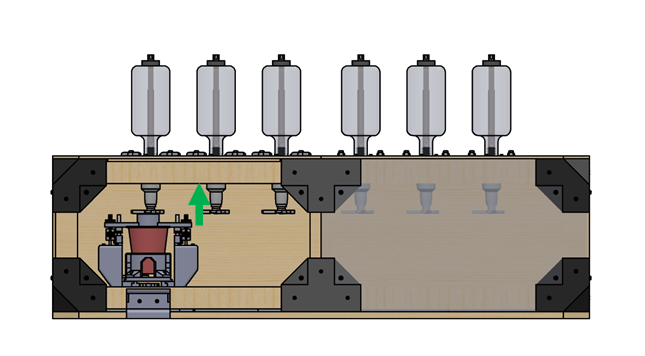
Media Wiki/Putting it all together/Z_Wiring_Motor_Check.png
