BenjaminMoff/MixUS/Media Wiki/XYZ Assembly/Assembly Picture/2040_insert_Screw_Type.png

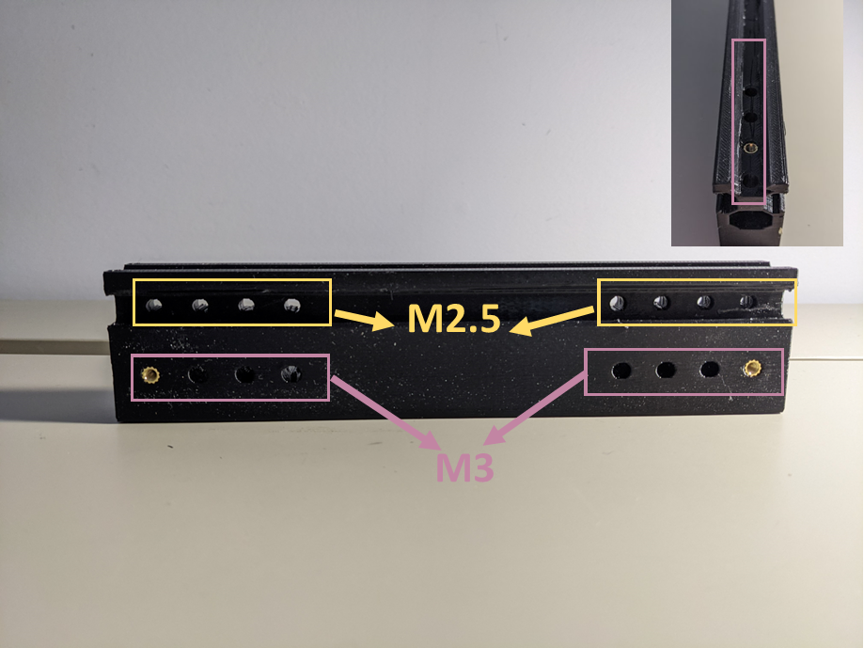
Media Wiki/XYZ Assembly/Assembly Picture/2040_insert_Screw_Type.png
