BenjaminMoff/MixUS/Media Wiki/XYZ Assembly/Assembly Picture/Connector_type.png

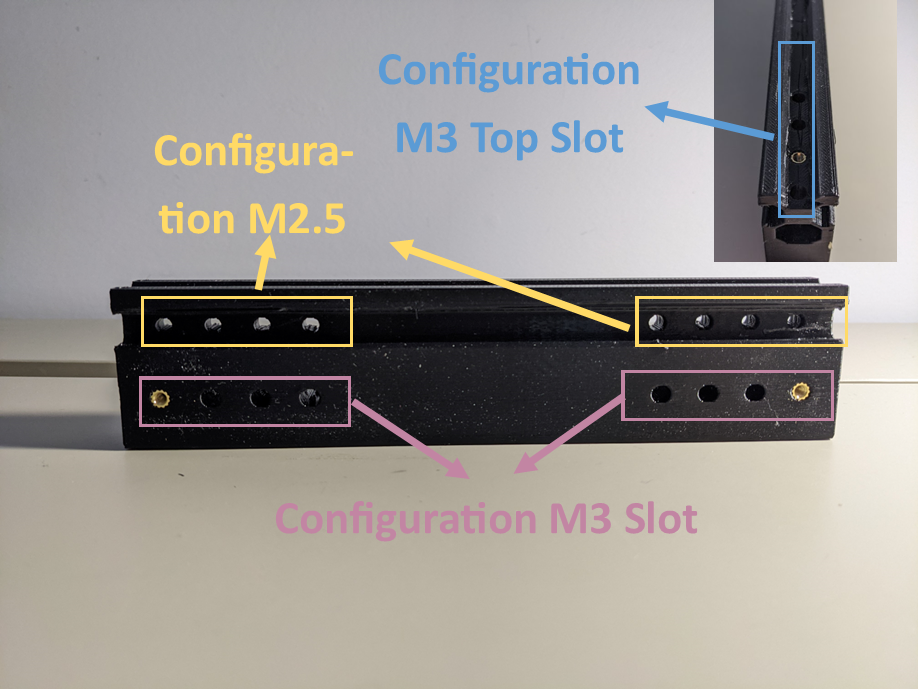
Media Wiki/XYZ Assembly/Assembly Picture/Connector_type.png
