BenjaminMoff/MixUS/Media Wiki/XYZ Assembly/Assembly Picture/Nema.png

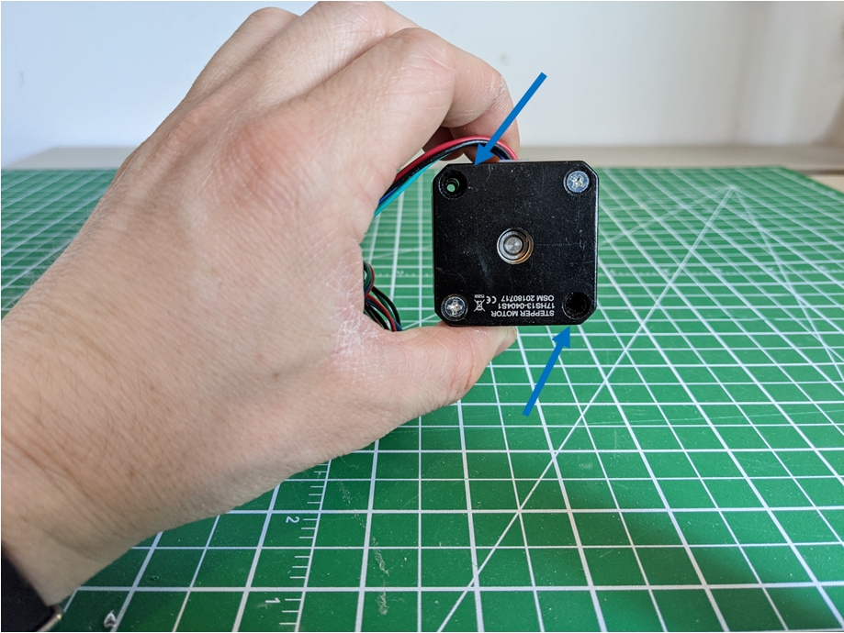
Media Wiki/XYZ Assembly/Assembly Picture/Nema.png
