BenjaminMoff/MixUS/Media Wiki/XYZ Assembly/Assembly Picture/Orientation_SubAss_X_Connector_Plate.png

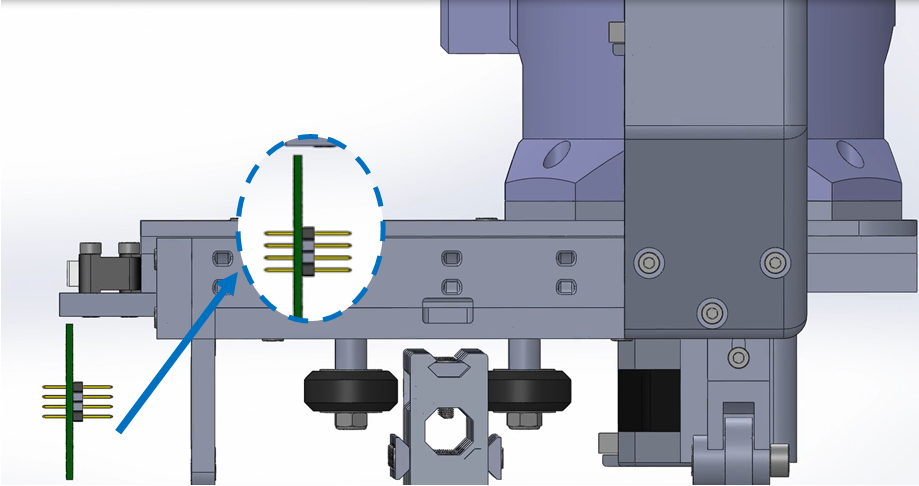
Media Wiki/XYZ Assembly/Assembly Picture/Orientation_SubAss_X_Connector_Plate.png
