BenjaminMoff/MixUS/Media Wiki/XYZ Assembly/Assembly Picture/Slot_Idler_Plate.png

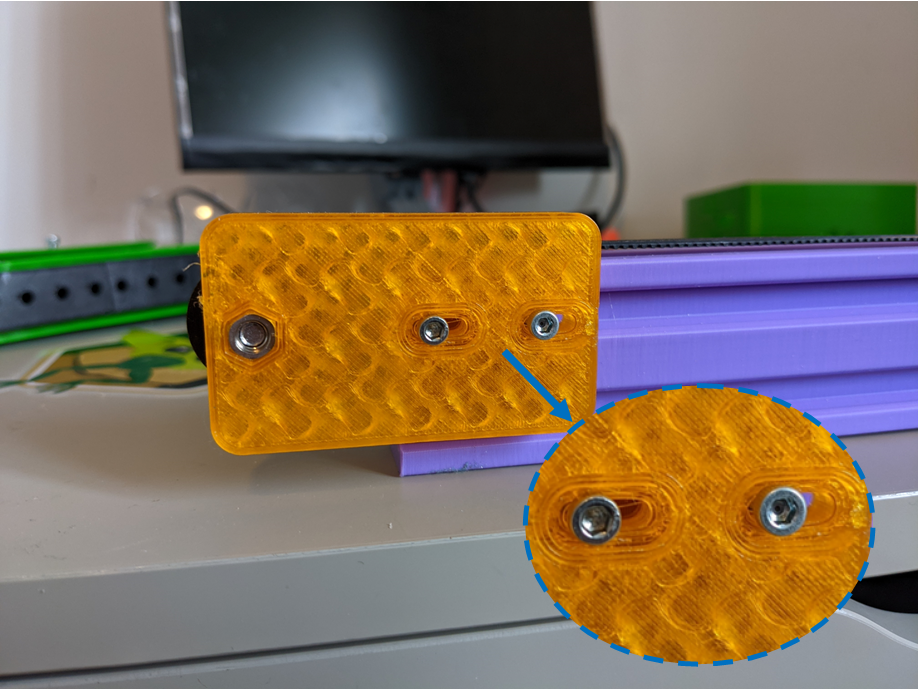
Media Wiki/XYZ Assembly/Assembly Picture/Slot_Idler_Plate.png
