BenjaminMoff/MixUS/Media Wiki/XYZ Assembly/Assembly Picture/Slot_X_Carriage.png

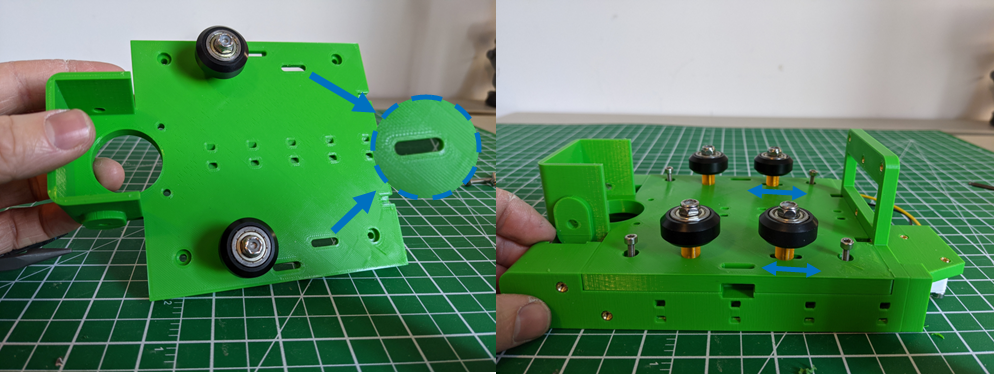
Media Wiki/XYZ Assembly/Assembly Picture/Slot_X_Carriage.png
