BenjaminMoff/MixUS/Media Wiki/XYZ Assembly/Assembly Picture/Slot_Y_Wheel.png

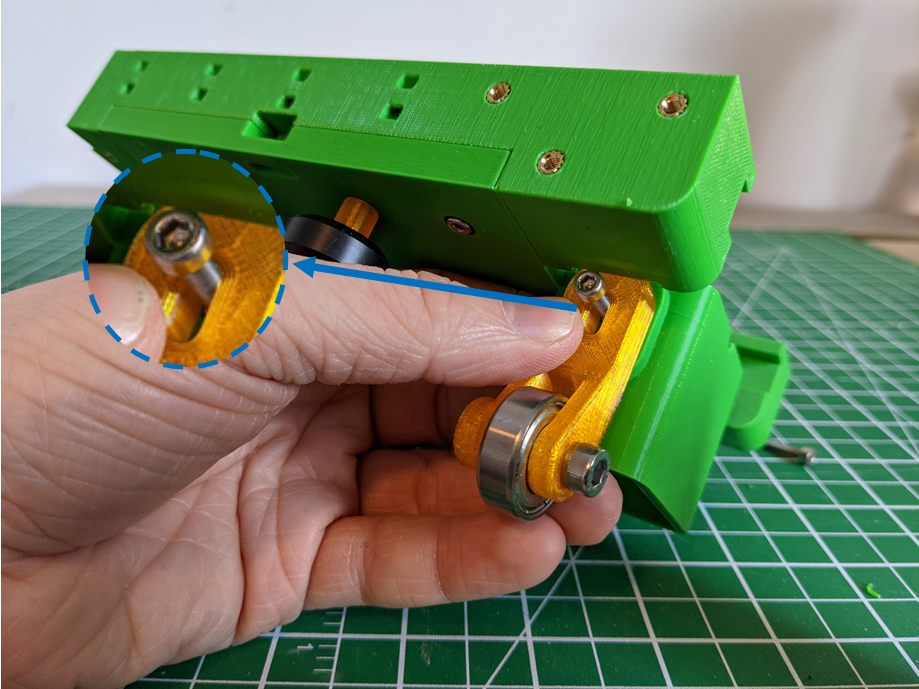
Media Wiki/XYZ Assembly/Assembly Picture/Slot_Y_Wheel.png
