BenjaminMoff/MixUS/Media Wiki/XYZ Assembly/Assembly Picture/Tie_Wrap_X_belt.png

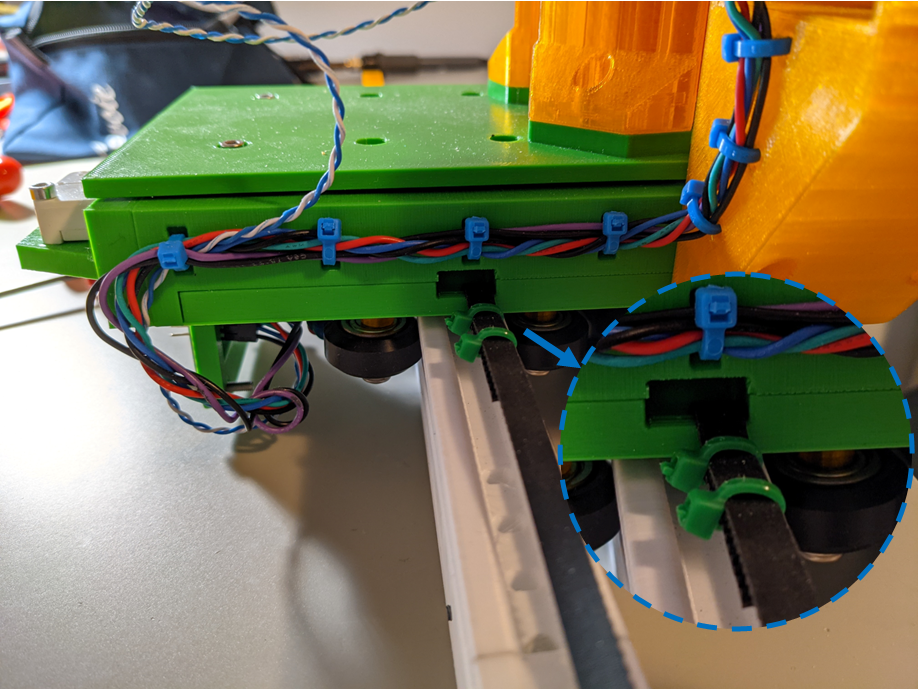
Media Wiki/XYZ Assembly/Assembly Picture/Tie_Wrap_X_belt.png
