BenjaminMoff/MixUS/Media Wiki/XYZ Assembly/Assembly Picture/V_Wheel_Centering.png

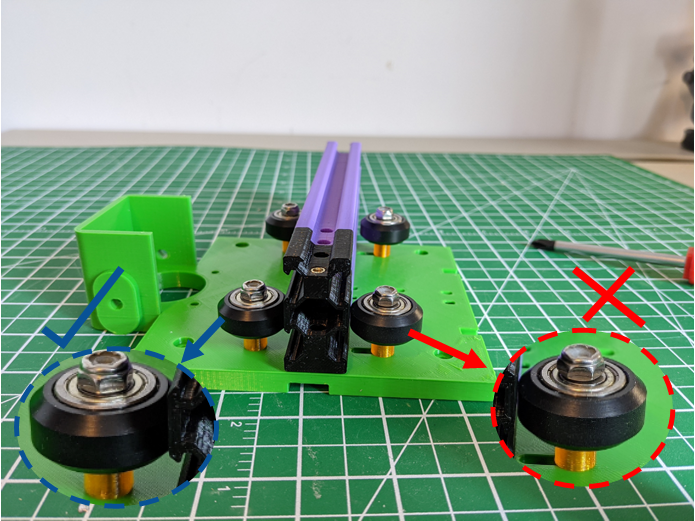
Media Wiki/XYZ Assembly/Assembly Picture/V_Wheel_Centering.png
