BenjaminMoff/MixUS/Media Wiki/XYZ Assembly/Assembly Picture/X_bracket_wire_diagram.png

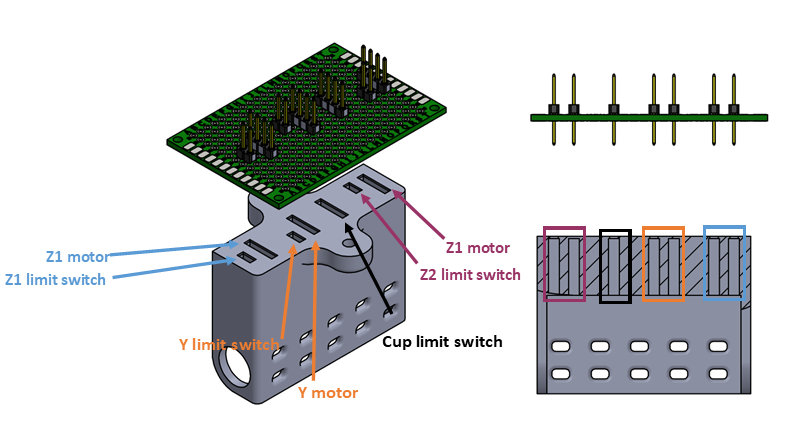
Media Wiki/XYZ Assembly/Assembly Picture/X_bracket_wire_diagram.png
