BenjaminMoff/MixUS/Media Wiki/XYZ Assembly/Assembly Picture/Y_Pinion_Insert.png

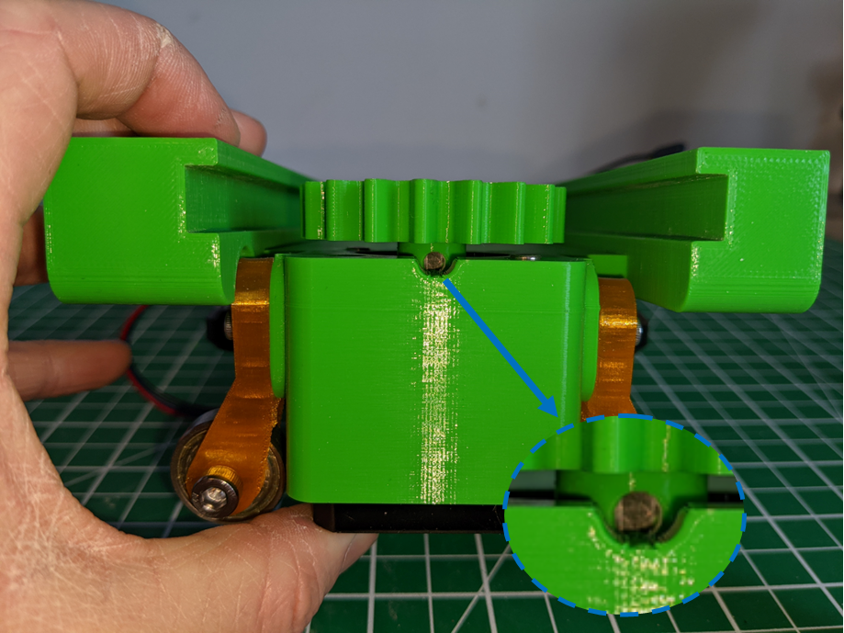
Media Wiki/XYZ Assembly/Assembly Picture/Y_Pinion_Insert.png
