BenjaminMoff/MixUS/Media Wiki/XYZ Assembly/Assembly Picture/Y_Wheel_Support_Centering.png

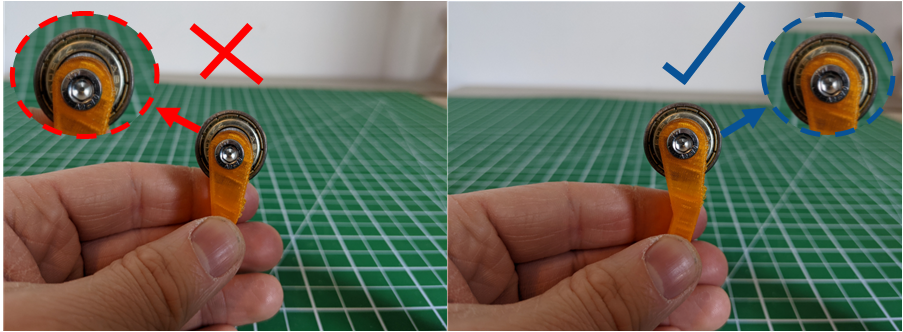
Media Wiki/XYZ Assembly/Assembly Picture/Y_Wheel_Support_Centering.png
