BenjaminMoff/MixUS/Media Wiki/XYZ Assembly/Assembly Picture/Z_Axis_drill.png

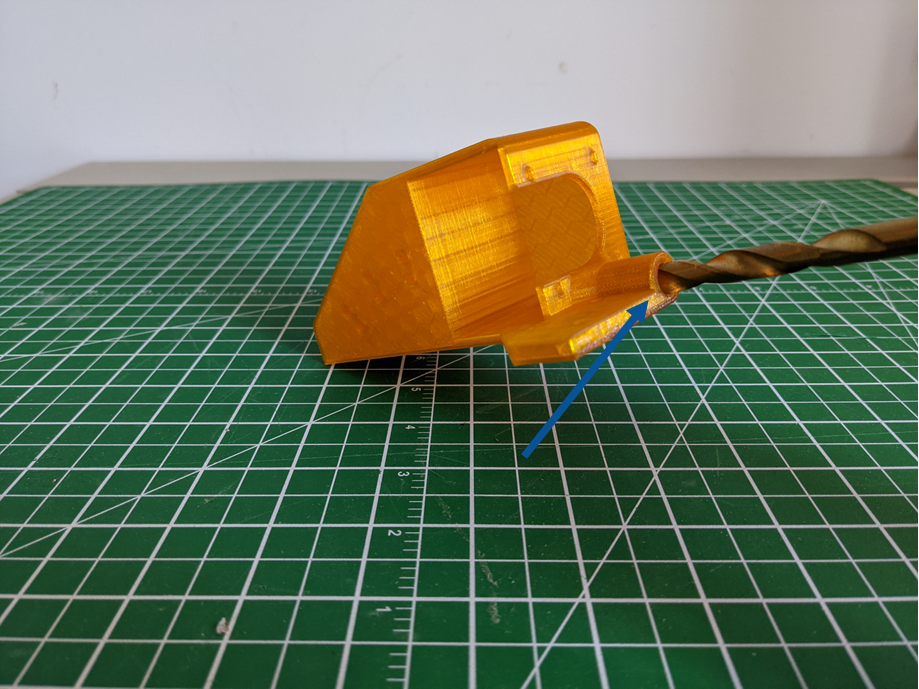
Media Wiki/XYZ Assembly/Assembly Picture/Z_Axis_drill.png
