BenjaminMoff/MixUS/Mechanical Assembly/CAD/SolidWorks/Assembly/Exploded_view/PDF/SubAss_Z_Motor_Bracket.PDF

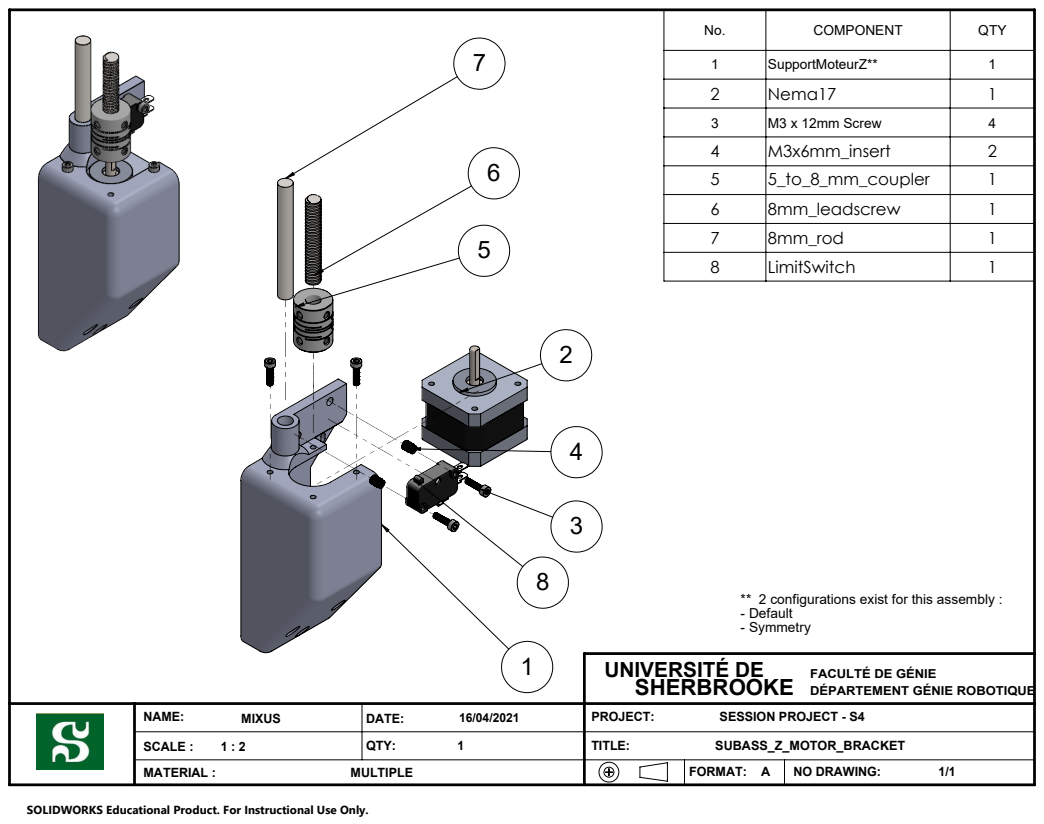
[picture p168: page 1]
FORMAT:; NO DRAWING:; SCALE :; MATERIAL :; UNIVERSITÉ DE; SESSION PROJECT - S4

No. | COMPONENT | QTY
1 | SupportMoteurZ** | 1
2 | Nema17 | 1
3 | M3 x 12mm Screw | 4
4 | M3x6mm_insert | 2
5 | 5_to_8_mm_coupler | 1
6 | 8mm_leadscrew | 1
7 | 8mm_rod | 1
8 | LimitSwitch | 1

** 2 configurations exist for this assembly :
- Default
- Symmetry

FACULTÉ DE GÉNIE
DÉPARTEMENT GÉNIE ROBOTIQUE

SOLIDWORKS Educational Product. For Instructional Use Only.
