BenjaminMoff/MixUS/Mechanical Assembly/CAD/SolidWorks/Assembly/Exploded_view/PDF/SubAss_Z_Pusher.PDF

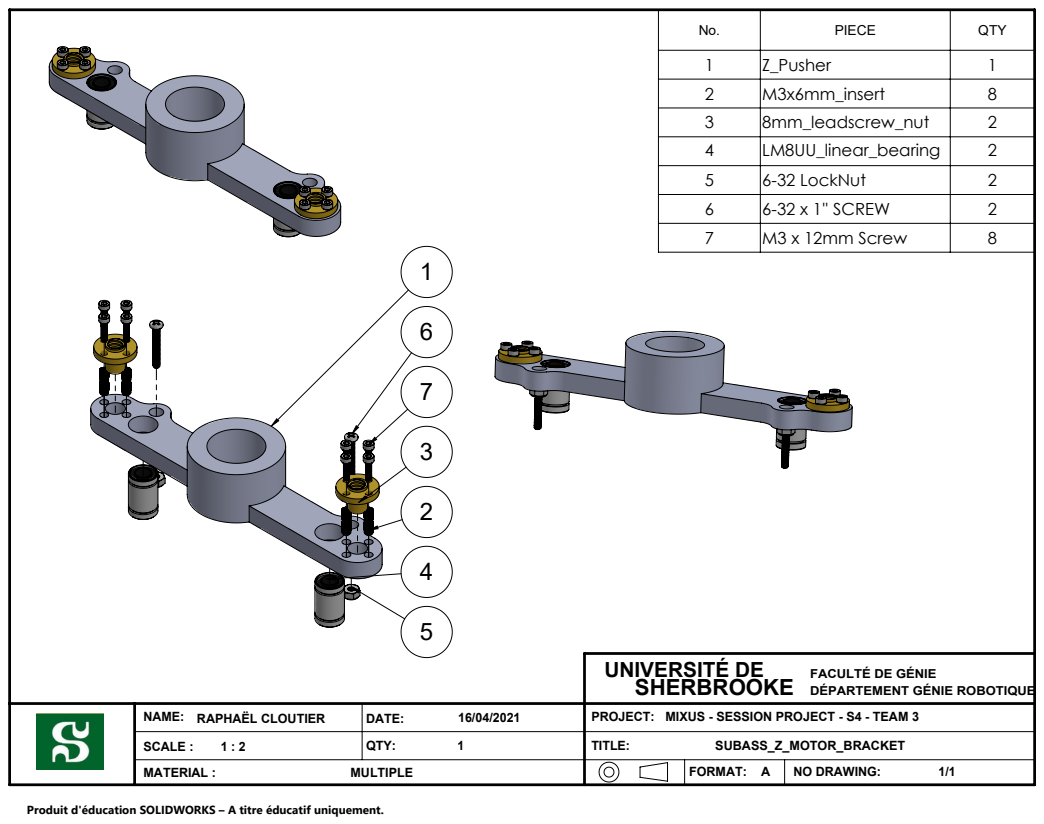
[picture p169: page 1]
FORMAT:; NO DRAWING:; SCALE :; MATERIAL :; RAPHAËL CLOUTIER; UNIVERSITÉ DE

No. | PIECE | QTY
1 | Z_Pusher | 1
2 | M3x6mm_insert | 8
3 | 8mm_leadscrew_nut | 2
4 | LM8UU_linear_bearing | 2
5 | 6-32 LockNut | 2
6 | 6-32 x 1'' SCREW | 2
7 | M3 x 12mm Screw | 8

FACULTÉ DE GÉNIE
DÉPARTEMENT GÉNIE ROBOTIQUE

MIXUS - SESSION PROJECT - S4 - TEAM 3
SUBASS_Z_MOTOR_BRACKET

Produit d'éducation SOLIDWORKS – A titre éducatif uniquement.
