BenjaminMoff/MixUS/Mechanical Assembly/CAD/SolidWorks/Frame materials/Drawing/PDF/Drawing_Frame_Acrylic.PDF

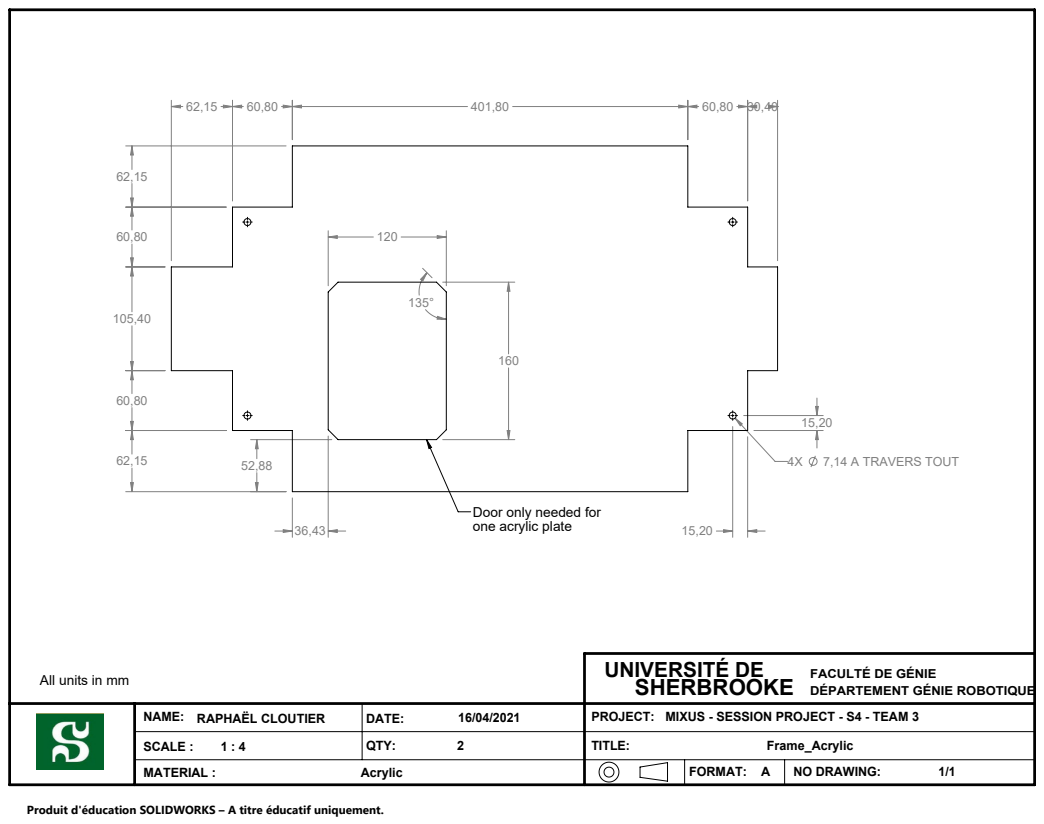
[picture p170: page 1]
4X 7,14 A TRAVERS TOUT; FORMAT:; NO DRAWING:; SCALE :; MATERIAL :; RAPHAËL CLOUTIER; UNIVERSITÉ DE

Door only needed for
one acrylic plate

FACULTÉ DE GÉNIE
DÉPARTEMENT GÉNIE ROBOTIQUE

All units in mm

MIXUS - SESSION PROJECT - S4 - TEAM 3

Produit d'éducation SOLIDWORKS – A titre éducatif uniquement.
