BenjaminMoff/MixUS/Mechanical Assembly/CAD/SolidWorks/Frame materials/Drawing/PDF/Drawing_Frame_Top_Plate_A.PDF

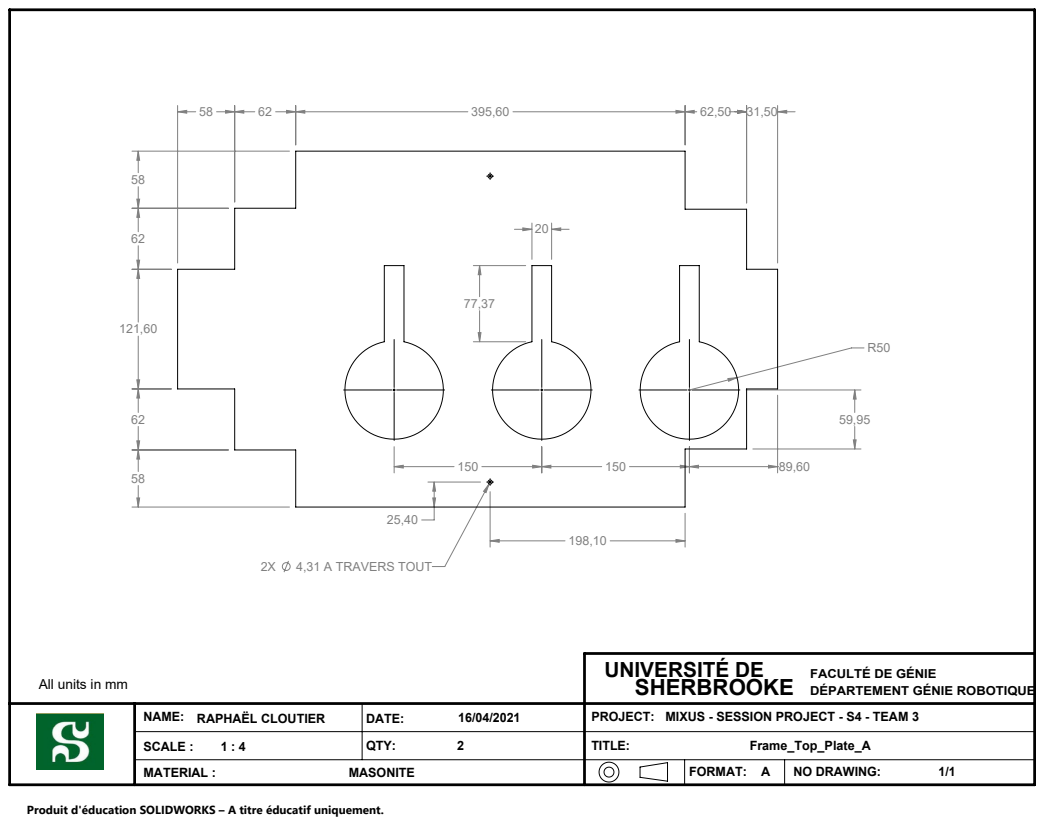
[picture p171: page 1]
2X 4,31 A TRAVERS TOUT; FORMAT:; NO DRAWING:; SCALE :; MATERIAL :; RAPHAËL CLOUTIER; UNIVERSITÉ DE

FACULTÉ DE GÉNIE
DÉPARTEMENT GÉNIE ROBOTIQUE

All units in mm

MIXUS - SESSION PROJECT - S4 - TEAM 3

Produit d'éducation SOLIDWORKS – A titre éducatif uniquement.
