BenjaminMoff/MixUS/Mechanical Assembly/CAD/SolidWorks/Assembly/Exploded_view/PDF/SubAss_Removable_Bottle_Support.PDF

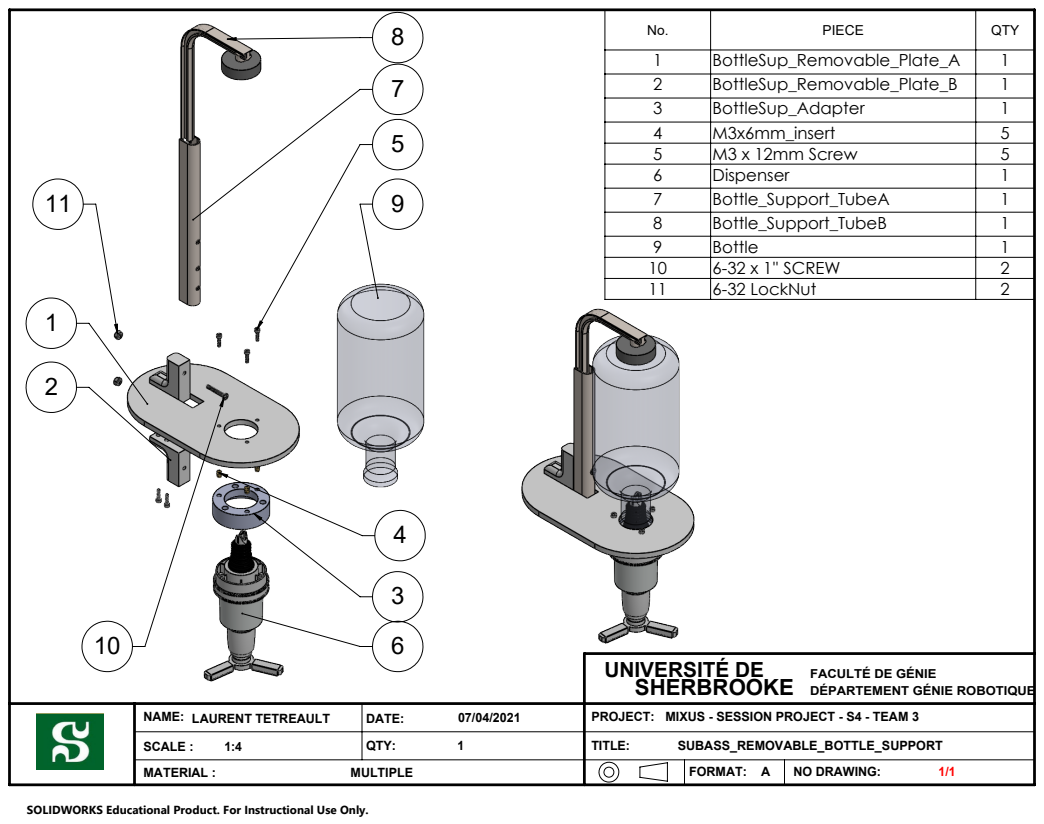
[picture p172: page 1]
FORMAT:; NO DRAWING:; SCALE :; MATERIAL :; LAURENT TETREAULT; UNIVERSITÉ DE

No. | PIECE | QTY
1 | BottleSup_Removable_Plate_A | 1
2 | BottleSup_Removable_Plate_B | 1
3 | BottleSup_Adapter | 1
4 | M3x6mm_insert | 5
5 | M3 x 12mm Screw | 5
6 | Dispenser | 1
7 | Bottle_Support_TubeA | 1
8 | Bottle_Support_TubeB | 1
9 | Bottle | 1
10 | 6-32 x 1'' SCREW | 2
11 | 6-32 LockNut | 2

FACULTÉ DE GÉNIE
DÉPARTEMENT GÉNIE ROBOTIQUE

MIXUS - SESSION PROJECT - S4 - TEAM 3
SUBASS_REMOVABLE_BOTTLE_SUPPORT

SOLIDWORKS Educational Product. For Instructional Use Only.
