BenjaminMoff/MixUS/code/Enums.py

from enum import Enum
from PyQt5 import QtCore
from PyQt5.QtCore import QSize
import os


class Liquid(Enum):
    """
    Enum of all liquids used in the application's drinks
    """
    def __new__(cls, *args, **kwds):
        value = len(cls.__members__) + 2
        obj = object.__new__(cls)
        obj._value_ = value
        return obj

    def __init__(self, string_name, is_alcoholized, is_filler):
        super().__init__()
        self.string_name = string_name
        self.is_alcoholized = is_alcoholized
        self.is_filler = is_filler

    # Used to describe an empty slot
    NONE = "Aucun", False, False

    # Liquors
    RUM = "Rhum", True, False
    VODKA = "Vodka", True, False
    TEQUILA = "Tequila", True, False
    GIN = "Gin", True, False
    WHISKEY = "Whiskey", True, False

    # Mixers
    TRIPLE_SEC = "Triple sec", True, False
    LIMONCELLO = "Limoncello", True, False
    BLUE_CURACAO = "Curacao bleu", True, False
    TONIC = "Tonique", False, False

    # Alcohol-free
    ORANGE_JUICE = "Jus d'orange", False, True
    CRANBERRY_JUICE = "Jus de canneberge", False, True
    COKE = "Coke", False, True
    SPRITE = "Sprite", False, True
    LEMONADE = "Limonade", False, True
    GINGER_ALE = "Ginger ale", False, True
    ICED_TEA = "Thé glacé", False, True

    @staticmethod
    def list():
        return list(map(lambda c: c.string_name, Liquid))

    @staticmethod
    def get_liquid_from_string_name(string_name):
        for liquid in Liquid:
            if liquid.string_name == string_name:
                return Liquid[liquid.name]
        raise ValueError("No Liquid contains this string_name: " + string_name)


class BottleSize(Enum):
    """
    Enum of accepted bottle sizes
    """
    ML_500 = 500
    ML_750 = 750
    ML_1000 = 1000
    ML_1140 = 1140

    @staticmethod
    def list():
        return list(map(lambda c: str(c.value), BottleSize))

    @staticmethod
    def ounces_to_ml(ounces):
        return 30 * ounces

    @staticmethod
    def ml_to_ounces(ml):
        return int(ml / 30)


# Paths to persistence files
class Paths(Enum):
    """
    Enum of relevant paths used in the application
    """
    BOTTLES = os.path.join(os.path.dirname(__file__),
                           "persistence/bottles.json")
    DRINKS = os.path.join(os.path.dirname(__file__),
                          "persistence/drinks.json")
    MAIN_MENU = os.path.join(os.path.dirname(__file__),
                             "ui/MainMenu.ui")
    BOTTLE_MENU = os.path.join(os.path.dirname(__file__),
                               "ui/BottleMenu.ui")
    DRINK_OPTION_MENU = os.path.join(os.path.dirname(__file__),
                                     "ui/DrinkOptionMenu.ui")
    MAINTENANCE_MENU = os.path.join(os.path.dirname(__file__),
                                    "ui/MaintenanceMenu.ui")
    MIXING_MENU = os.path.join(os.path.dirname(__file__),
                               "ui/MixingMenu.ui")


class Style(Enum):
    """
    Enum of stylesheets used in the application
    """
    label_background_color = "border: 1px solid;" \
                             "border-color: rgb(0, 0, 0);" \
                             "background-color: rgb(0, 167, 89);"
    button_color = "border-radius: 15px;" \
                   "background-color: rgb(255, 255, 255);"
    button_color_pressed = "border-radius: 15px;" \
                           "background-color: rgb(200, 200, 200);"

    layout_contour_color = "border: 1px solid;" \
                           "border-color: rgb(0, 0, 0);"

    drink_button = "border: 1px solid;" \
                   "border-radius: 20px;" \
                   "border-color: rgb(0, 0, 0);"

    combo_box = "border: 1px solid;" \
                "border-color: rgb(0, 0, 0);" \
                "background-color: rgb(240, 240, 240);"

    layout_background_color = "background-color: rgb(255, 255, 255);"

    combo_box_size = QSize(400, 59)
    drink_button_image_size = QSize(225, 370)
    drink_button_size = QSize(225, 415)
    menu_button_size = QSize(150, 75)


class HardwareConfig(Enum):
    """
    Specifies the pin used on the Raspberry Pi to connect the cup detection limit switch
    """
    limit_switch_pin = 11
